Strizzo/LumonTasker/cad/output/v28_integrated_top/README.md

# V28 — integrated printer-bay top

User requested cancellation of V27 to integrate the top now. V27 cancelled on layer1/805; device confirmed idle with heater targets zero. Clear the partial print, tower and purge line before any restart.

Top is now fused into the shell as a single solid. Removed the two top screw holes and matching heat-set bores. Finished outer height remains201mm. No separate top-cover print or twoM3x8 top screws required. Rear cover, retaining bars and rearward printer extraction remain unchanged. Front-down printing makes the top an upright wall, not a spanning roof; the earlier claim that a separate top was necessary was incorrect.

Retains V27 bottom support rise8.1mm and0.6mm total guide-gap reduction. Cradle remains a separate internal part. LED remains separate PETG insert. All solids/meshes valid and watertight; pairwise interference, rear extraction and switch swept clearance audits pass for the estimated body. These do not replace physical hardware validation.

Shell/logotype registered print coordinates updated together for the increased front-down footprint:175x192x161mm. Prepared shell,cradle+bars,rear cover,and optional bars-only projects. Slicer review and user/clear-bed confirmation required before replacement dispatch. No replacement sent yet.

## GUI slicing review

Integrated shell slices without a visible warning:10h20m,400.45g,805 layers,six filament changes. Supports15.88g (essentially unchanged from separate-top shell); added time/material is the top itself. Not dispatched. Await clear bed and user restart confirmation.

## Replacement started

User confirmed bed cleared. V28 integrated-top shell dispatched21 September17:04 local; device confirms active preparation and estimated finish22 September03:24. A2 light-grey body/A1 navy logo,bed leveling off,timelapse off.

## Print complete — 22 September

User confirms completion and provides a photo. Light grey ran out and was replaced by yellow; this shell is a fit-test prototype. User has only the earlier v26 trial cradle, not the refined cradle. Next prepared kit is `../v31_cradle_retention/02_cradle_and_bars.3mf`, with the approved taller/narrower cradle and a lower bar that captures its rear edge. No next print is authorized or dispatched. Final appearance should be redesigned/reviewed before spending the incoming white/navy filament on another shell.
