Strizzo/LumonTasker/cad/output/v36_outlet_alignment/README.md

# V36 physical outlet alignment correction

User reports V31 cradle fits well. With the printer seated in the printed prototype, move the enclosure paper aperture upward 3 mm; LED alignment is acceptable.

Applied to V35 desktop-terminal assembly: paper opening remains 90 x 14 mm, centre Z moves from 130.1 to 133.1 mm (edges 126.1–140.1 mm). Cradle, printer pose and LED stay unchanged. This is the latest physical correction, superseding earlier outlet-position estimates.

Shell is one valid watertight solid; unchanged volume and new opening clearance verified. All other components are copied unchanged from V35. STEP is ready for Fusion review; not yet imported/saved in Fusion. STL is in assembly coordinates, not a sliced print release. No print dispatched.

Current prototype remains useful for retention, feed/cut, cable and rear-service tests. Secured retention and those functional checks remain pending. Final shell waits for final filaments and remaining fit checks.
