Strizzo/LumonTasker/cad/output/v37_logo_spacing/README.md

# V37 logo spacing

Physical prototype feedback: N too close to O. Moved N 0.3 mm right; O–N bounding gap increases from 0.294 to 0.594 mm, comparable to neighbouring gaps. Updated shell recess together with coloured logo. All other geometry inherited unchanged from V36, including paper opening raised 3 mm and unchanged LED.

Shell valid single solid, logo components valid and mutually non-overlapping; shell and logo STL watertight. STEP ready for Fusion synchronization, not yet imported. Assembly STLs are not oriented/sliced print releases. No print dispatched.

User reports final filaments arrived. Exact brands/materials/colours and current slot loading asked, awaiting reply. Secured retention and feed/cut/service checks still pending.
