Strizzo/LumonTasker/cad/output/v43_integral_display_mounts/README.md

# V43 — four integral display mounts

The user proposes merging the four mount arms into the case because the display and attached Pi enter from the front. The revised CAD does this: four rear M3×6 screws into the display's original metal lugs, with no separate brackets, four case-side screws or four case-side heat-set inserts. The original 3.9 mm pad thickness and nominal2.1 mm thread engagement remain; actual screw length and manufacturer2.5 mm thread-depth limit must be respected.

The white recessed seat, accepted193.4×111.4 mm opening withR8.2 corners,1 mm glass recess and visible black glass border stay unchanged. No navy bezel or front lip. Rear screw access is required for assembly and service, then the unplugged display/Pi withdraw through the front.

CAD results: revised body is a single valid watertight solid. All four screw bores, head recesses and bearing lands pass. Exact front insertion/extraction sweeps of nominal glass, chassis and attached Pi are clear with the INTEGRAL MOUNTS LEFT IN PLACE. Component intersections and nominal Pi margin are clear. A simplified Pi block in the image is not a detailed connector model.

Separate flat brackets were useful for the inexpensive V40 mount test and print without supports. Integrated overhanging arms can require local supports in the full-body print; orientation/support removal still needs slicer review. No support-free claim is made for V43. The full body is not released for printing yet.

The already printed frame and four brackets are still useful to verify the unchanged metal lug pattern, bearing planes and screw engagement before fixing those details in a large case. Only the glass contour is physically confirmed so far. The precise mounting stack and actual tool/cable clearances remain unconfirmed.

The unresolved internal-power choice and provisional cable-volume/divider clash237.48 mm³ remain recorded. No assumption about purchased internal power hardware has been made. The navy printer-base job is unaffected; no new print sent and Fusion stays closed/latest savedV39.

Files: whole_enclosure_review.step; whole_enclosure_with_hardware.step; tub_left.step; audit.json; integral_mounts_rear.png (cropped CAD view of the panel from inside).
