Strizzo/LumonTasker/cad/output/v50_full_display_preflight/README.md

# V50 full-display preparation

V49 corner samples are physically accepted. Selected support gap:0.12mm.

## Ready sliced plate

`02_V50_display_roof_and_hatch.3mf` and matching `.gcode.3mf` contain the exact
existing aligned display roof and rear hatch. Bambu native slice/preview passes:
3h53m40s,118.64g,whiteA2 only. See `roof_hatch_slice_review.json`.
User confirmed plate clear; job sent and accepted by P1S, startup0/114, ETA22:47 local. Bed levelling/timelapseOFF. Bambu showed Finished 114/114 and user confirms both parts intact and plate clear on 25 September; see roof_hatch_print_dispatch.json.

## Full enclosure audit

`audit.json` records full-body front-down bounds and compact screwdriver access.
The body STL is for review only: legacy internal PSU mounts/divider remain.
Power architecture must be confirmed before changing them or releasing the
body. The entire full enclosure is NOT yet released. New display mount geometry
has not been synchronized into Fusion; roof/hatch match its savedV39 geometry.

Remaining parts:full display body,navy left base; separate PETG
LED diffuser if still needed. Accepted printer shell/cradle/base stay in use.
