Strizzo/LumonTasker/cad/output/v51_dc_inlet_panel/README.md

# V51 DC inlet glue panel

Current part: `dc_inlet_glue_panel.step`; current print project:
`02_DC_inlet_glue_panel.3mf`; native sliced file:
`02_DC_inlet_glue_panel.gcode.3mf`.

Nominal 10 mm socket neck, 10.2 mm bore, 5 mm inward sleeve, 2 mm radial wall.
20m27s estimate, 5.62 g cotton white PLA, no supports. Dispatched 26 September after user confirmed the
plate clear; cotton white A2, auto bed levelling and timelapse off. Completion
and physical fit are pending. Dry fit the socket and case recess before applying glue.

Files named `draft` or `DRAFT_NOT_RELEASED` are earlier superseded geometry,
without the user's final glue sleeve, and should not be printed.
