Strizzo/LumonTasker/cad/output/v51_petg_led_insert/README.md

# Translucent PETG LED insert — 26 September 2026

Final separate LED insert, using the geometry of the accepted earlier PLA fit trial.
No enclosure/Fusion geometry revision: the current saved full assembly contains this insert already.

- Physical material: translucent PETG, AMS A3 (user confirmed).
- Device A3 registration verified: PETG, K0.040.
- Project has one filament, extruder 1. Map it to **A3** when sending.
- Native slice: 11m30s total, 0.61 g, 17 layers at 0.2 mm.
- Generic PETG preset: 255 C nozzle / 70 C textured PEI bed.
- Flange down; no support or prime tower; 0.8 mm front face.
- Native preview: continuous first-layer flange, short bridge at layer 14, complete face.
- **Dispatched** after user confirms whole plate clear; Device shows matching job accepted and bed heating. Completion and optical fit pending.
- At launch: bed levelling and timelapse OFF, as requested.

Insert from the inside/rear into the printer bay's light opening. The wider flange
stays inside. Dry-fit and check the blue light before placing small adhesive points
on the flange; keep glue away from the light cavity and native buttons.
