Strizzo/LumonTasker/cad/output/v18_colored.png

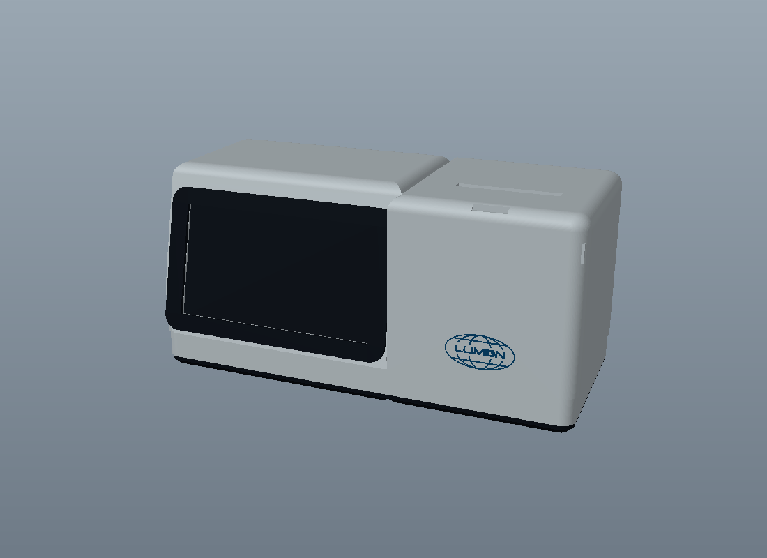
cad/output/v18_colored.png
