Strizzo/LumonTasker/cad/output/v18_screen_corner.png

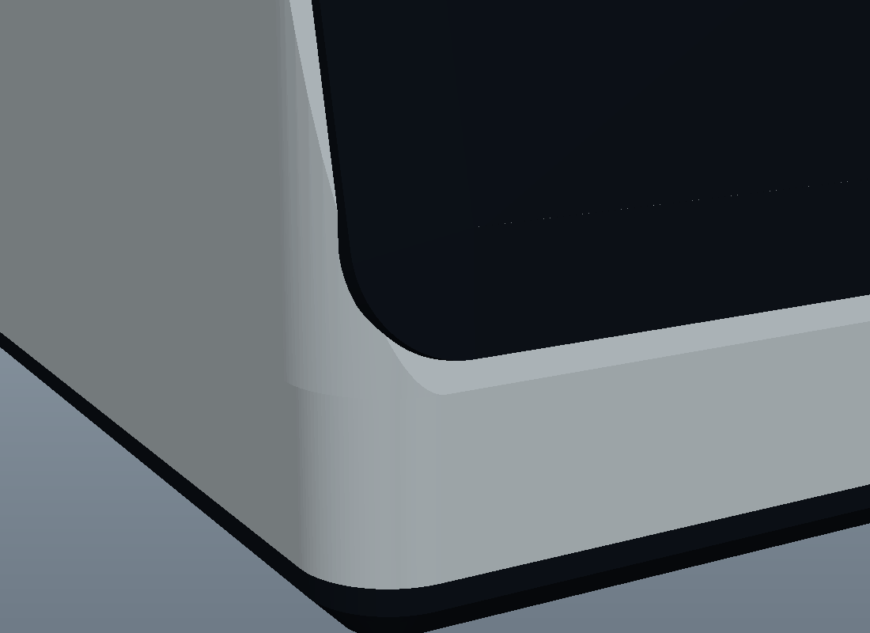
cad/output/v18_screen_corner.png
