Strizzo/LumonTasker/cad/output/v19/exploded.png

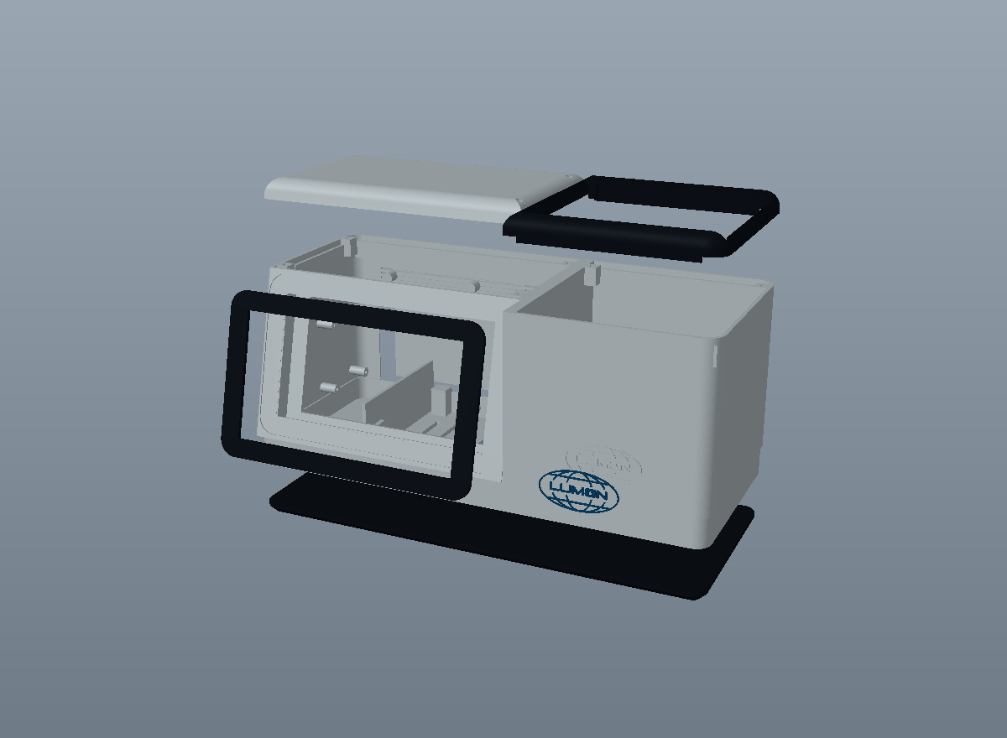
cad/output/v19/exploded.png
