Strizzo/LumonTasker/cad/output/v20_front/exploded.png

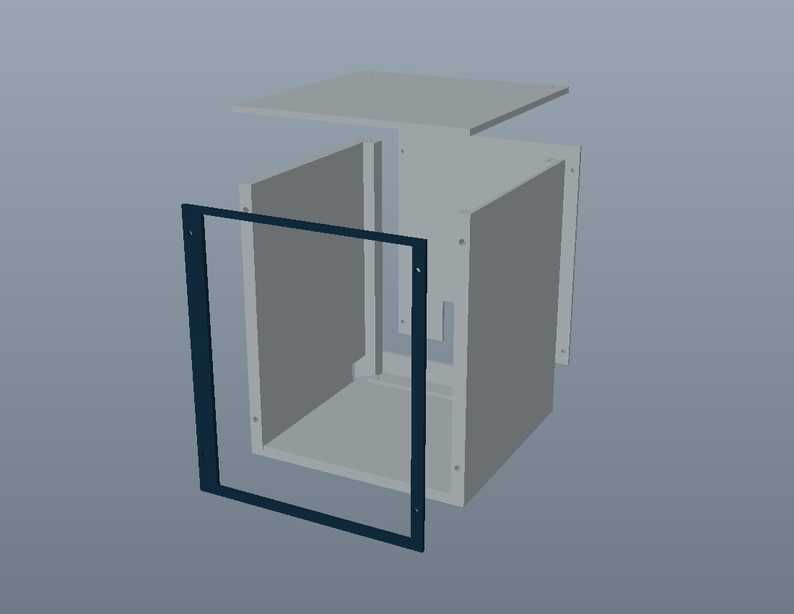
cad/output/v20_front/exploded.png
