Strizzo/LumonTasker/cad/output/v20_integral_front/exploded.png

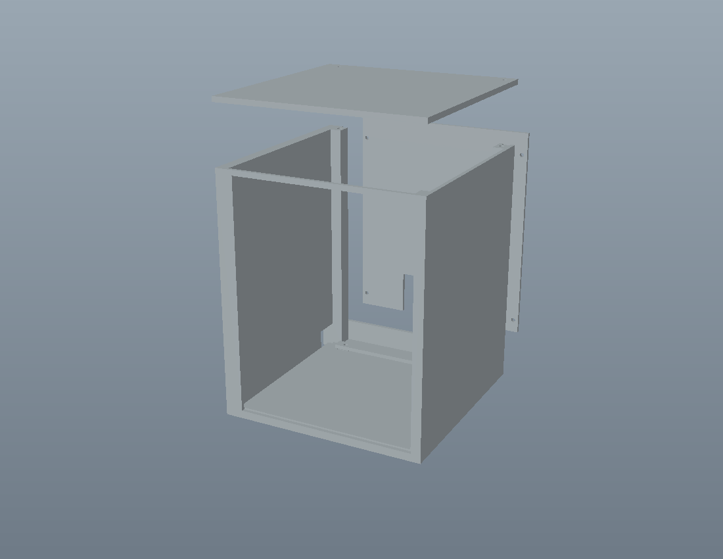
cad/output/v20_integral_front/exploded.png
