Strizzo/LumonTasker/cad/output/v21_rear_loading/rear_retention.png

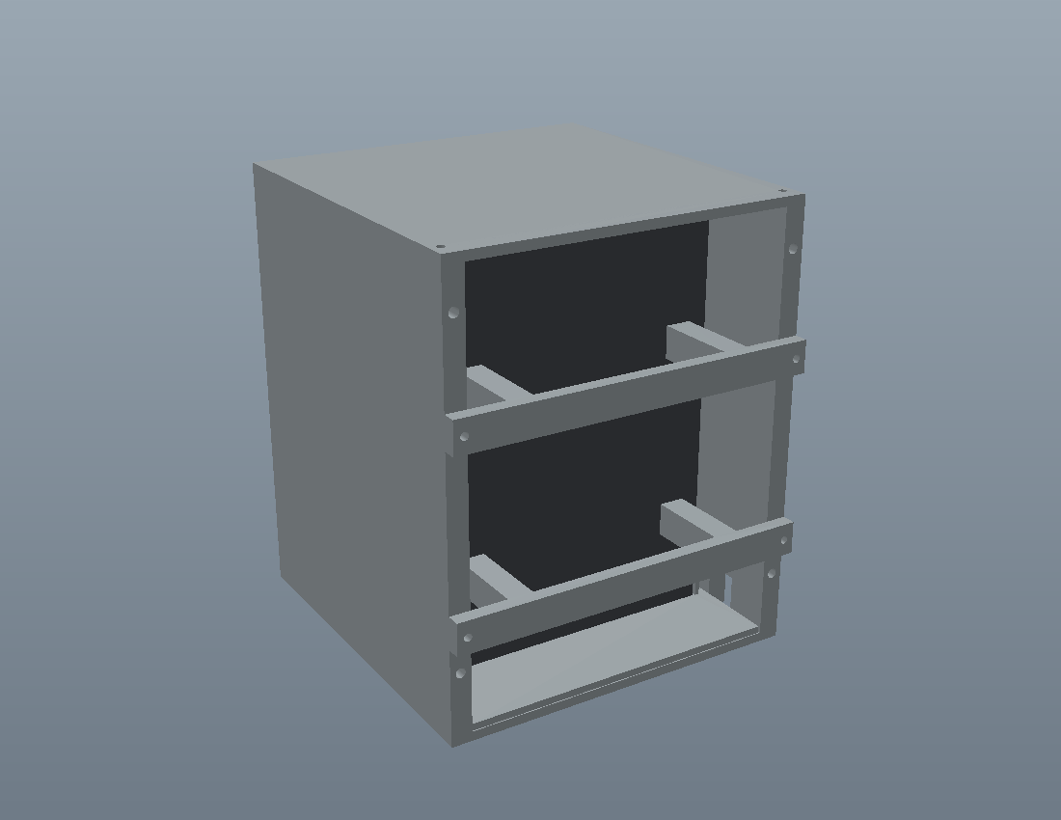
cad/output/v21_rear_loading/rear_retention.png
