Strizzo/LumonTasker/cad/output/v22_printer_bay/finished_appearance_concept.png

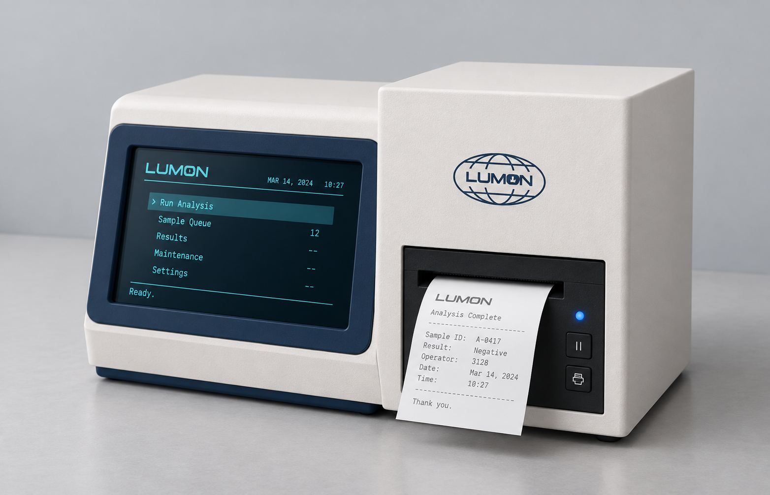
cad/output/v22_printer_bay/finished_appearance_concept.png
