Strizzo/LumonTasker/cad/output/v23_upper_output/exploded.png

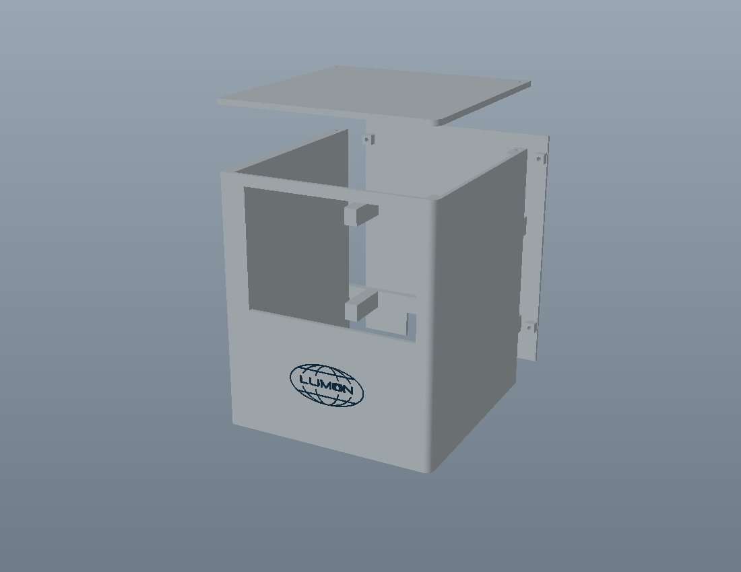
cad/output/v23_upper_output/exploded.png
