Strizzo/LumonTasker/cad/output/v23_upper_output/finished_appearance_concept.png

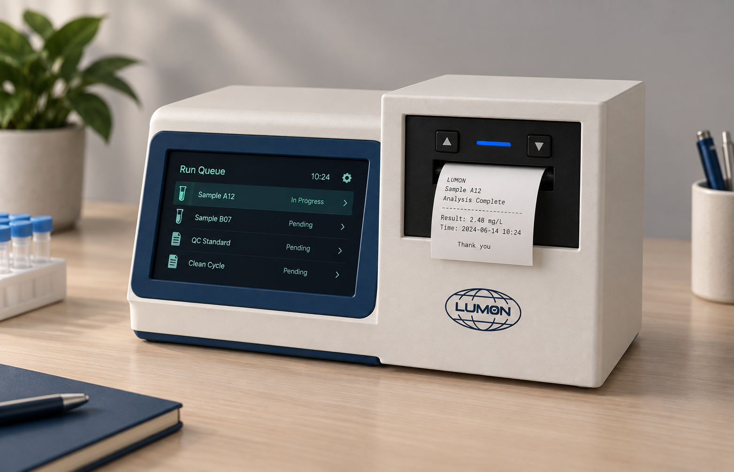
cad/output/v23_upper_output/finished_appearance_concept.png
