Strizzo/LumonTasker/cad/output/v23_upper_output/whole_enclosure_study.png

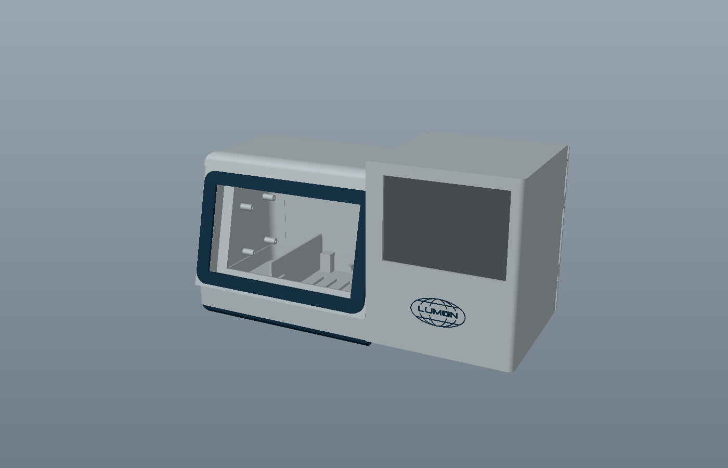
cad/output/v23_upper_output/whole_enclosure_study.png
