Strizzo/LumonTasker/cad/output/v28_integrated_top/exploded.png

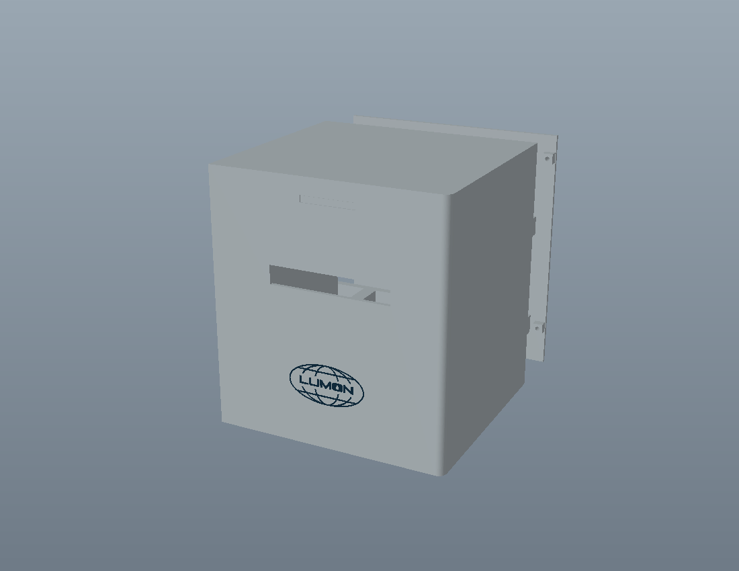
cad/output/v28_integrated_top/exploded.png
