Strizzo/LumonTasker/cad/output/v28_integrated_top/whole_enclosure_review.png

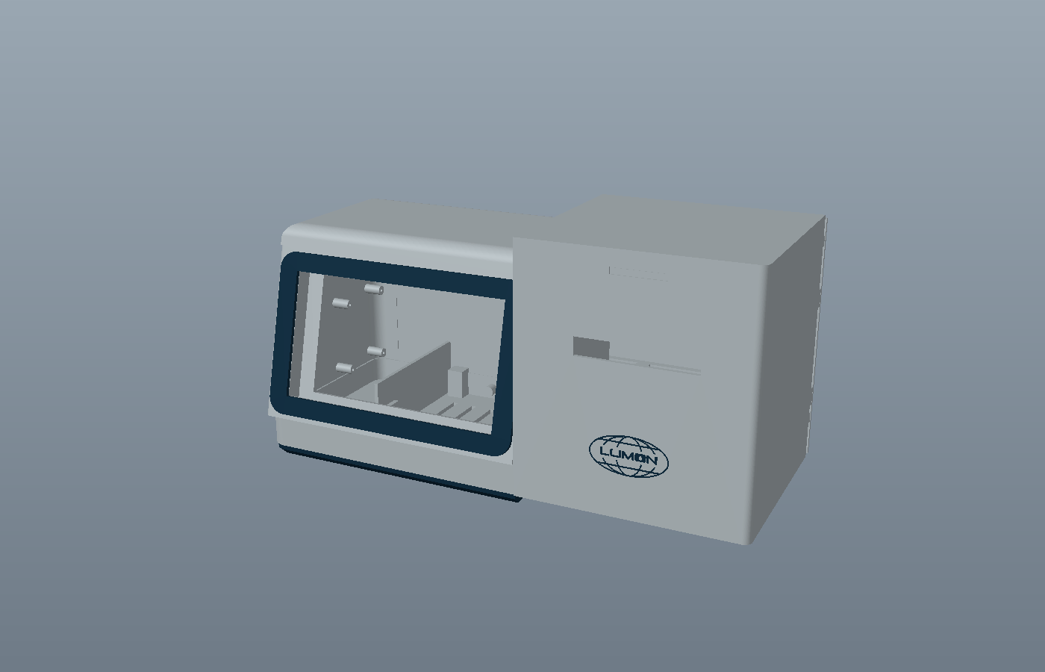
cad/output/v28_integrated_top/whole_enclosure_review.png
