Strizzo/LumonTasker/cad/output/v31_cradle_retention/cradle_retention_detail.png

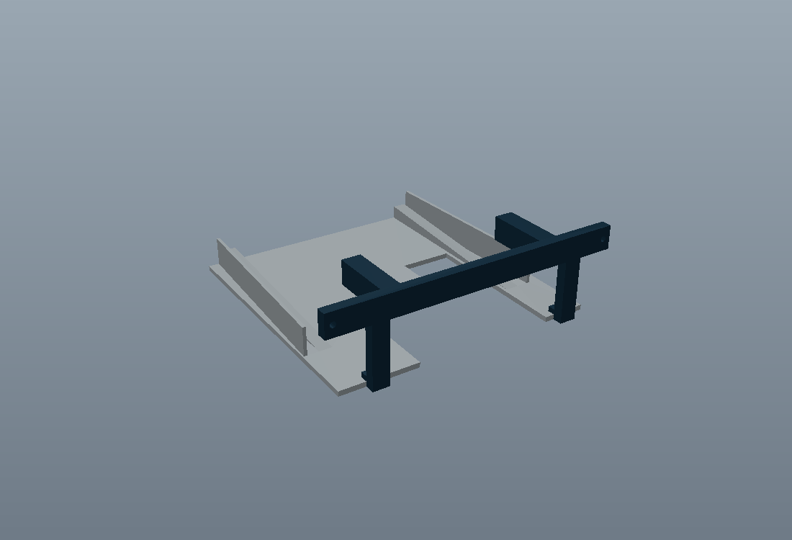
cad/output/v31_cradle_retention/cradle_retention_detail.png
