Strizzo/LumonTasker/cad/output/v32_equal_height/before_front.png

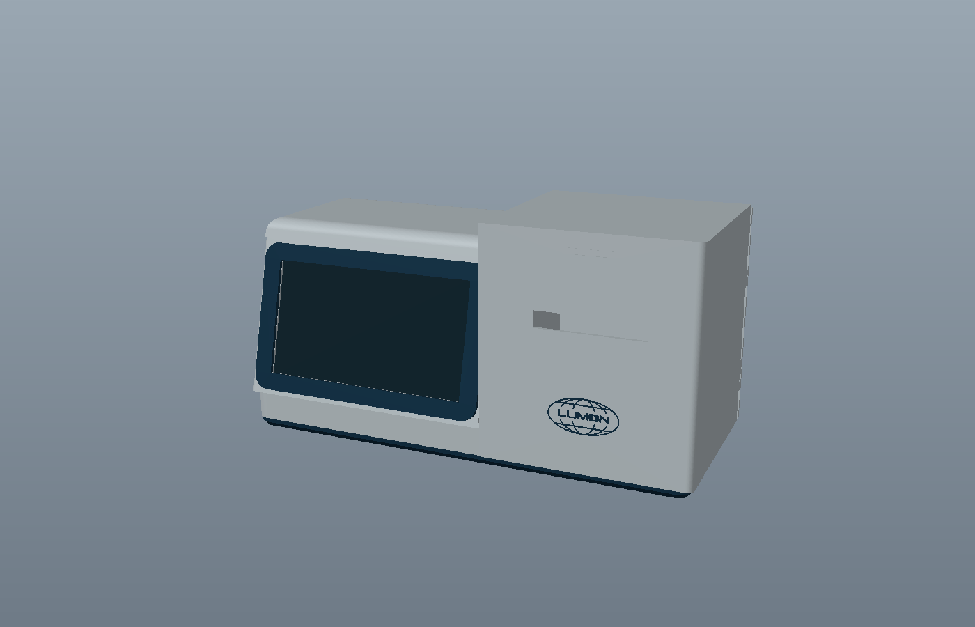
cad/output/v32_equal_height/before_front.png
