Strizzo/LumonTasker/cad/output/v32_equal_height/equal_height_rear.png

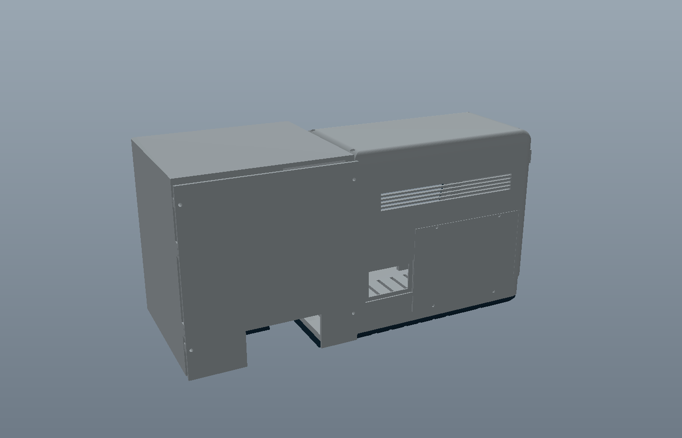
cad/output/v32_equal_height/equal_height_rear.png
