Strizzo/LumonTasker/cad/output/v33_unified_body/before_front.png

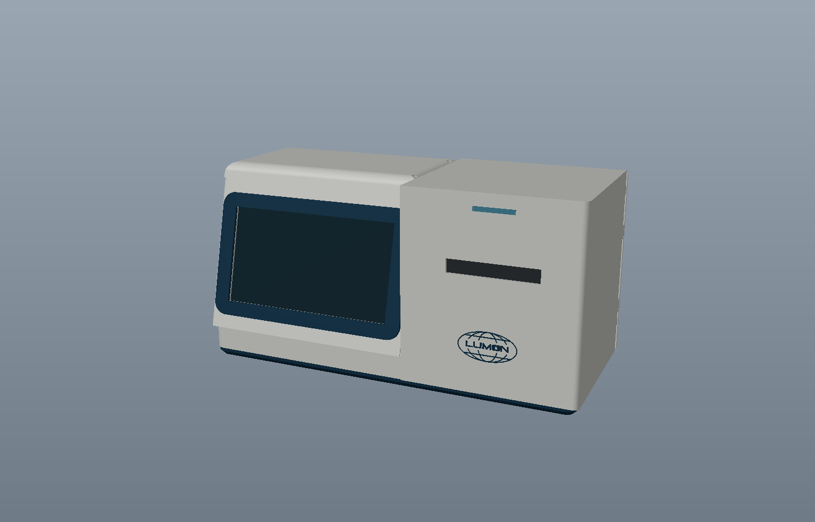
cad/output/v33_unified_body/before_front.png
