Strizzo/LumonTasker/cad/output/v33_unified_body/unified_front.png

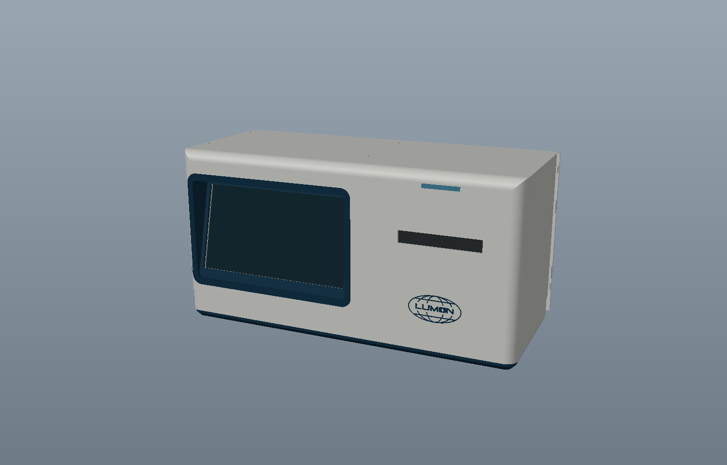
cad/output/v33_unified_body/unified_front.png
