Strizzo/LumonTasker/cad/output/v33_unified_body/unified_rear.png

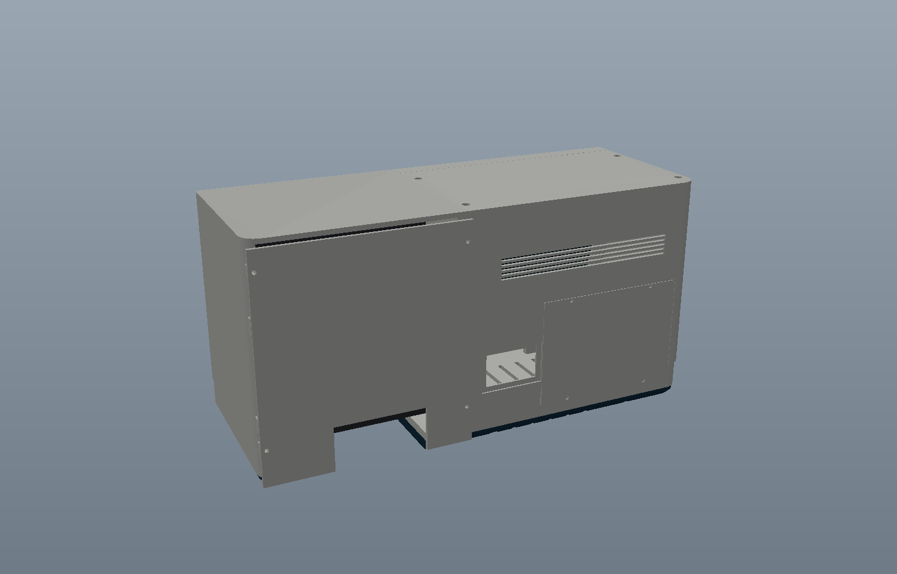
cad/output/v33_unified_body/unified_rear.png
