Strizzo/LumonTasker/cad/output/v33_unified_body/unified_straight_front.png

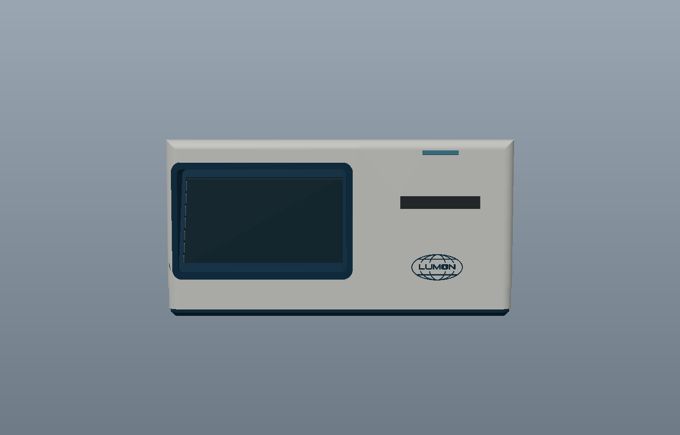
cad/output/v33_unified_body/unified_straight_front.png
