Strizzo/LumonTasker/cad/output/v34_sloped_connected_roof/sloped_roof.png

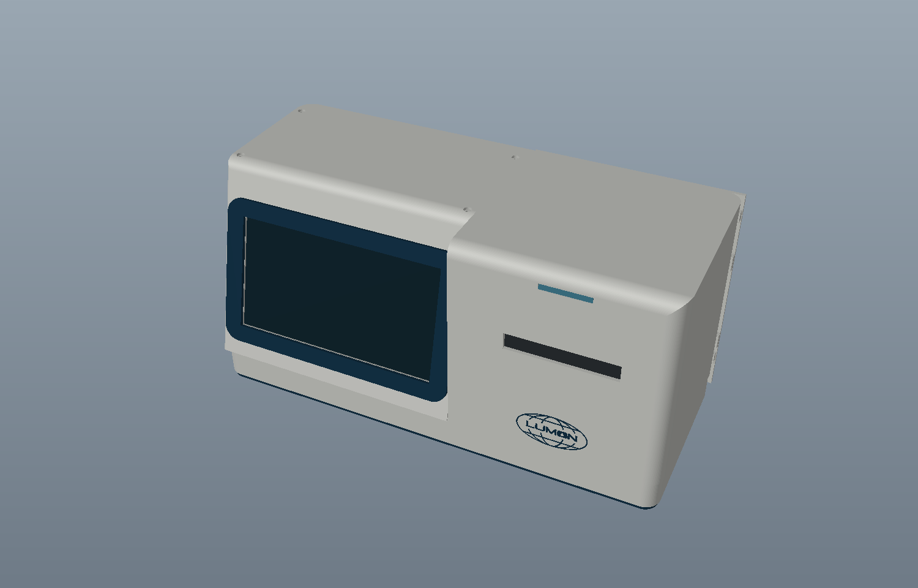
cad/output/v34_sloped_connected_roof/sloped_roof.png
