Strizzo/LumonTasker/cad/output/v35_desktop_terminal/sloped_rear.png

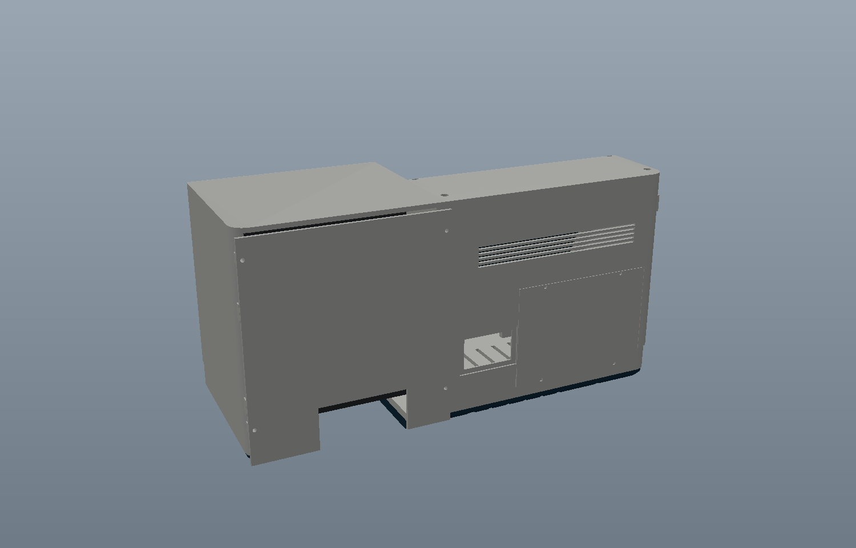
cad/output/v35_desktop_terminal/sloped_rear.png
