Strizzo/LumonTasker/cad/output/v38_integrated_rear/cover_inside.png

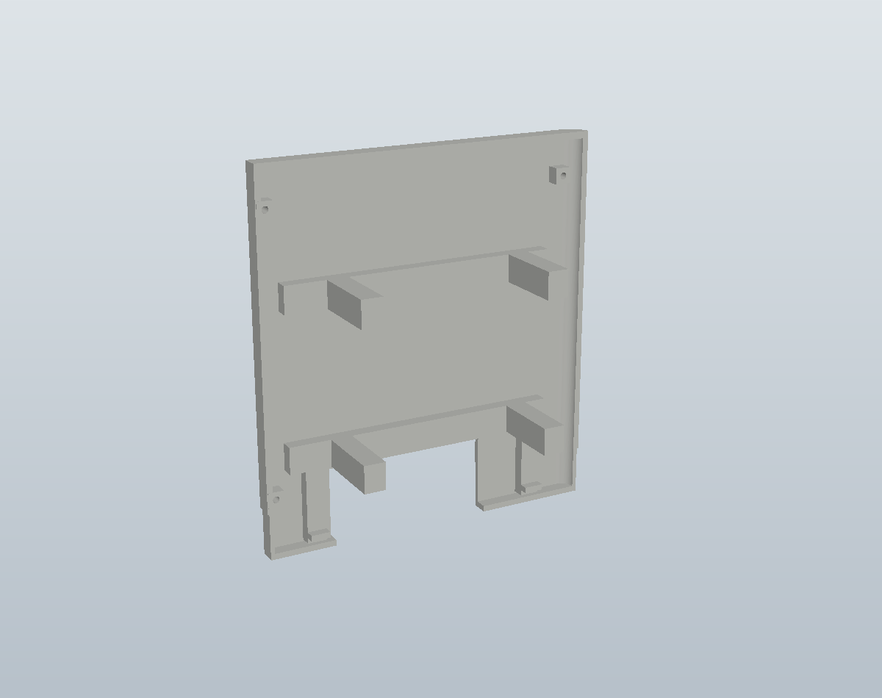
cad/output/v38_integrated_rear/cover_inside.png
