Strizzo/LumonTasker/cad/output/v38_integrated_rear/rear_exploded.png

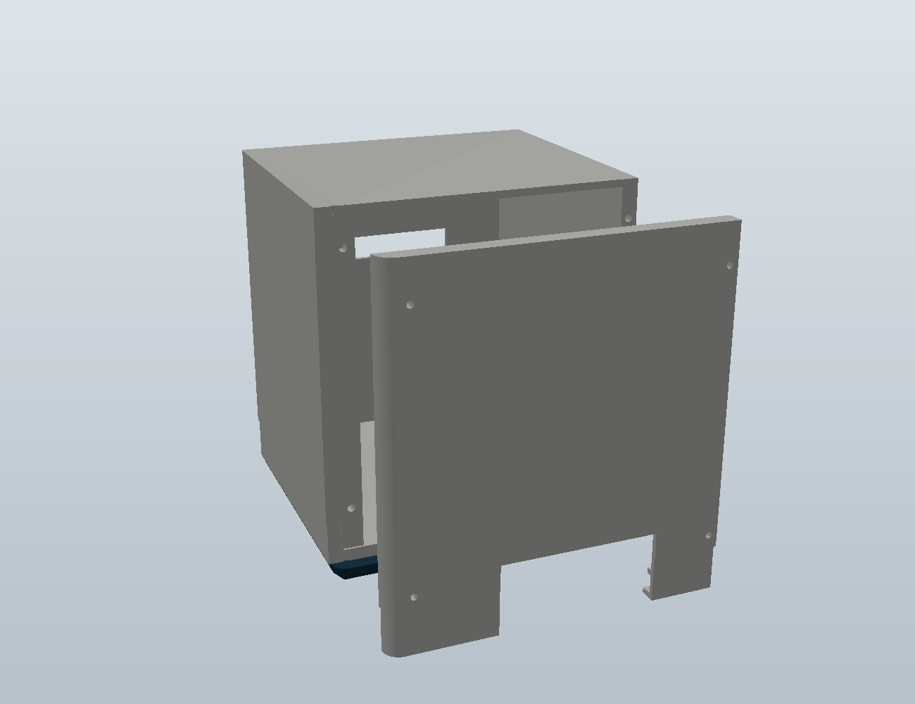
cad/output/v38_integrated_rear/rear_exploded.png
