Strizzo/LumonTasker/cad/output/v39_aligned_rear/aligned_rear.png

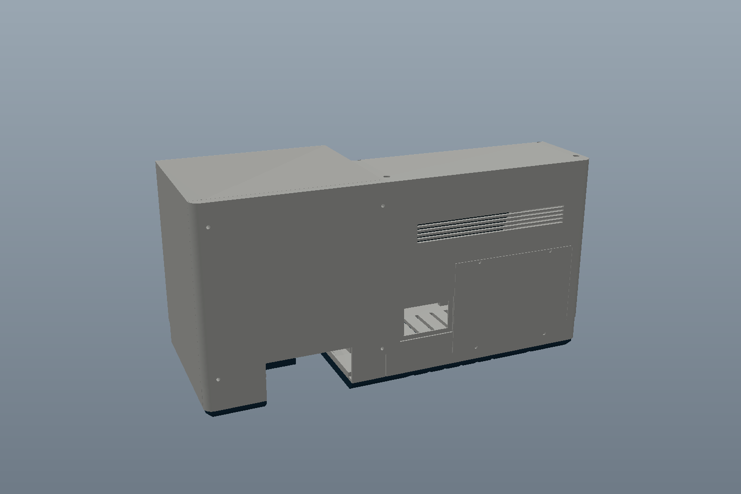
cad/output/v39_aligned_rear/aligned_rear.png
