Strizzo/LumonTasker/cad/output/v39_aligned_rear/aligned_roof.png

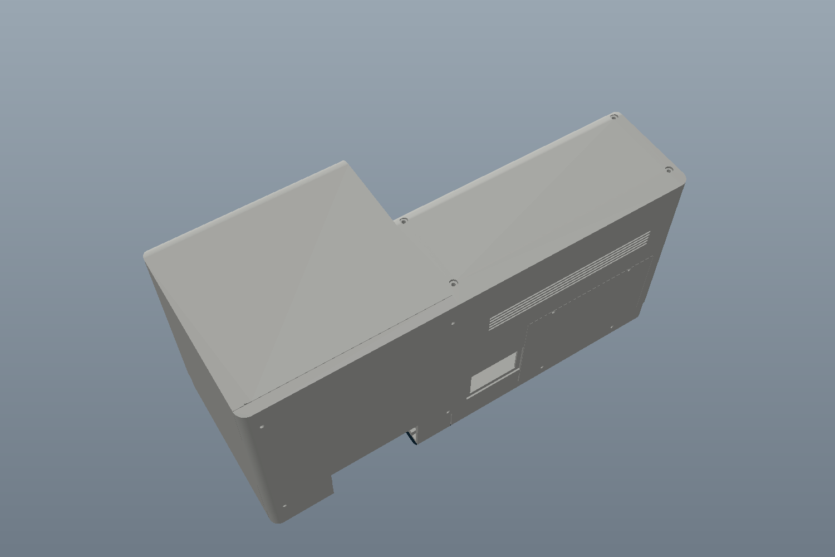
cad/output/v39_aligned_rear/aligned_roof.png
