Strizzo/LumonTasker/cad/output/v40_display_mount/fit_kit_rear.png

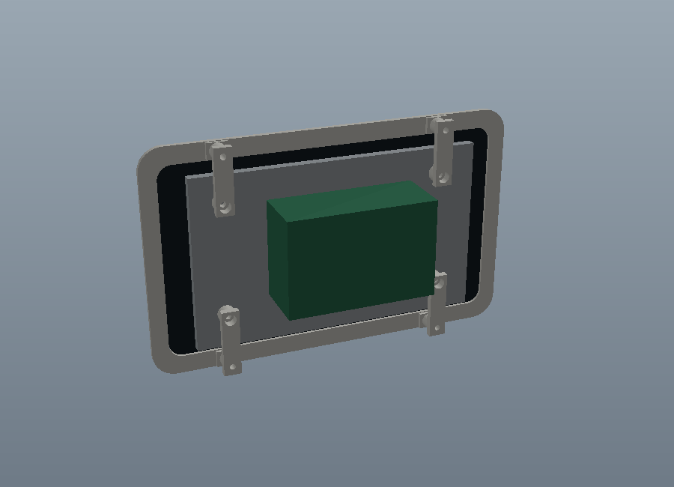
cad/output/v40_display_mount/fit_kit_rear.png
