Strizzo/LumonTasker/cad/output/v41_recessed_glass/recessed_glass_front.png

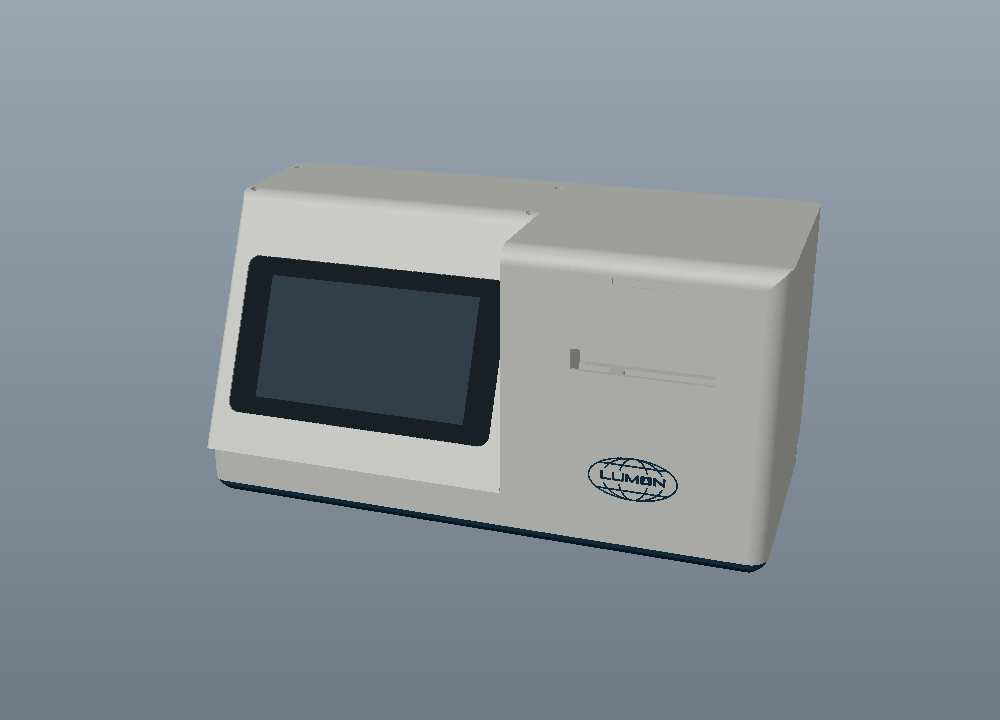
cad/output/v41_recessed_glass/recessed_glass_front.png
