Strizzo/LumonTasker/cad/output/v46_display_seat_fit/integral_fit_frame.png

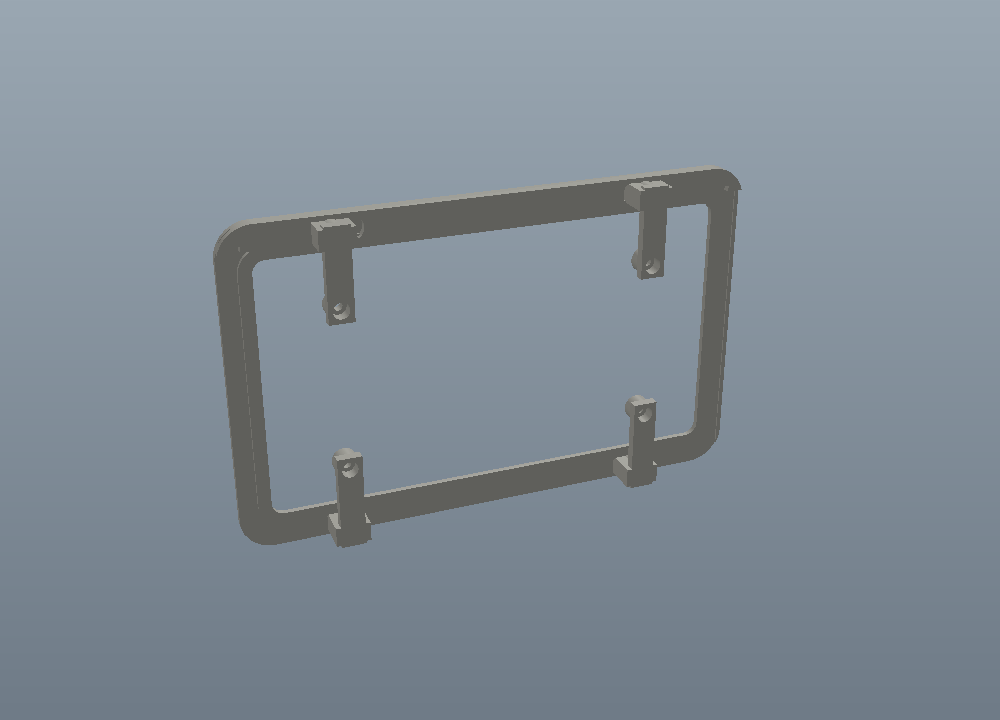
cad/output/v46_display_seat_fit/integral_fit_frame.png
