Strizzo/LumonTasker/cad/output/v50_full_display_preflight/body_front_down_audit.png

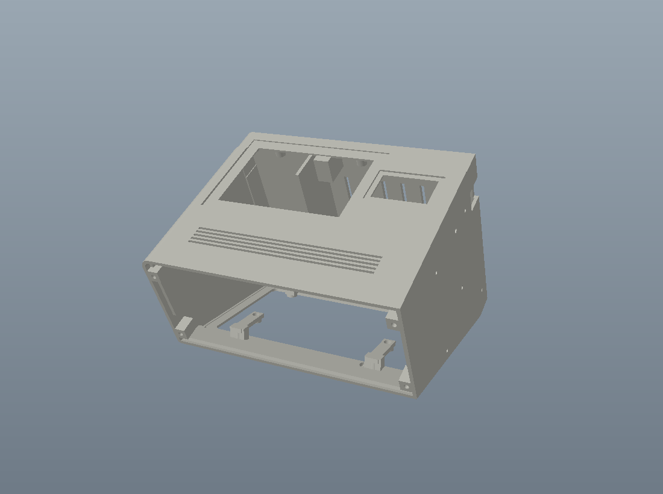
cad/output/v50_full_display_preflight/body_front_down_audit.png
