Strizzo/LumonTasker/cad/output/v50_full_display_preflight/body_rear_audit.png

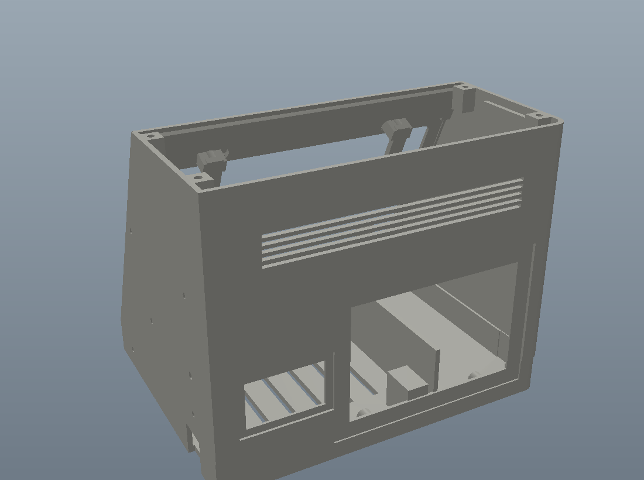
cad/output/v50_full_display_preflight/body_rear_audit.png
