Strizzo/LumonTasker/cad/output/v51_dc_inlet_panel/dc_inlet_glue_panel_front.png

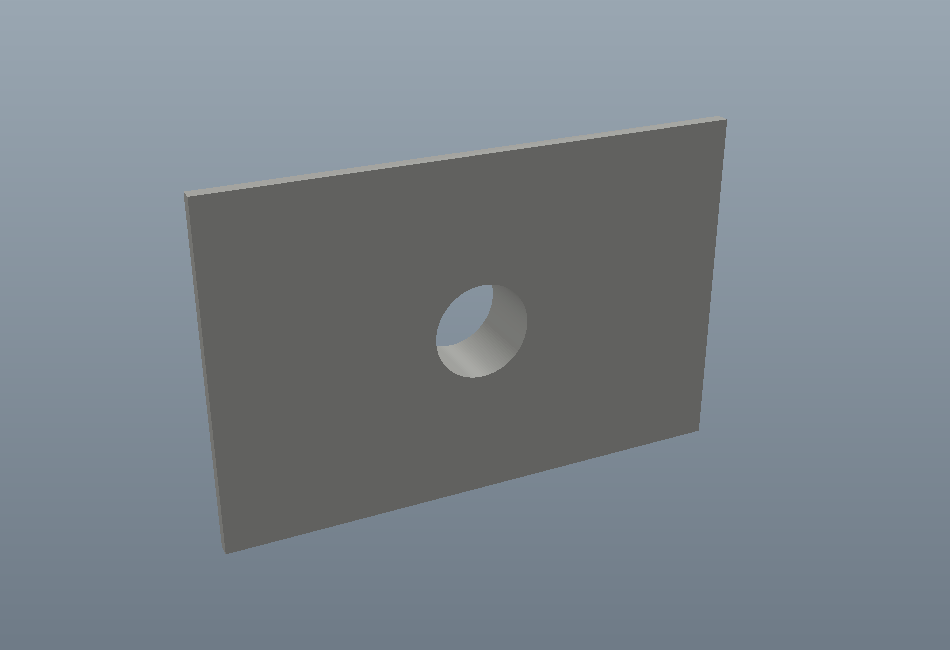
cad/output/v51_dc_inlet_panel/dc_inlet_glue_panel_front.png
