Strizzo/LumonTasker/cad/output/v51_dc_inlet_panel/dc_inlet_glue_panel_rear.png

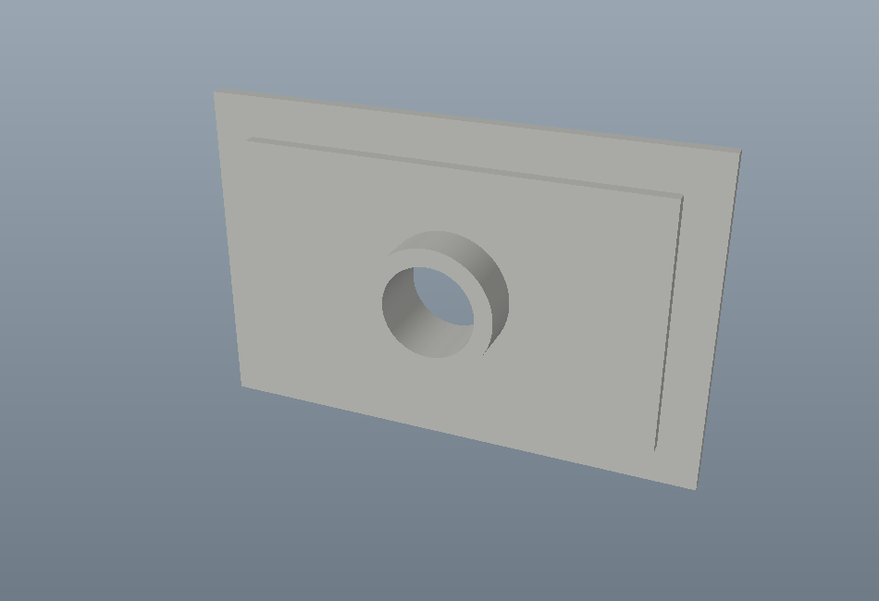
cad/output/v51_dc_inlet_panel/dc_inlet_glue_panel_rear.png
