Strizzo/LumonTasker/files/blockout_views.png

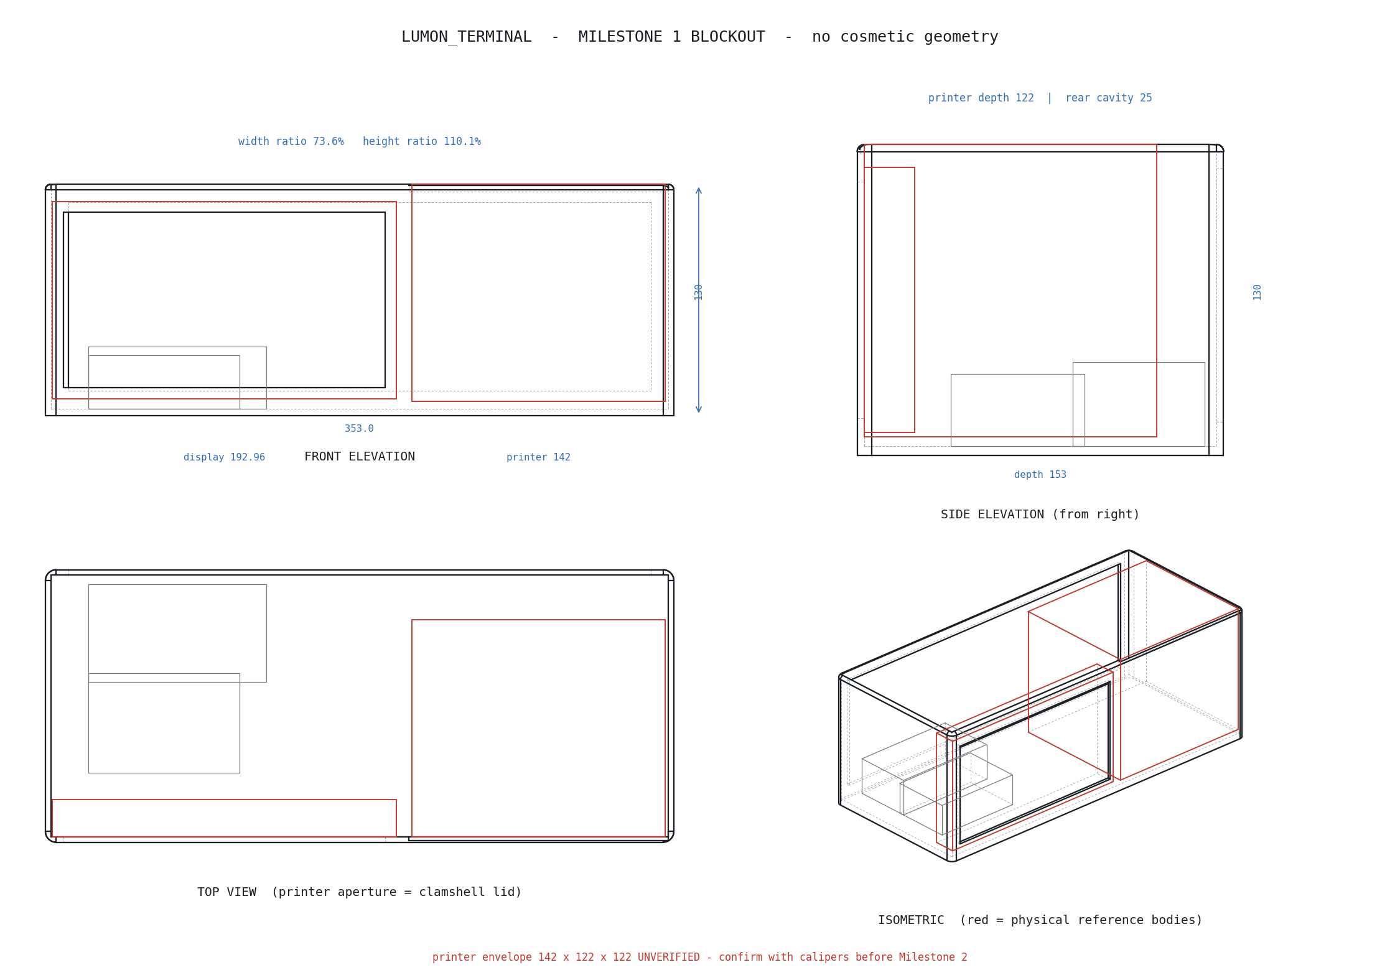
files/blockout_views.png
