Strizzo/LumonTasker/files/corner_zoom.png

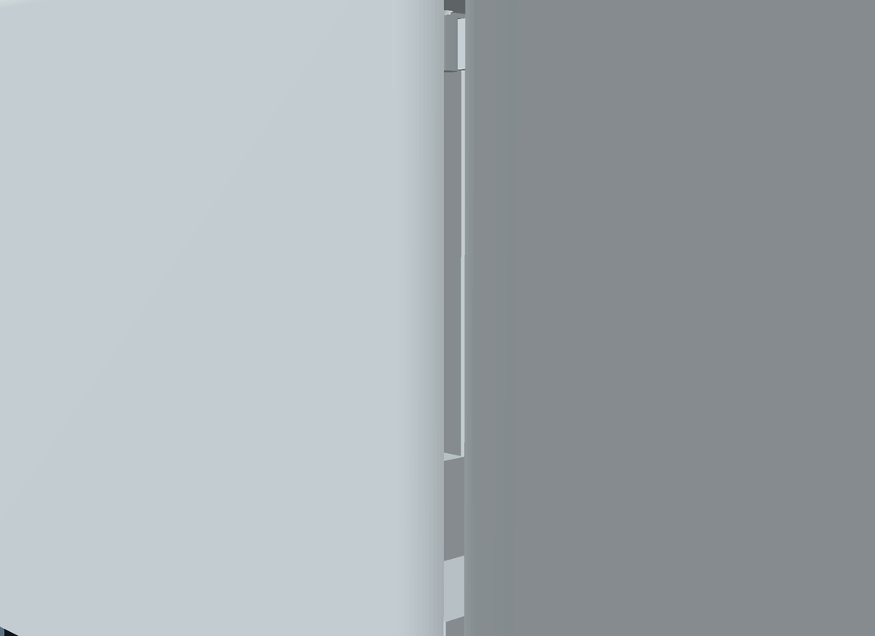
files/corner_zoom.png
