Strizzo/LumonTasker/files/lockup_90mm.png

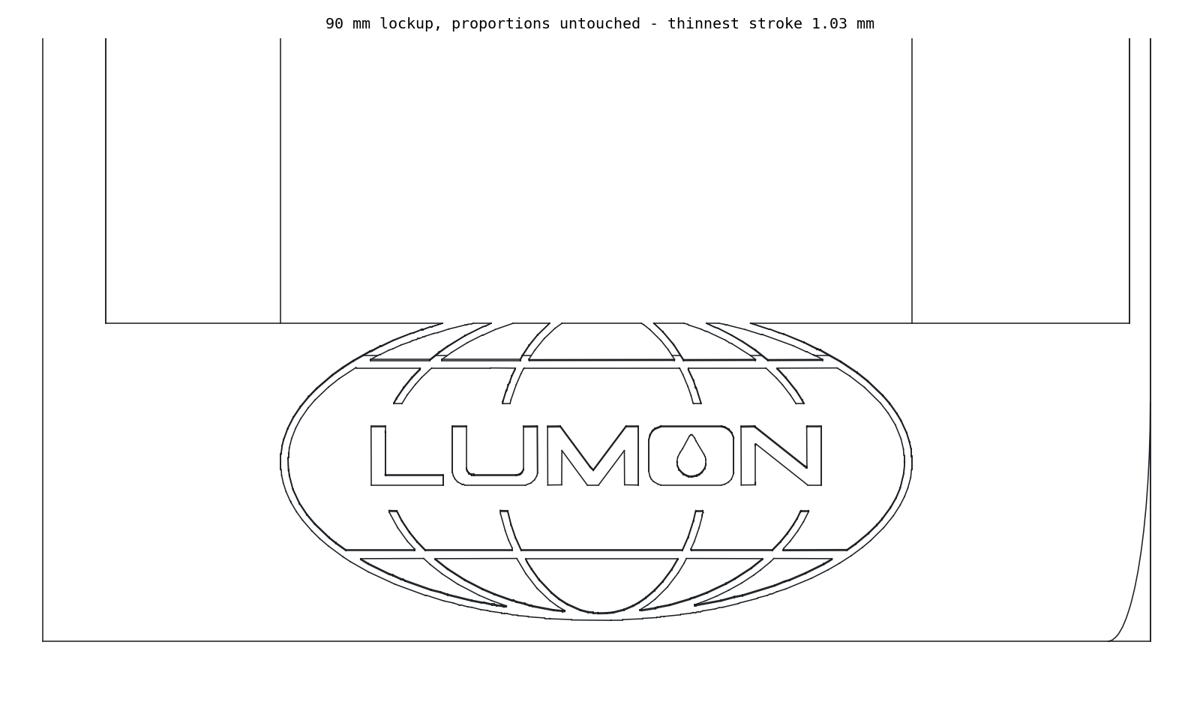
files/lockup_90mm.png
