Strizzo/LumonTasker/files/mark_in_wall.png

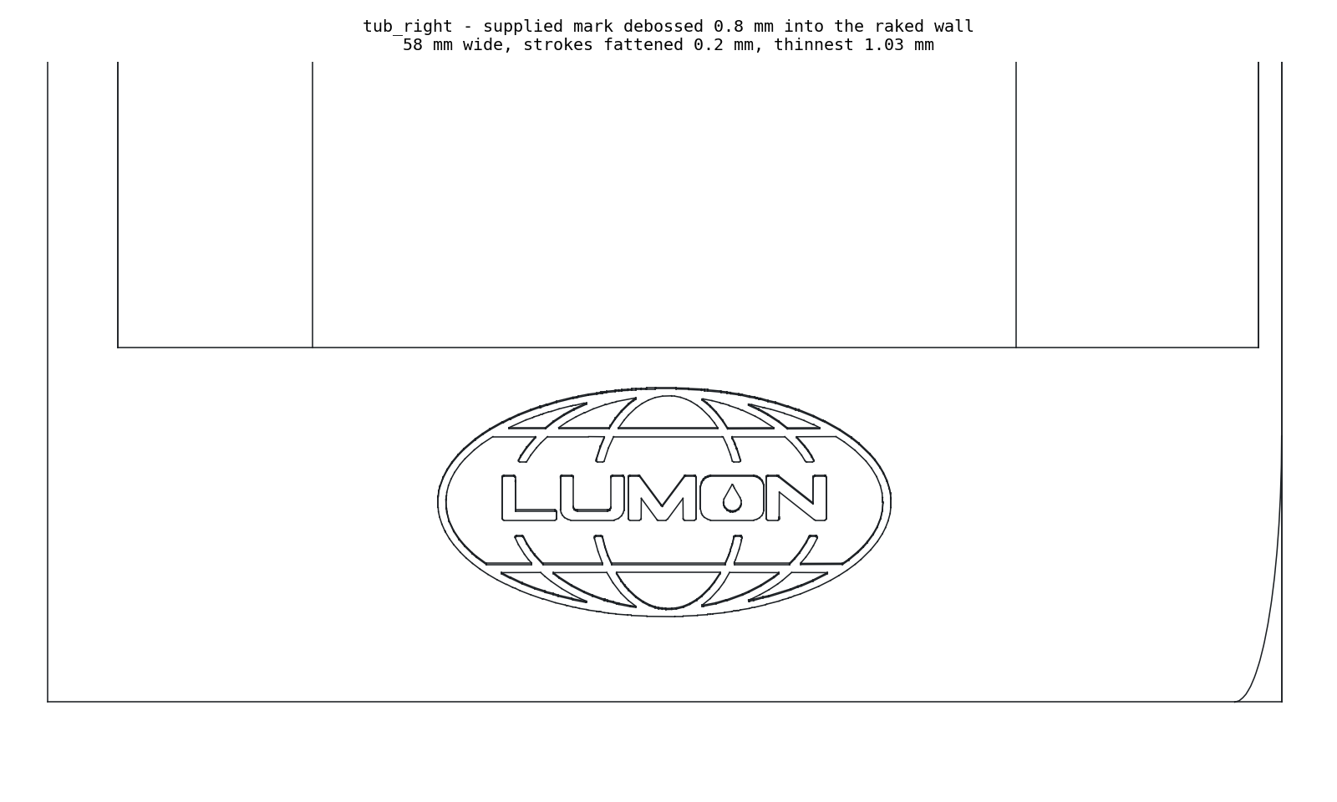
files/mark_in_wall.png
