Strizzo/LumonTasker/files/mark_options.png

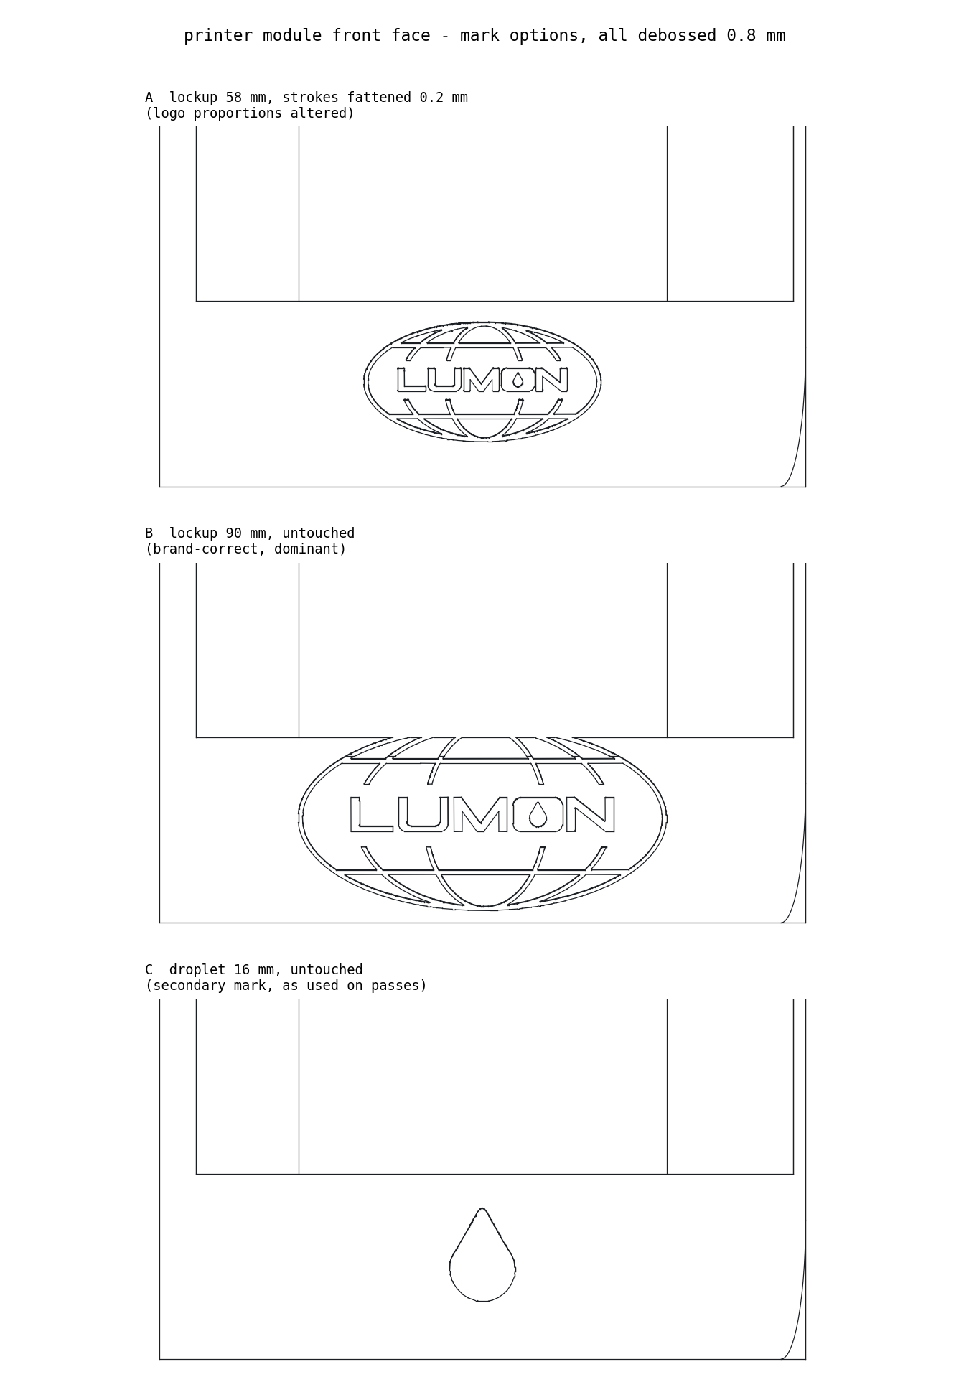
files/mark_options.png
