Strizzo/LumonTasker/files/render_hero.png

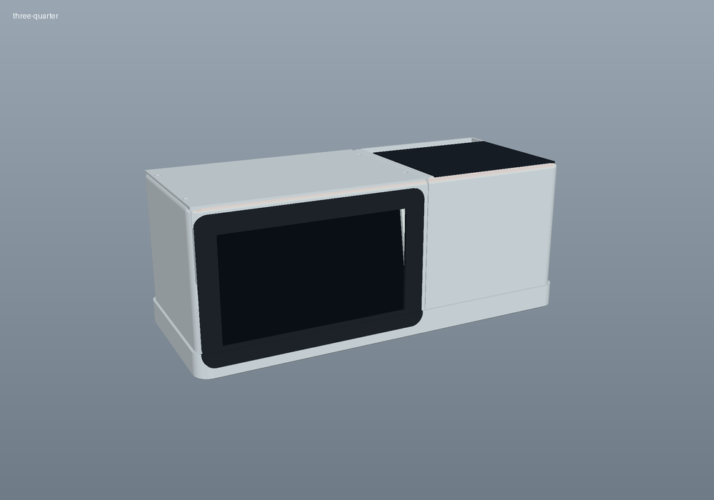
files/render_hero.png
