Strizzo/LumonTasker/files/render_sheet.png

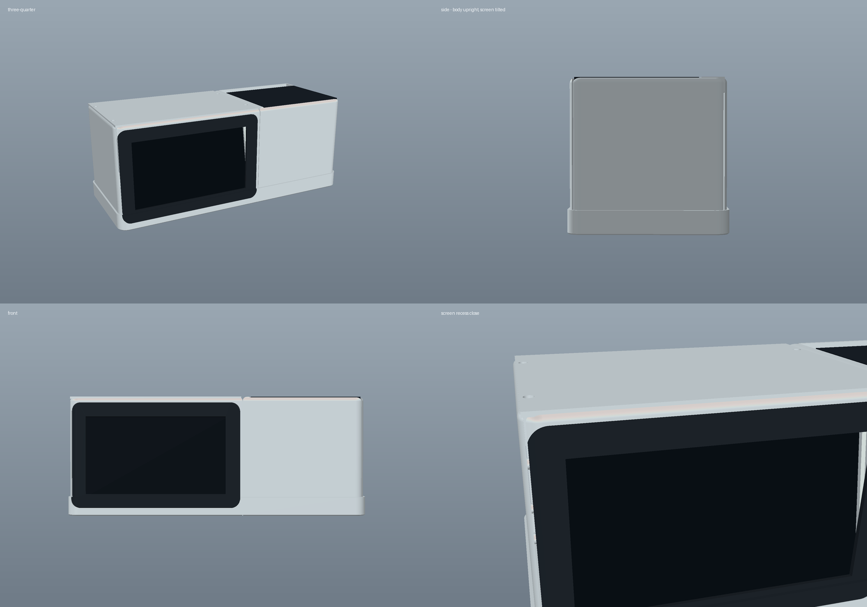
files/render_sheet.png
