Strizzo/LumonTasker/files/traced_mark_proof.png

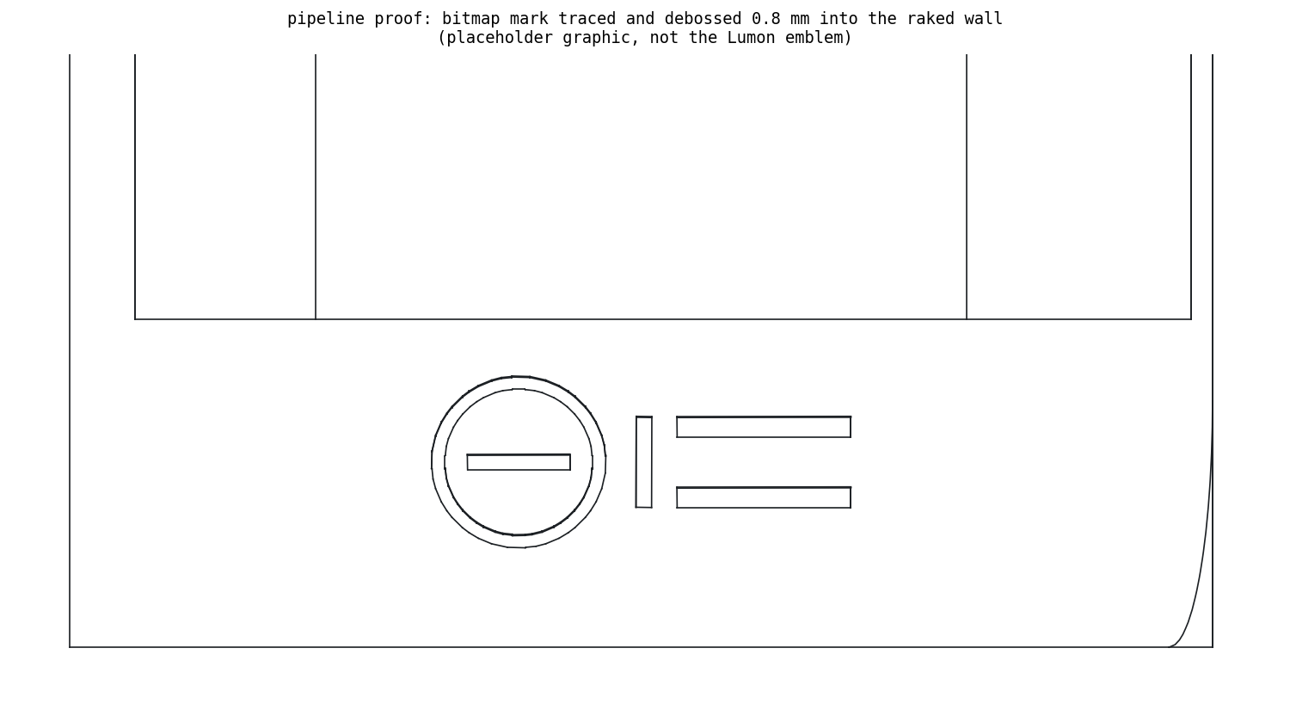
files/traced_mark_proof.png
