Strizzo/LumonTasker/files/v4_views.png

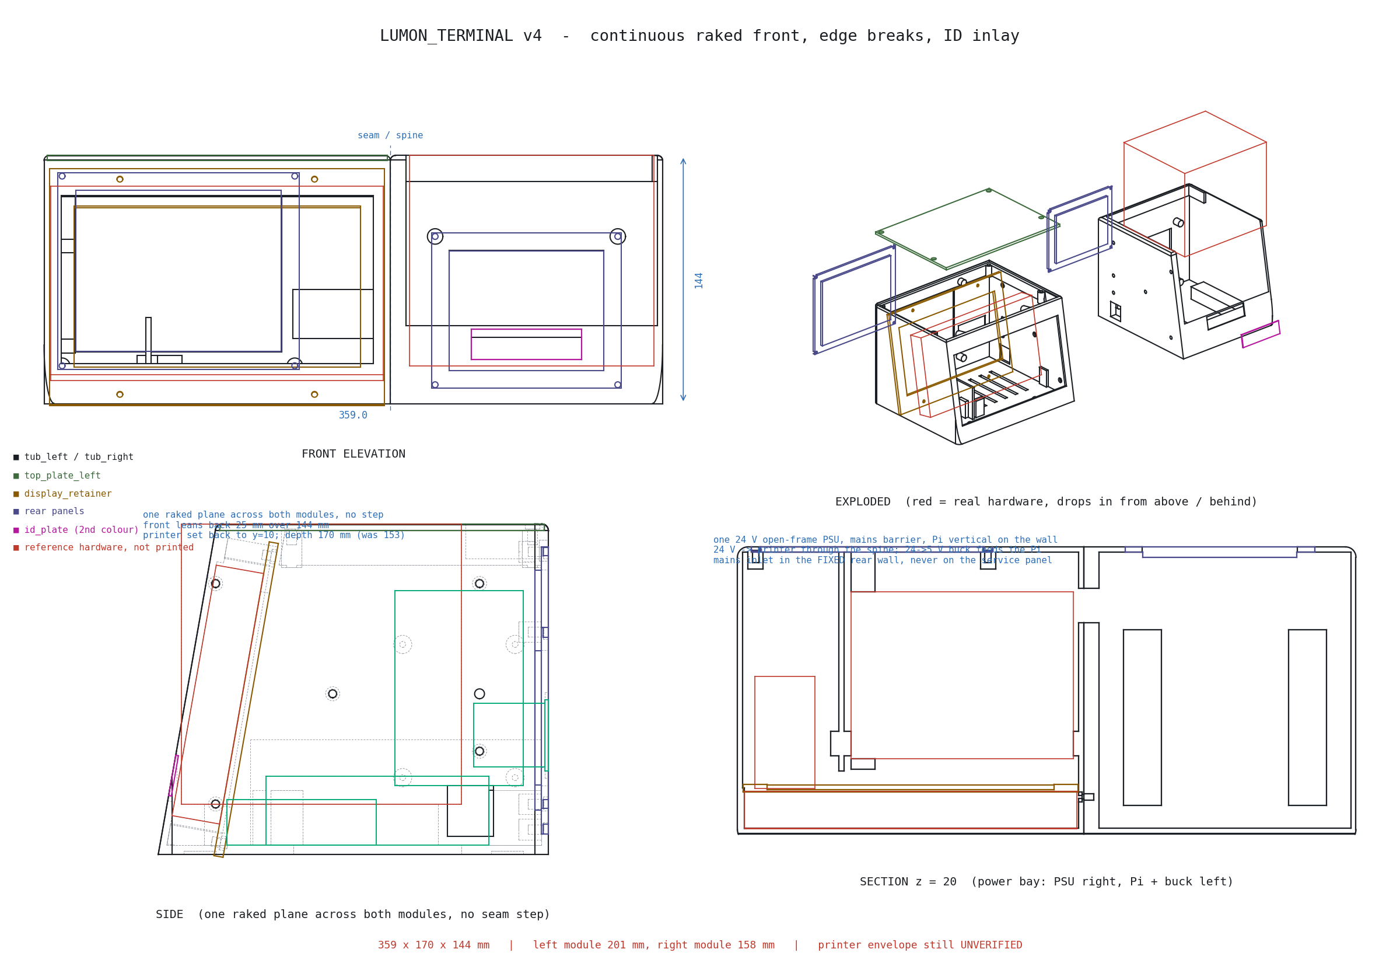
files/v4_views.png
