Strizzo/LumonTasker/files/v5_mark_detail.png

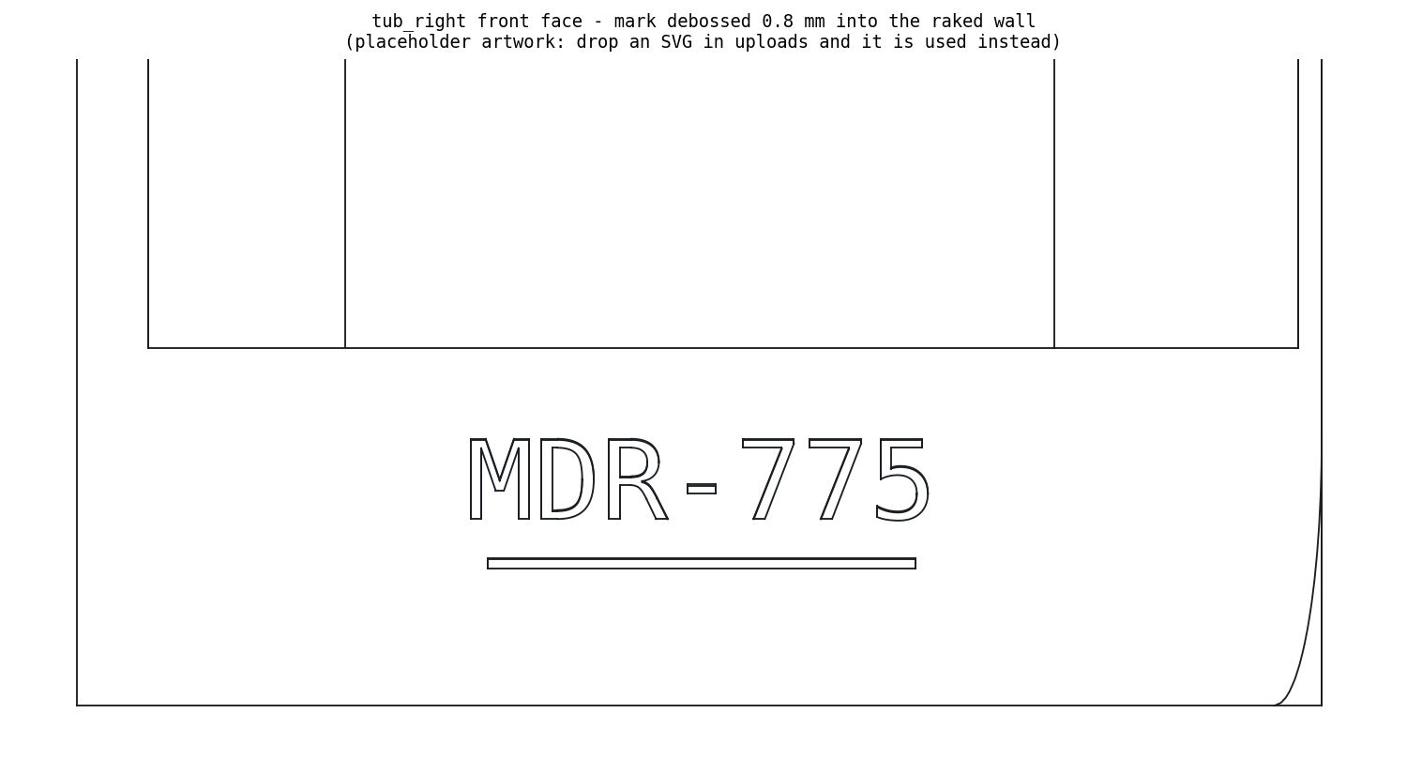
files/v5_mark_detail.png
