Strizzo/LumonTasker/files/v35_views.png

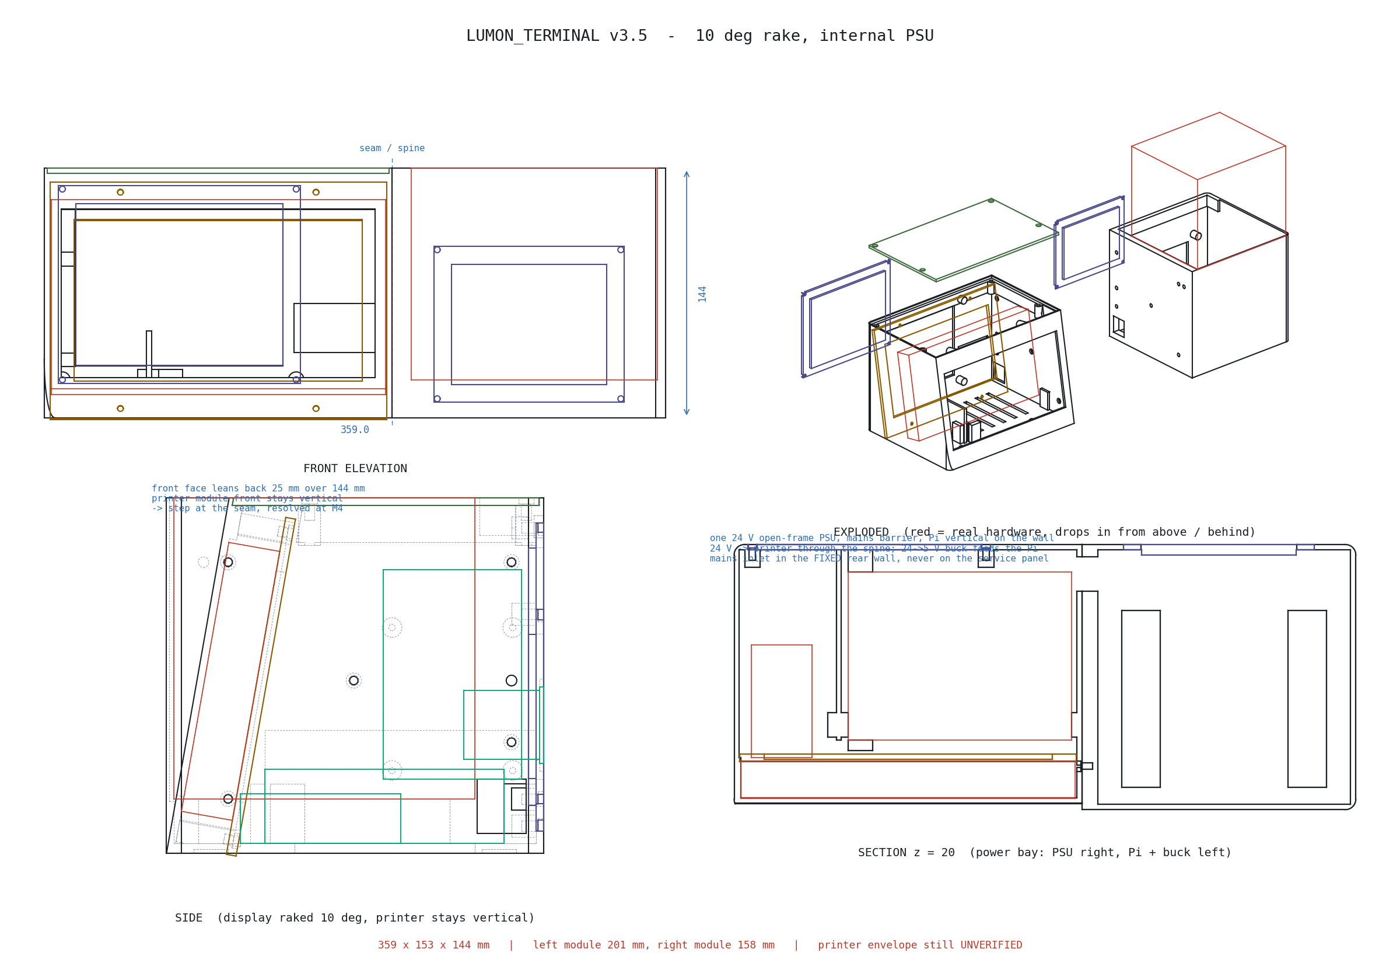
files/v35_views.png
