Strizzo/LumonTasker/files/v52_views.png

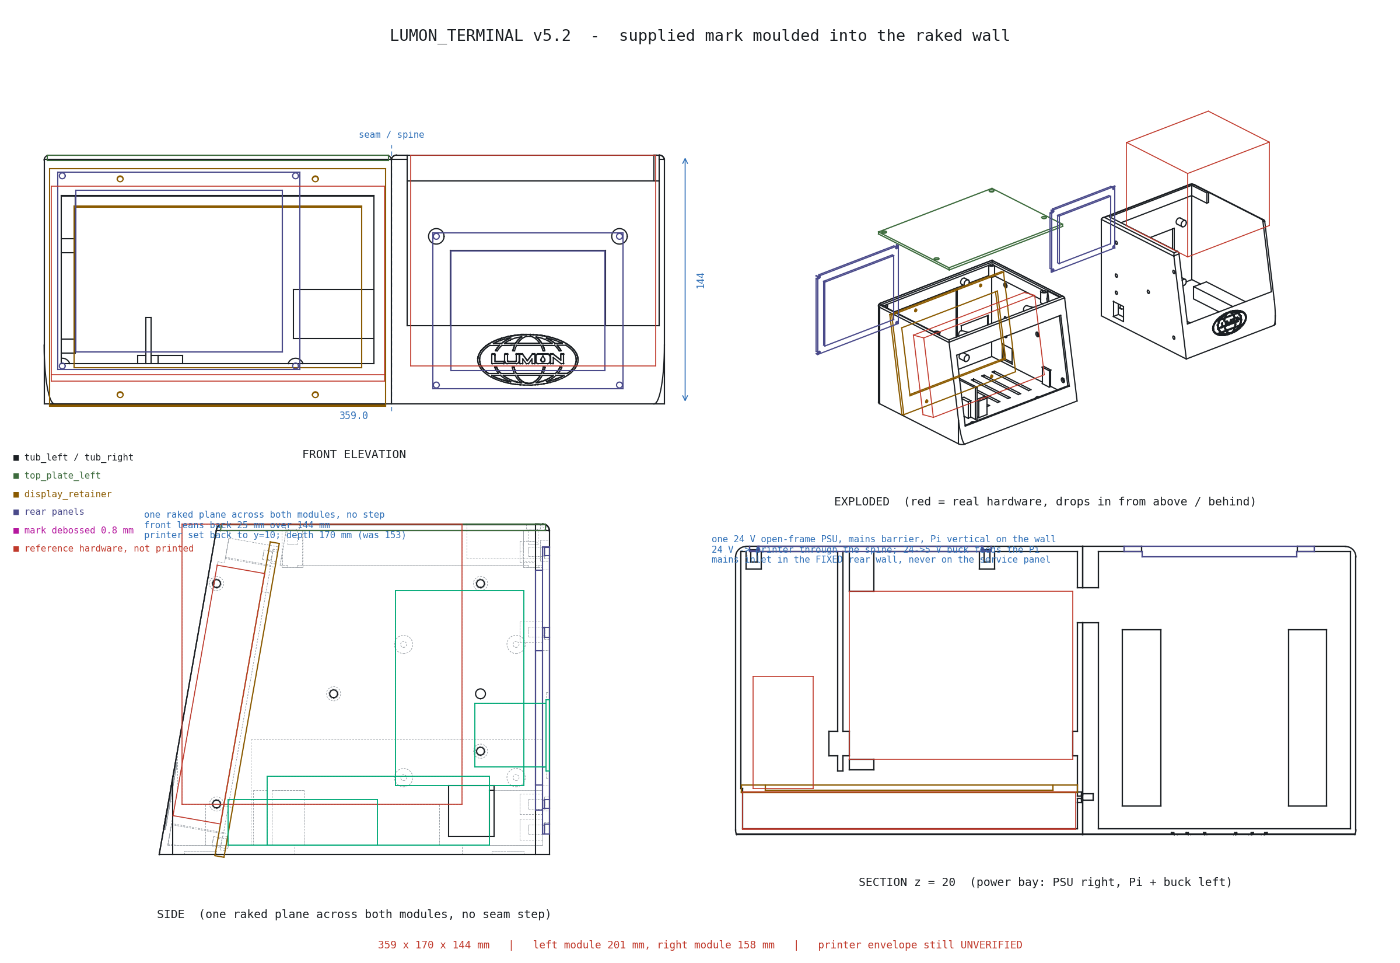
files/v52_views.png
