Strizzo/LumonTasker/software/preview/assignment.png

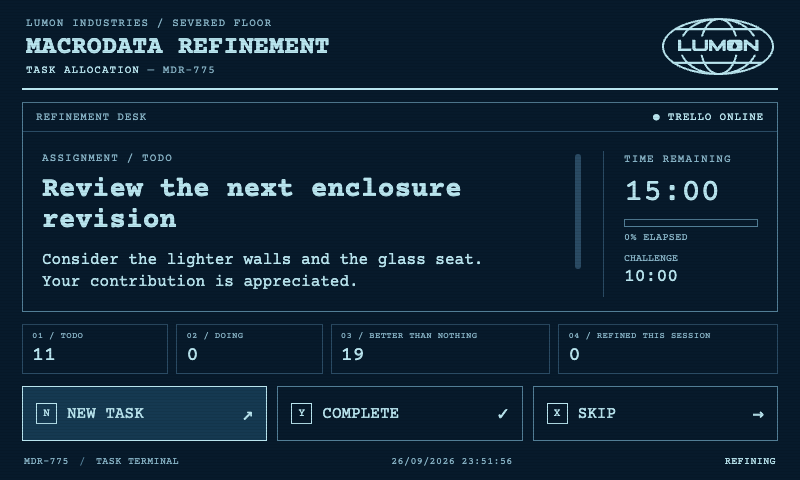
software/preview/assignment.png
