Strizzo/LumonTasker/software/preview/compact-active.png

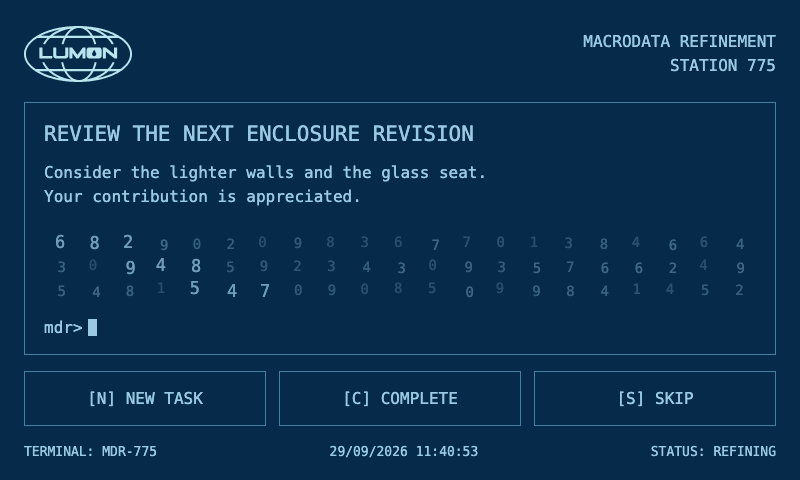
software/preview/compact-active.png
