Strizzo/LumonTasker/software/preview/compact-offline.png

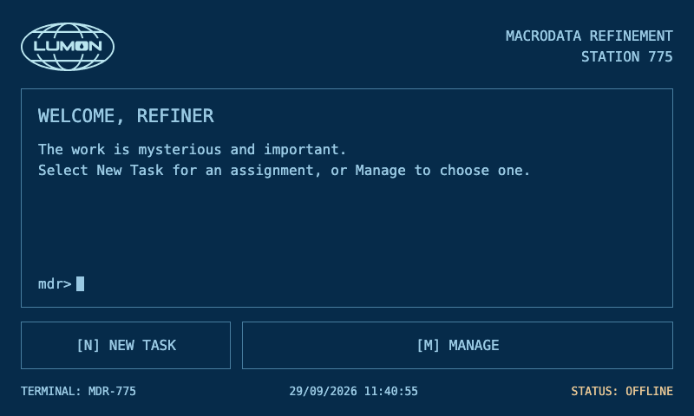
software/preview/compact-offline.png
