Strizzo/LumonTasker/software/preview/compact-optional-assignment.png

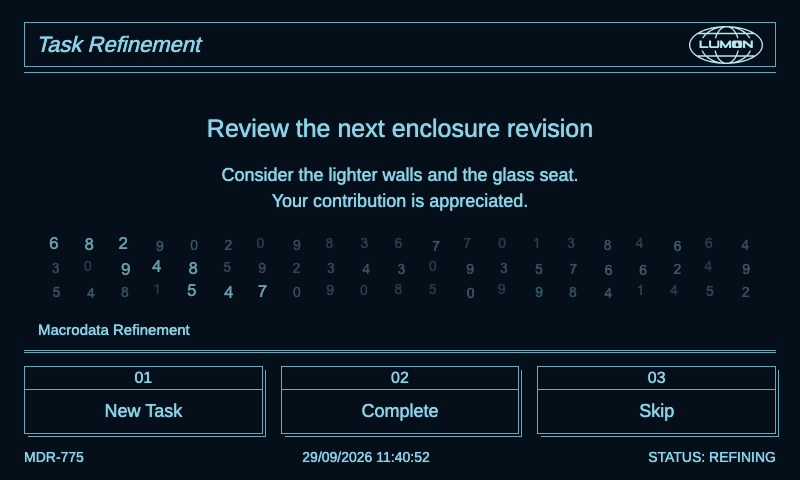
software/preview/compact-optional-assignment.png
