Strizzo/LumonTasker/software/preview/manage-classic-active.png

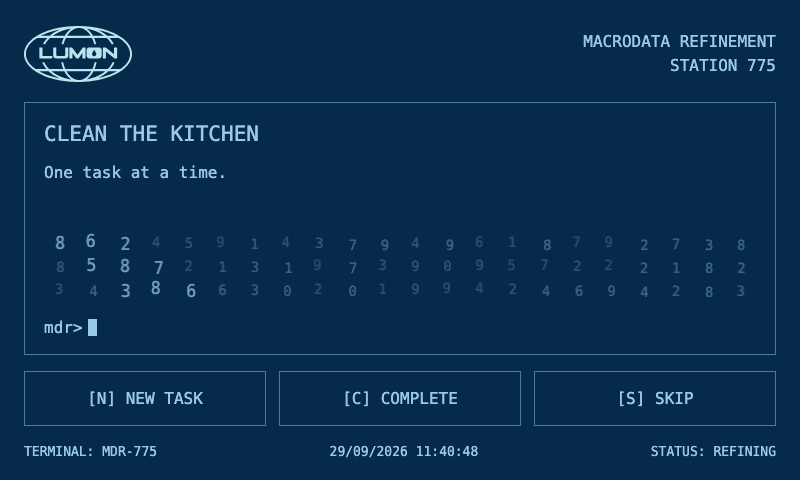
software/preview/manage-classic-active.png
