Strizzo/LumonTasker/software/preview/manage-classic-btn-grid.png

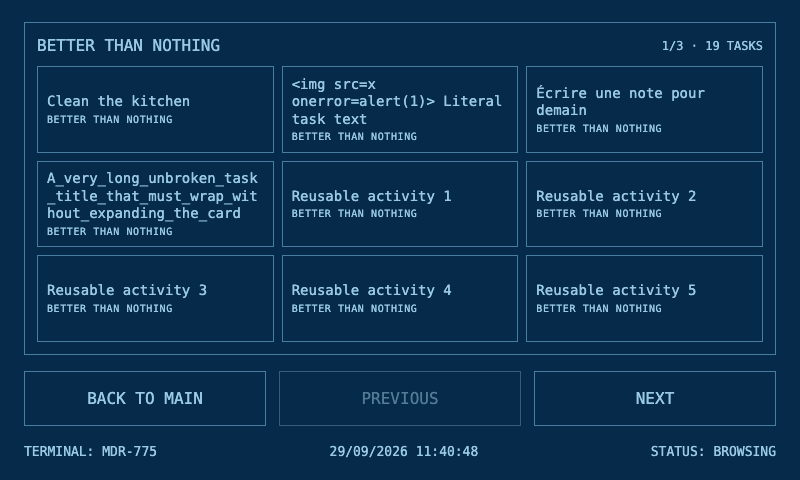
software/preview/manage-classic-btn-grid.png
