Strizzo/LumonTasker/software/preview/manage-classic-grid.png

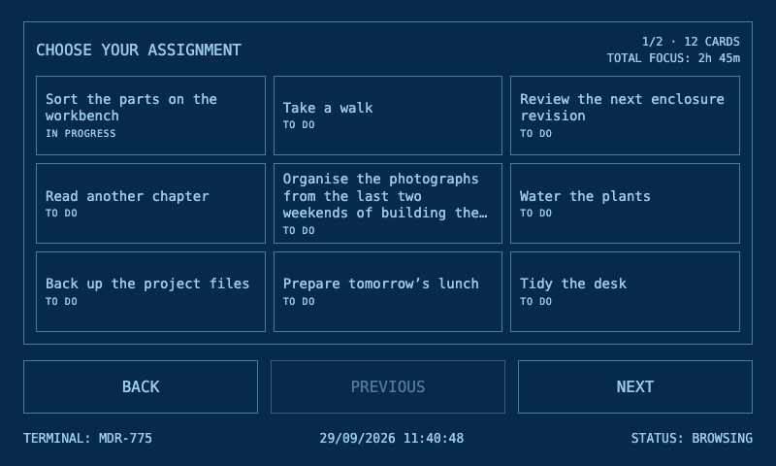
software/preview/manage-classic-grid.png
