Strizzo/LumonTasker/software/preview/manage-classic-grouped-main.png

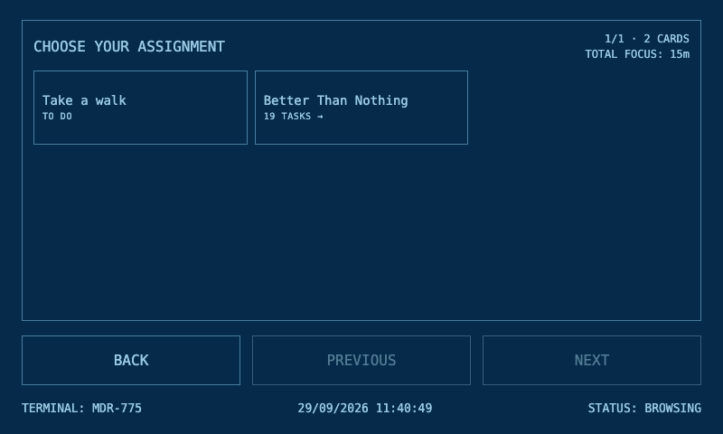
software/preview/manage-classic-grouped-main.png
