Strizzo/LumonTasker/software/preview/manage-classic-offline.png

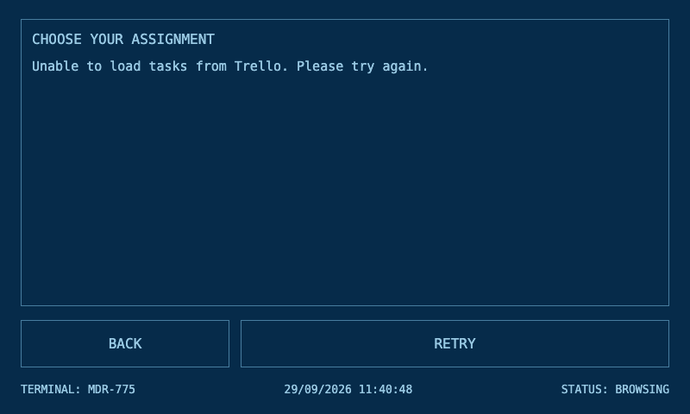
software/preview/manage-classic-offline.png
