Strizzo/LumonTasker/software/preview/manage-mdr-active.png

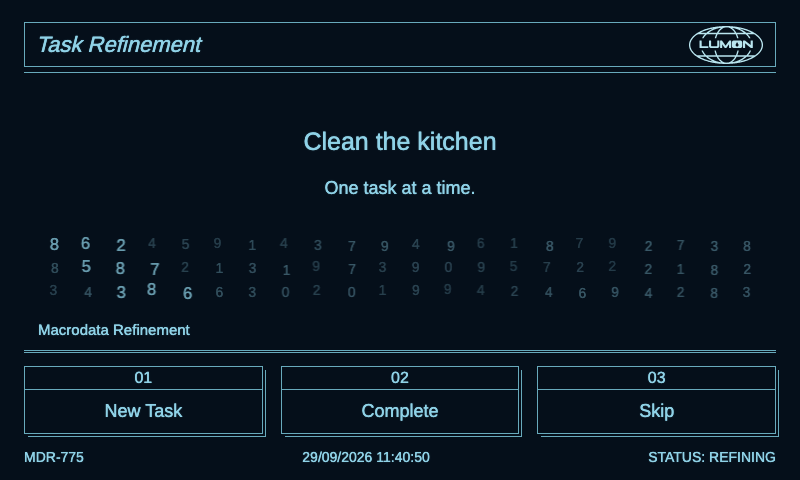
software/preview/manage-mdr-active.png
