Strizzo/LumonTasker/software/preview/manage-mdr-btn-grid.png

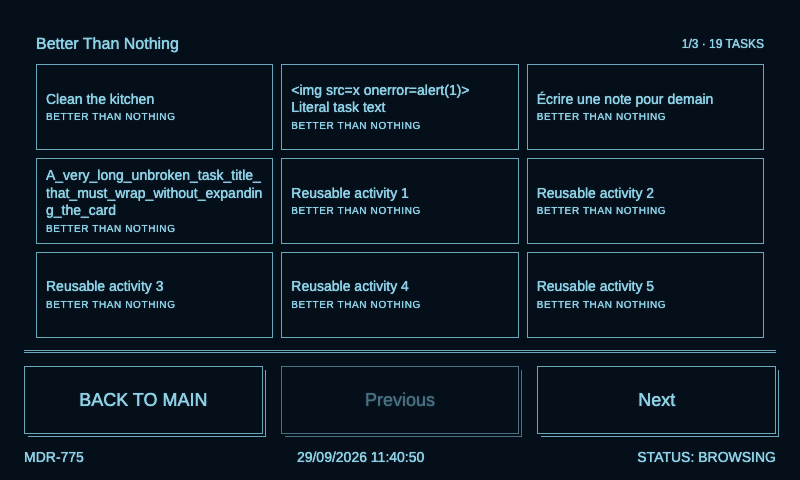
software/preview/manage-mdr-btn-grid.png
