Strizzo/LumonTasker/software/preview/manage-mdr-detail.png

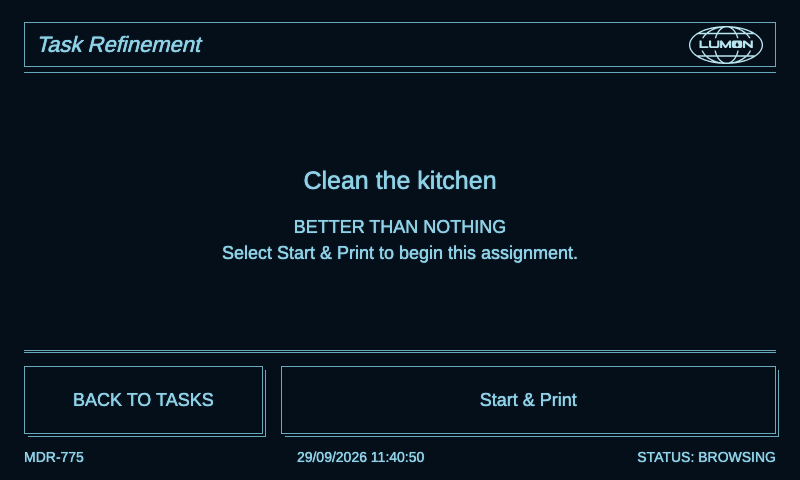
software/preview/manage-mdr-detail.png
