Strizzo/LumonTasker/software/preview/manage-mdr-grid.png

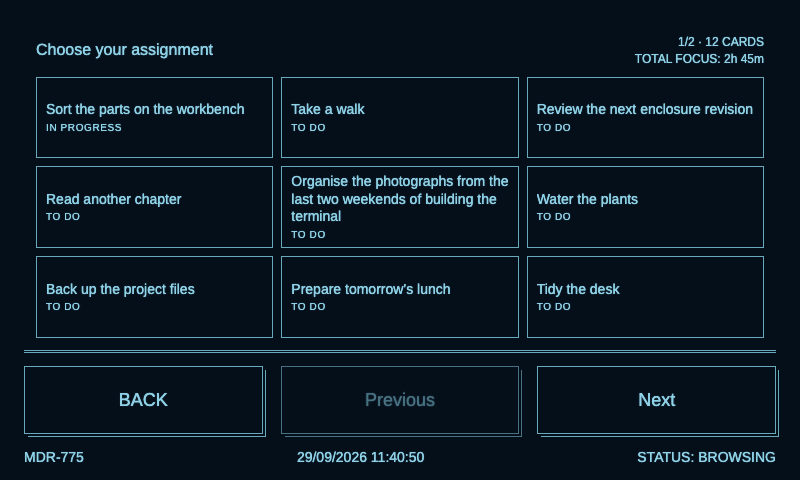
software/preview/manage-mdr-grid.png
