Strizzo/LumonTasker/software/preview/manage-mdr-home.png

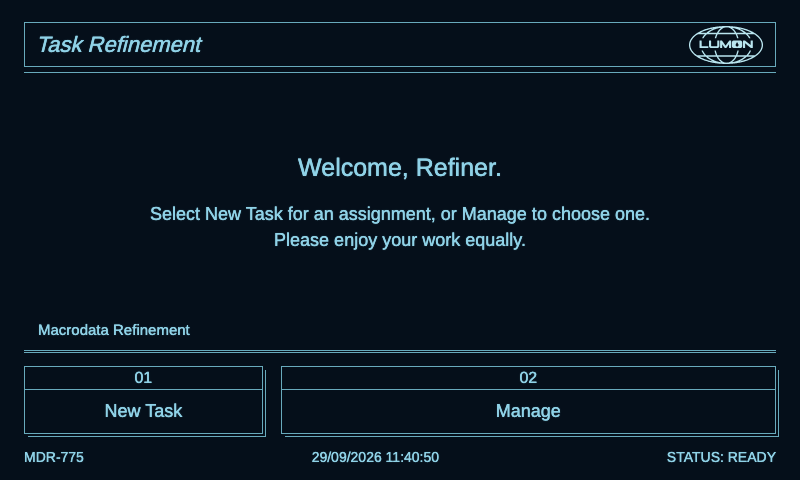
software/preview/manage-mdr-home.png
