Strizzo/LumonTasker/software/preview/manage-mdr-page2.png

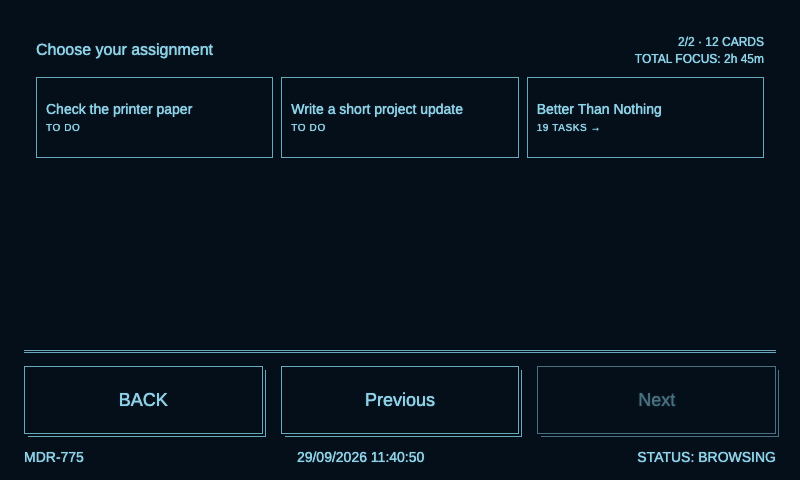
software/preview/manage-mdr-page2.png
