Strizzo/LumonTasker/software/preview/manage-regression-assignment.png

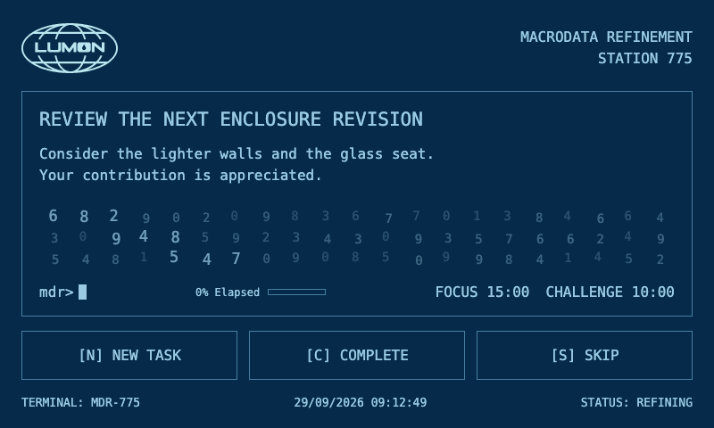
software/preview/manage-regression-assignment.png
