Strizzo/LumonTasker/software/preview/manage-regression-optional-assignment.png

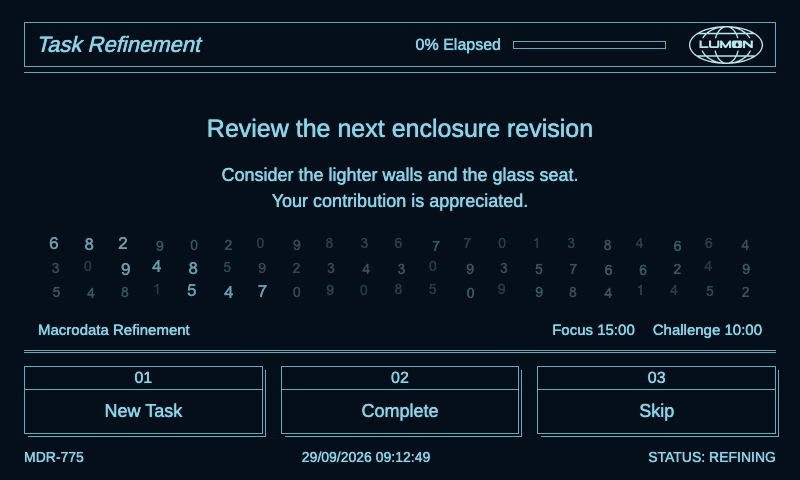
software/preview/manage-regression-optional-assignment.png
