Strizzo/LumonTasker/software/preview/mdr-assignment.png

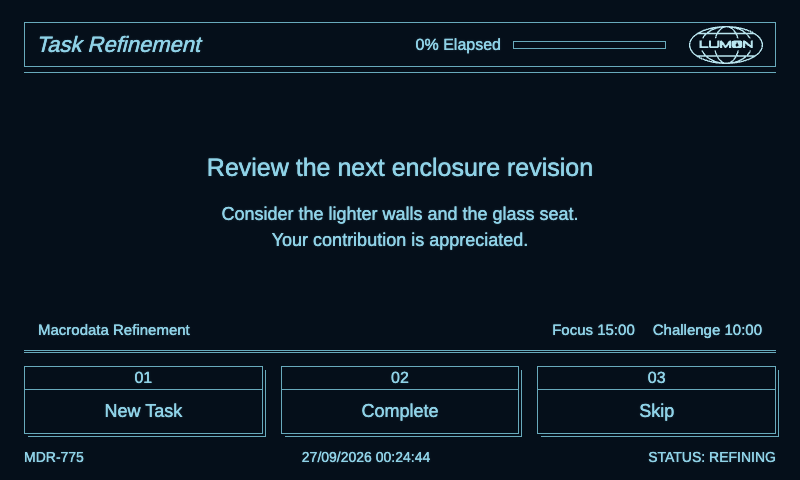
software/preview/mdr-assignment.png
