Strizzo/LumonTasker/software/preview/mdr-offline.png

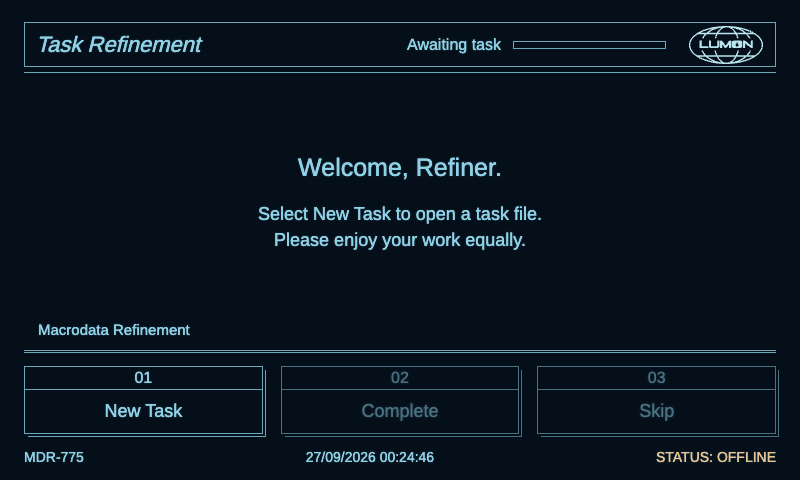
software/preview/mdr-offline.png
