Strizzo/LumonTasker/software/preview/offline.png

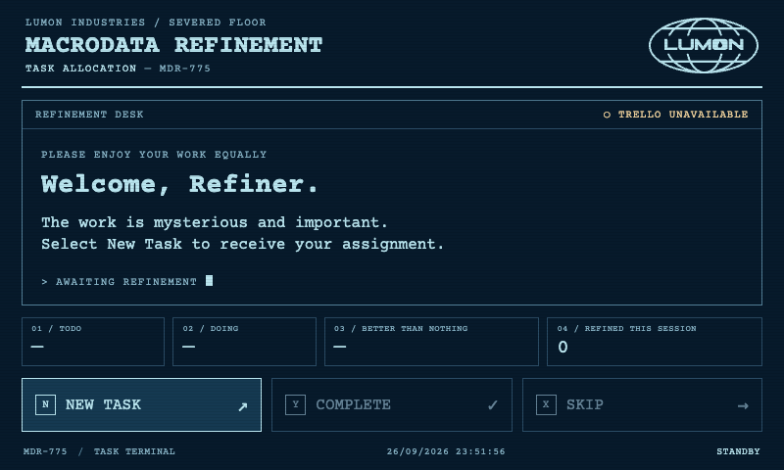
software/preview/offline.png
