Strizzo/LumonTasker/software/preview/pi-before.png

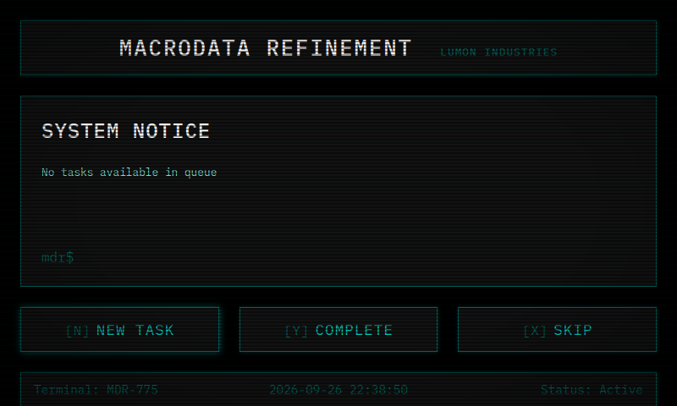
software/preview/pi-before.png
