Strizzo/LumonTasker/software/preview/pi-simple.png

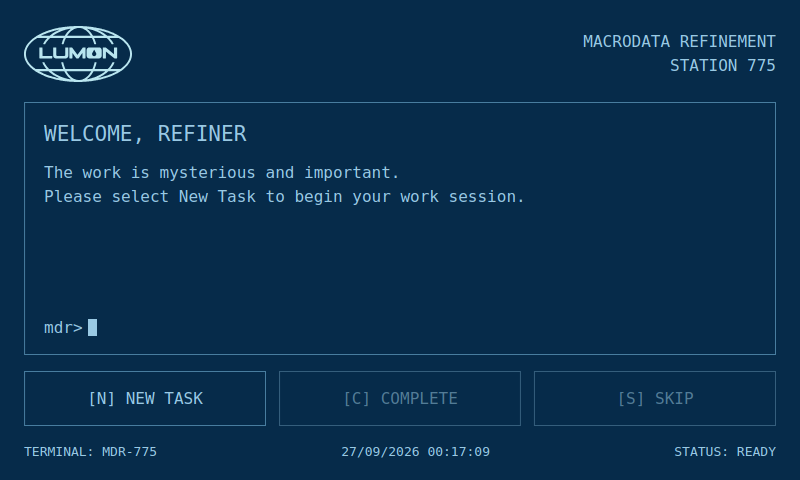
software/preview/pi-simple.png
