Strizzo/LumonTasker/software/preview/simple-assignment.png

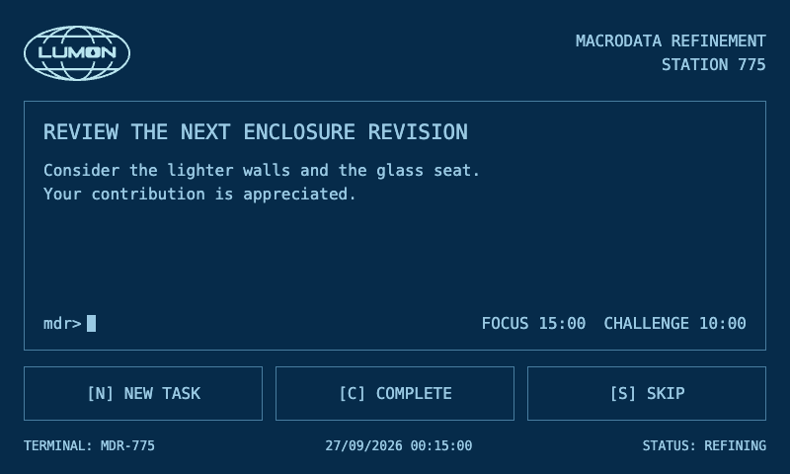
software/preview/simple-assignment.png
