Strizzo/LumonTasker/software/preview/tickets/accented-title.png

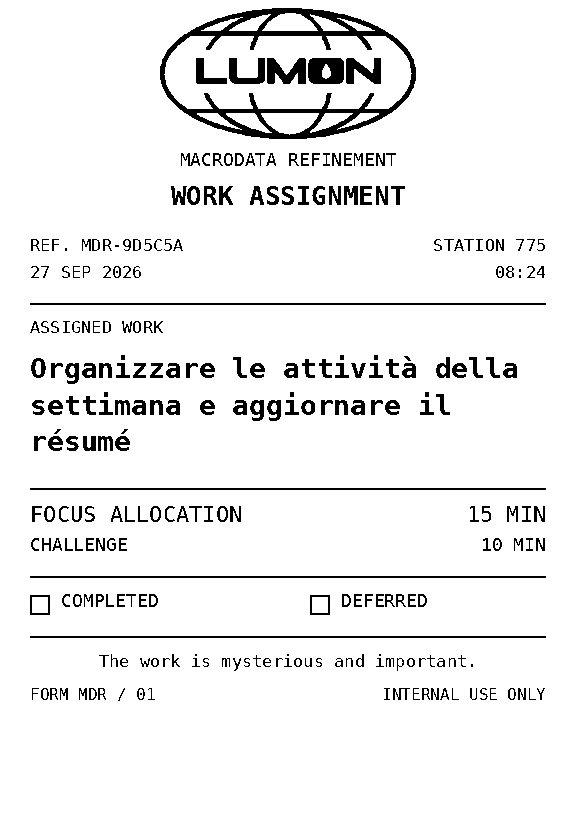
software/preview/tickets/accented-title.png
