Strizzo/LumonTasker/software/preview/tickets/long-title.png

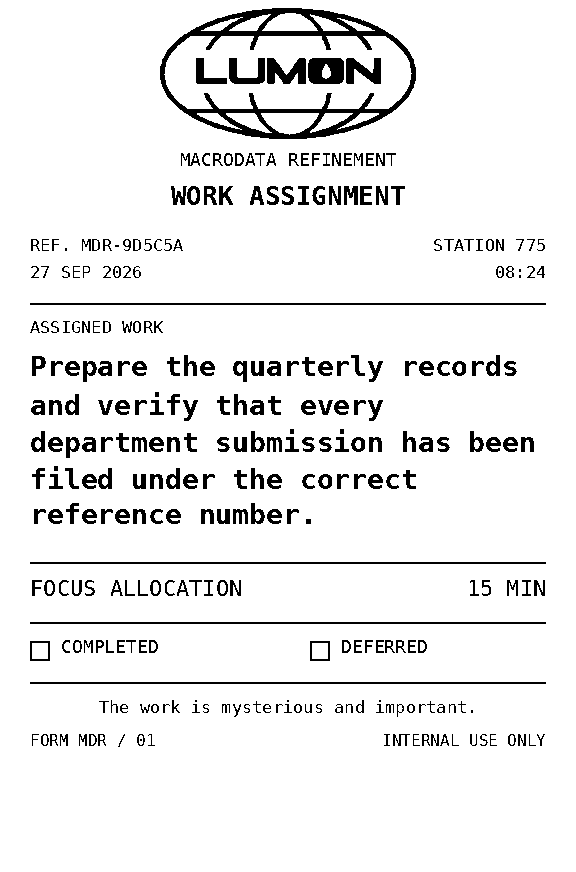
software/preview/tickets/long-title.png
