Strizzo/LumonTasker/software/preview/tickets/physical-proof.png

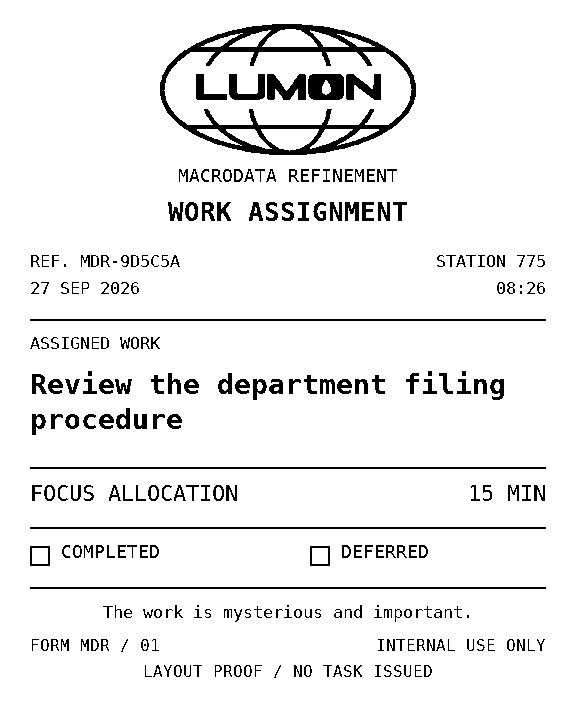
software/preview/tickets/physical-proof.png
