Strizzo/LumonTasker/cad/output/v43_integral_display_mounts/tub_left_assembly.stl

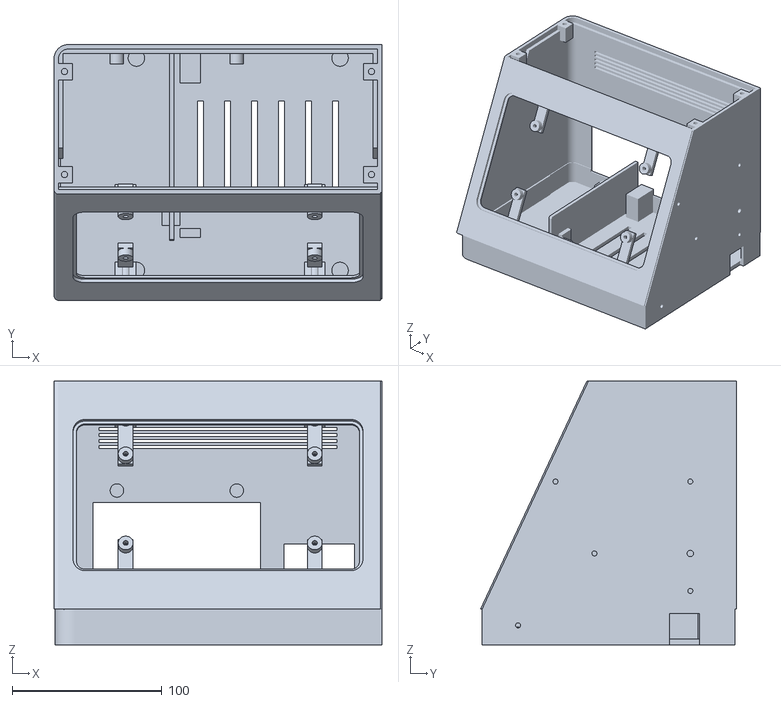
[picture p92: CAD file, 2026-09-26]
cad/output/v43_integral_display_mounts/tub_left_assembly.stl
219.0 x 170.8 x 176.0
