Strizzo/LumonTasker/cad/output/v25_tapered_printer/whole_enclosure_study.step

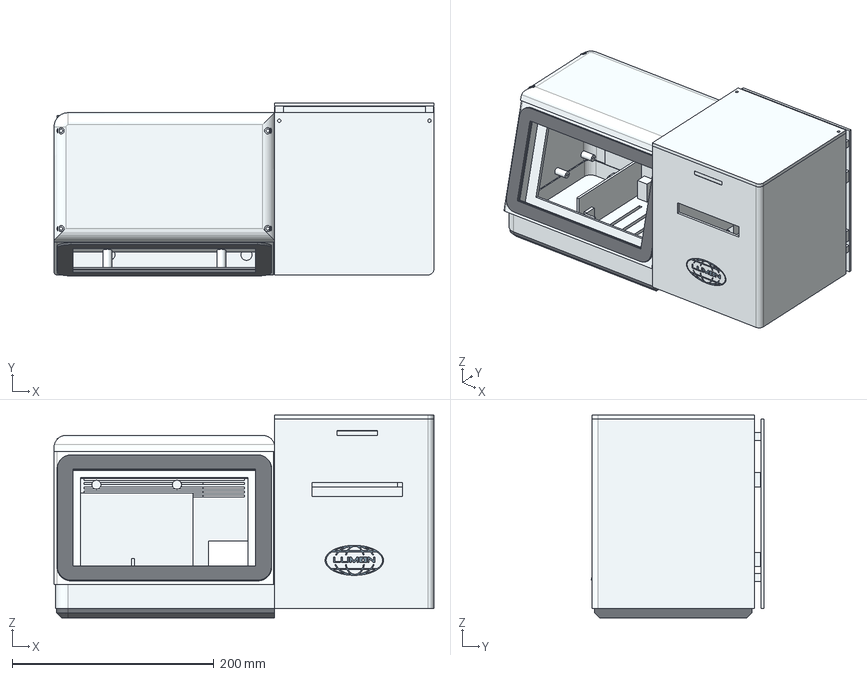
[picture p93: CAD file, 2026-09-26]
cad/output/v25_tapered_printer/whole_enclosure_study.step
377.0 x 171.5 x 201.0 mm
tub_left
top_plate_left
display_retainer
rear_panel_left
foot_left
display_bezel
cradle_tray
retaining_bar_58
retaining_bar_137
top_cover
rear_cover
logo
led_diffuser
