Strizzo/LumonTasker/cad/output/v32_equal_height/top_plate_left_assembly.stl

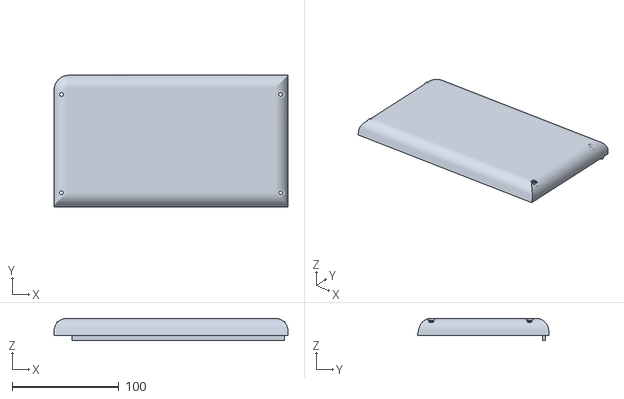
[picture p94: CAD file, 2026-09-26]
cad/output/v32_equal_height/top_plate_left_assembly.stl
219.0 x 123.1 x 21.0
