Strizzo/LumonTasker/cad/output/v33_unified_body/display_bezel_assembly.stl

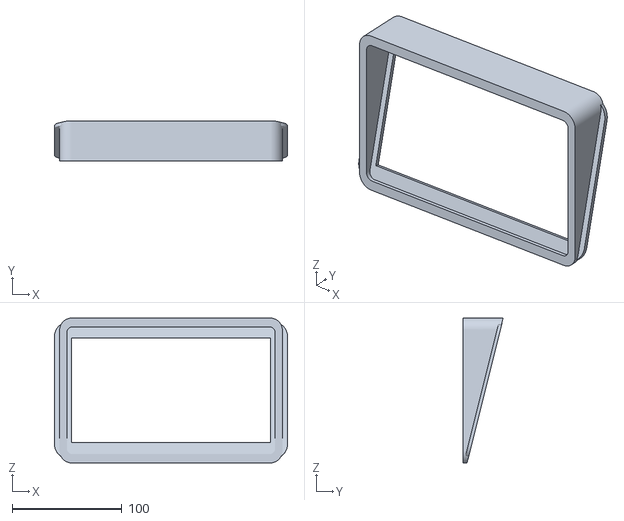
[picture p95: CAD file, 2026-09-26]
cad/output/v33_unified_body/display_bezel_assembly.stl
212.4 x 36.6 x 132.0
