Strizzo/LumonTasker/cad/output/v35_desktop_terminal/top_plate_left_assembly.stl

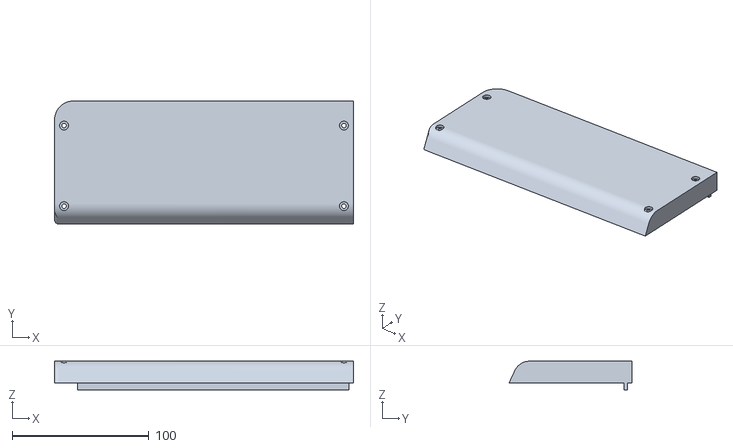
[picture p96: CAD file, 2026-09-26]
cad/output/v35_desktop_terminal/top_plate_left_assembly.stl
219.0 x 90.1 x 21.0
