Strizzo/LumonTasker/cad/output/v41_recessed_glass/display_mount_right_upper_assembly.stl

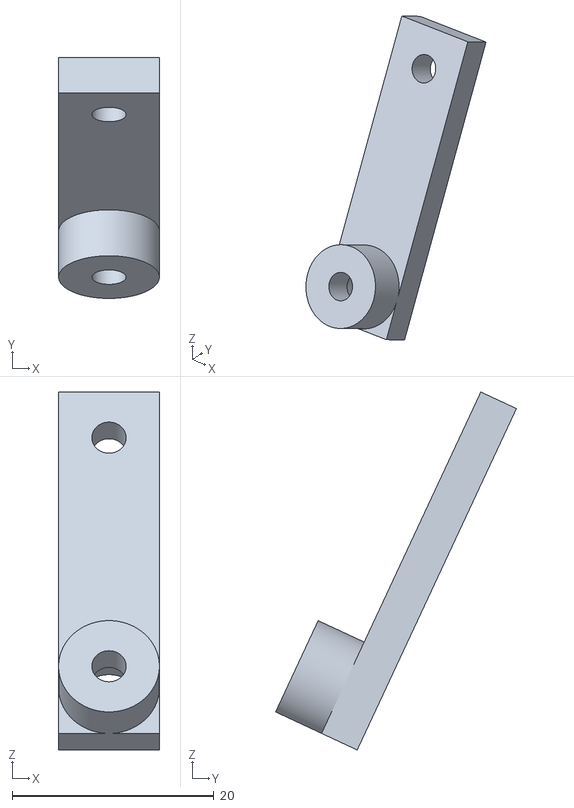
[picture p97: CAD file, 2026-09-26]
cad/output/v41_recessed_glass/display_mount_right_upper_assembly.stl
10.0 x 23.9 x 35.5
