Strizzo/LumonTasker/cad/output/v42_light_printer_base/printer_base_assembly.step

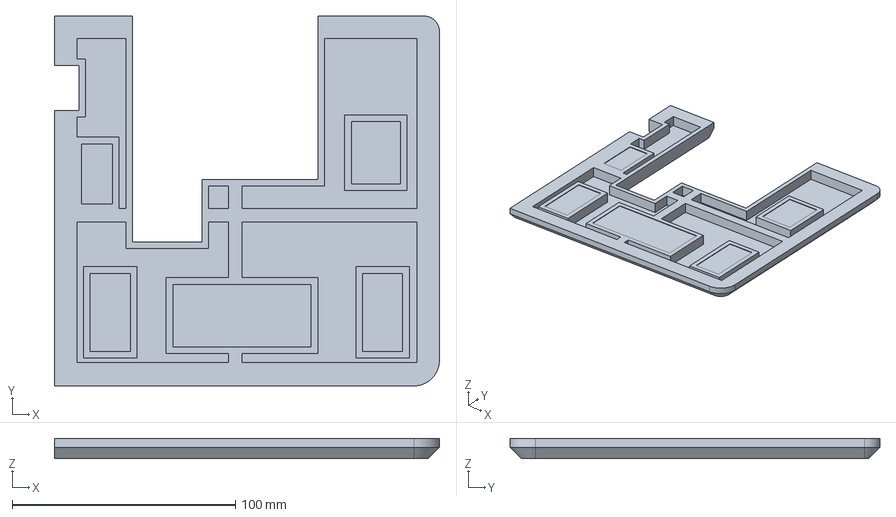
[picture p98: CAD file, 2026-09-26]
cad/output/v42_light_printer_base/printer_base_assembly.step
172.5 x 165.8 x 9.00 mm
