Strizzo/LumonTasker/cad/output/v51_external_power_body/LUMON_v51_EXTERNAL_POWER_ASSEMBLY.step

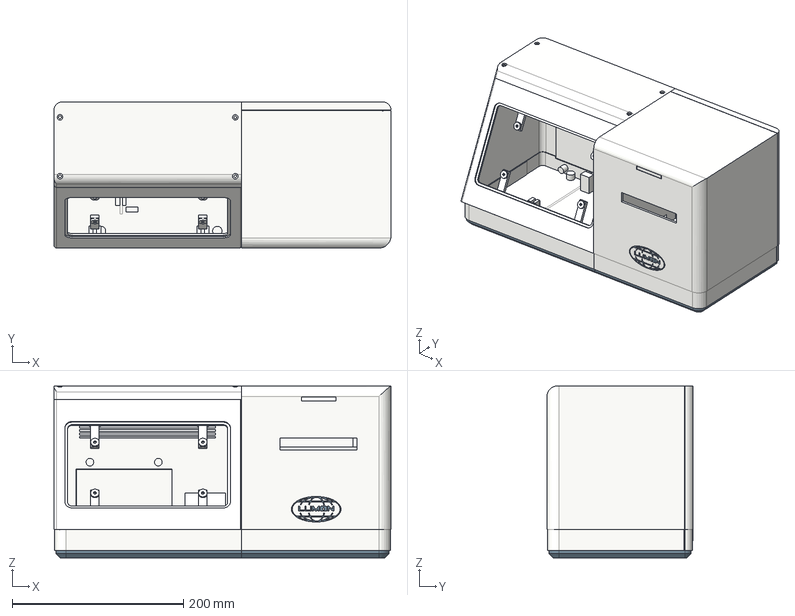
[picture p99: CAD file, 2026-09-26]
cad/output/v51_external_power_body/LUMON_v51_EXTERNAL_POWER_ASSEMBLY.step
394.0 x 170.8 x 201.0 mm
tub_left
top_plate_left
rear_panel_left
foot_left
cradle_tray
led_diffuser
foot_right_bonded
rear_cover_integrated
