Strizzo/LumonTasker/cad/output/v35_desktop_terminal/display_retainer_assembly.stl

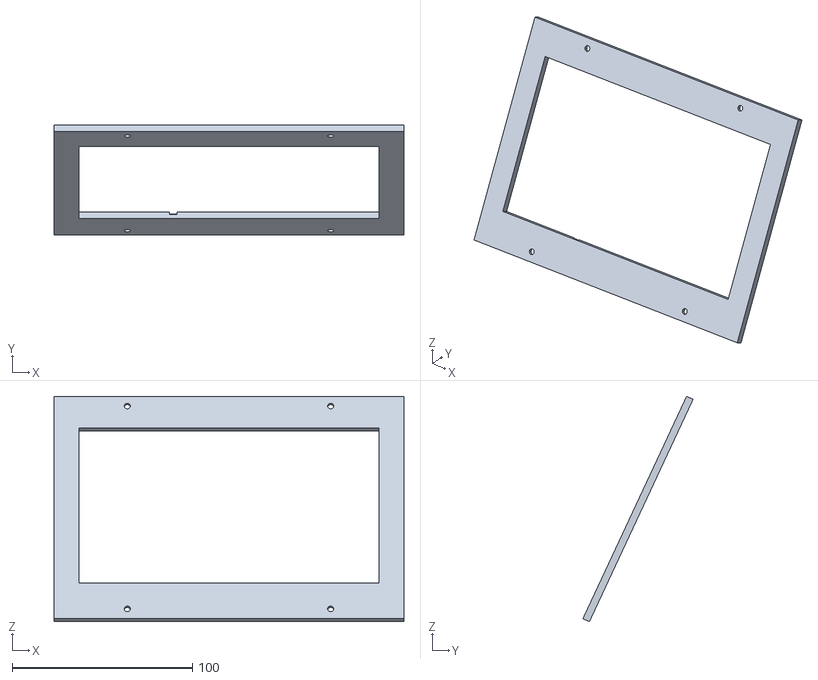
[picture p100: CAD file, 2026-09-26]
cad/output/v35_desktop_terminal/display_retainer_assembly.stl
194.4 x 61.2 x 125.2
