Strizzo/LumonTasker/cad/output/v39_aligned_rear/tub_left_assembly.stl

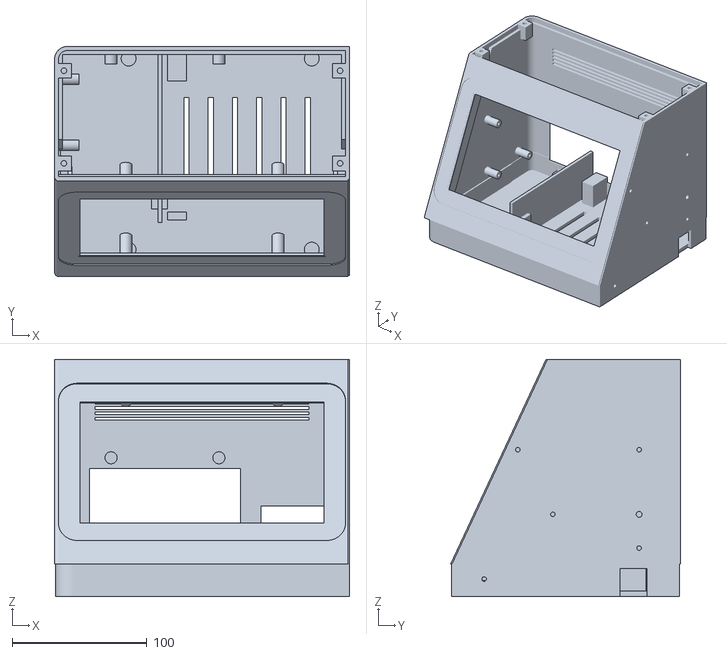
[picture p101: CAD file, 2026-09-26]
cad/output/v39_aligned_rear/tub_left_assembly.stl
219.0 x 170.8 x 176.0
