Strizzo/LumonTasker/cad/output/v41_recessed_glass/display_mount_left_lower_assembly.stl

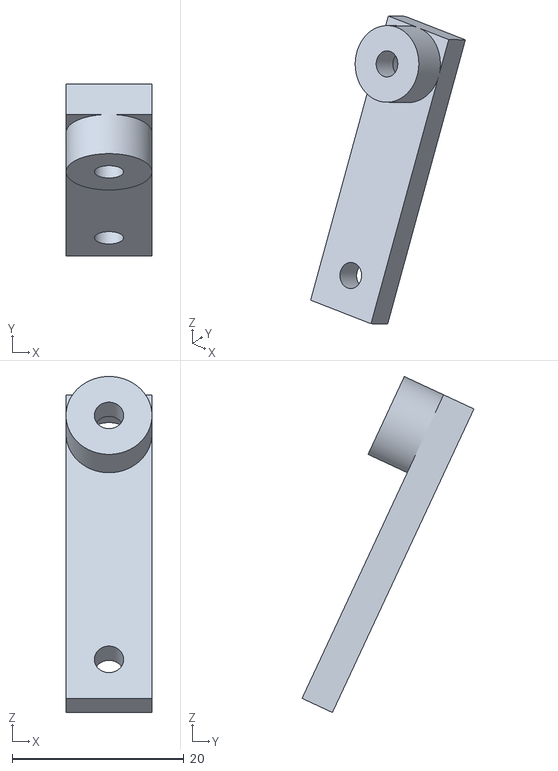
[picture p102: CAD file, 2026-09-26]
cad/output/v41_recessed_glass/display_mount_left_lower_assembly.stl
10.0 x 20.0 x 39.1
