Strizzo/LumonTasker/cad/output/v42_light_printer_base/whole_enclosure_pocketed_candidate.step

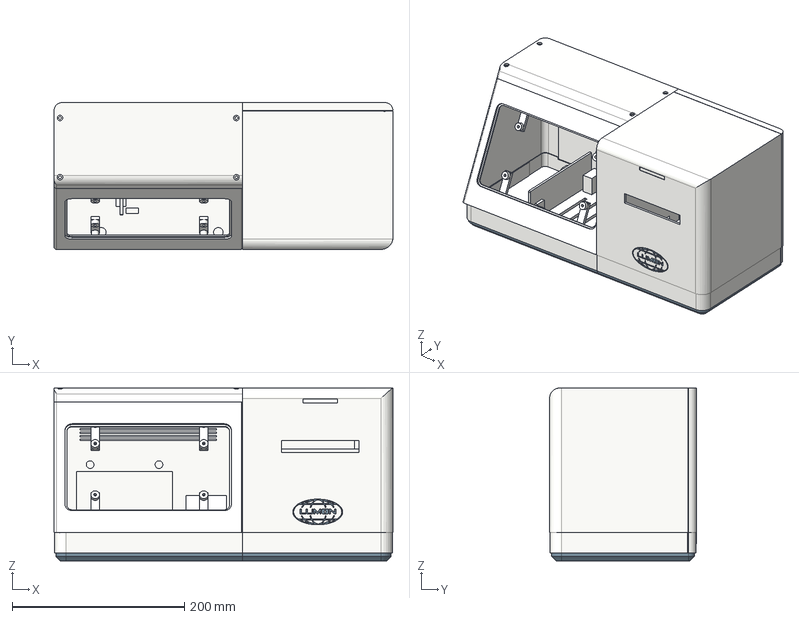
[picture p103: CAD file, 2026-09-26]
cad/output/v42_light_printer_base/whole_enclosure_pocketed_candidate.step
394.0 x 170.8 x 201.0 mm
tub_left
top_plate_left
rear_panel_left
foot_left
cradle_tray
led_diffuser
foot_right_bonded
rear_cover_integrated
display_mount_left_lower
display_mount_left_upper
display_mount_right_lower
display_mount_right_upper
