Strizzo/LumonTasker/cad/output/v33_unified_body/whole_enclosure_review.step

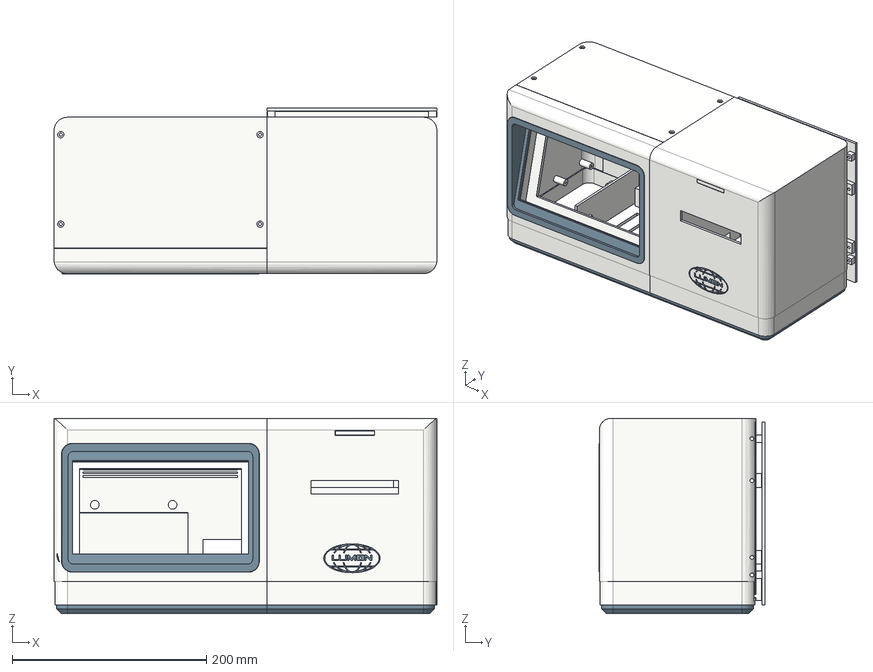
[picture p104: CAD file, 2026-09-26]
cad/output/v33_unified_body/whole_enclosure_review.step
394.0 x 170.9 x 201.0 mm
tub_left
top_plate_left
display_retainer
rear_panel_left
foot_left
display_bezel
cradle_tray
retaining_bar_58
retaining_bar_137
rear_cover
logo
led_diffuser
foot_right_bonded
