Strizzo/LumonTasker/cad/output/v40_display_mount/display_bezel_assembly.stl

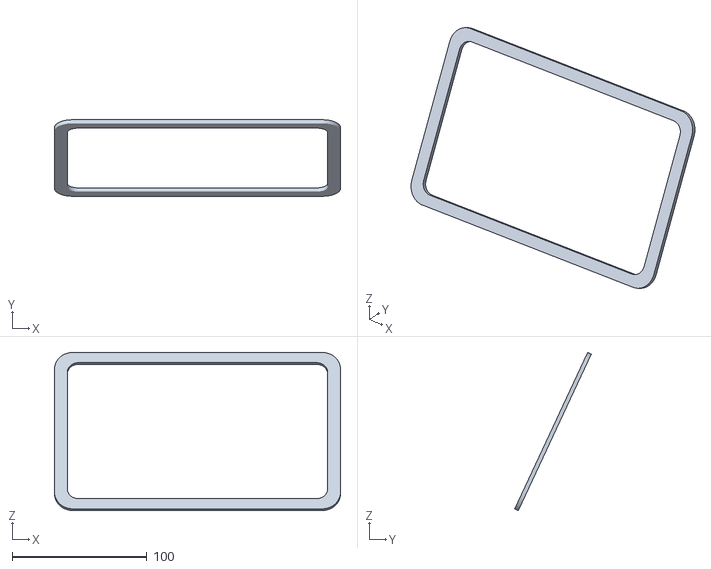
[picture p105: CAD file, 2026-09-26]
cad/output/v40_display_mount/display_bezel_assembly.stl
212.4 x 56.9 x 117.4
