Strizzo/LumonTasker/cad/output/v32_equal_height/display_bezel_assembly.stl

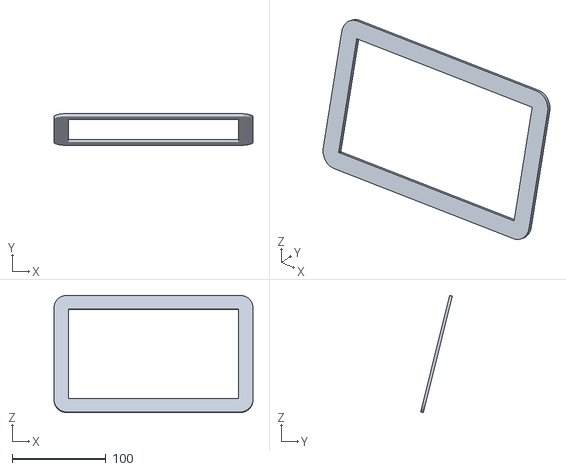
[picture p106: CAD file, 2026-09-26]
cad/output/v32_equal_height/display_bezel_assembly.stl
212.4 x 33.9 x 125.1
