Strizzo/LumonTasker/cad/output/v51_dc_inlet_panel/LUMON_v51_GLUE_DC_INLET_ASSEMBLY.step

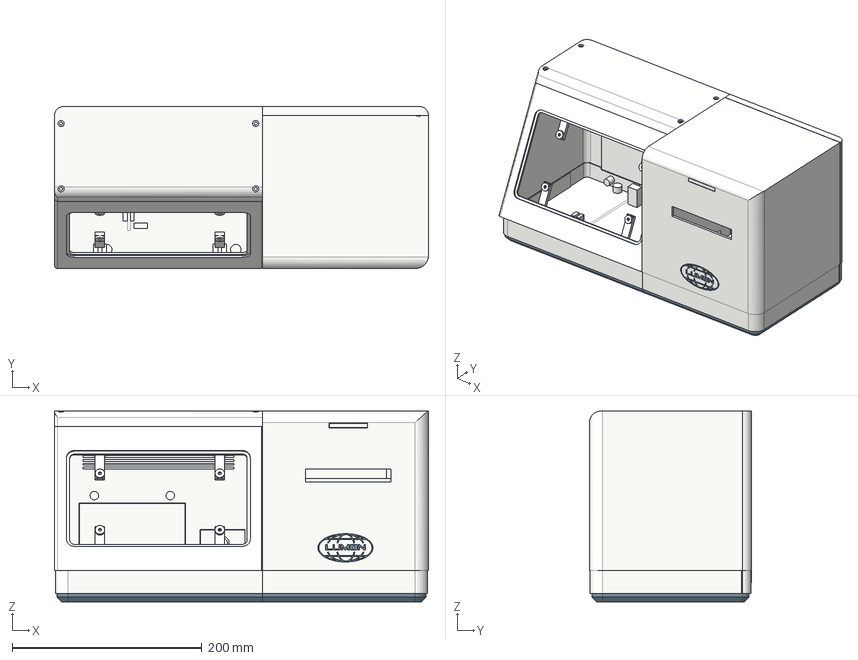
[picture p108: CAD file, 2026-09-26]
cad/output/v51_dc_inlet_panel/LUMON_v51_GLUE_DC_INLET_ASSEMBLY.step
394.0 x 170.8 x 201.0 mm
tub_left
top_plate_left
rear_panel_left
foot_left
cradle_tray
led_diffuser
foot_right_bonded
rear_cover_integrated
DC_INLET_GLUE_PANEL_10mm_SOCKET_5mm_INWARD_SLEEVE
