Strizzo/LumonTasker/cad/output/v38_integrated_rear/foot_right_bonded_assembly.stl

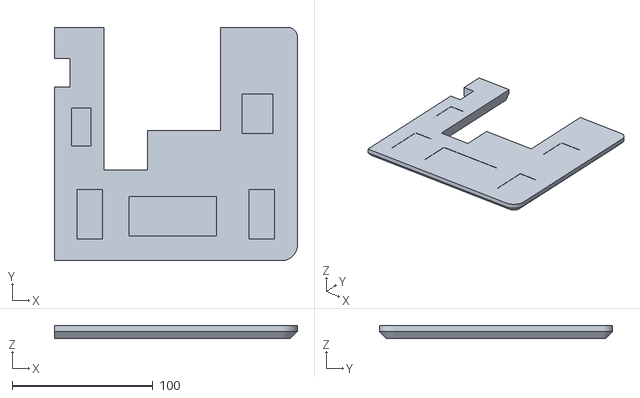
[picture p110: CAD file, 2026-09-26]
cad/output/v38_integrated_rear/foot_right_bonded_assembly.stl
172.5 x 165.8 x 9.00
