Strizzo/LumonTasker/cad/output/v40_display_mount/display_fit_frame_assembly.stl

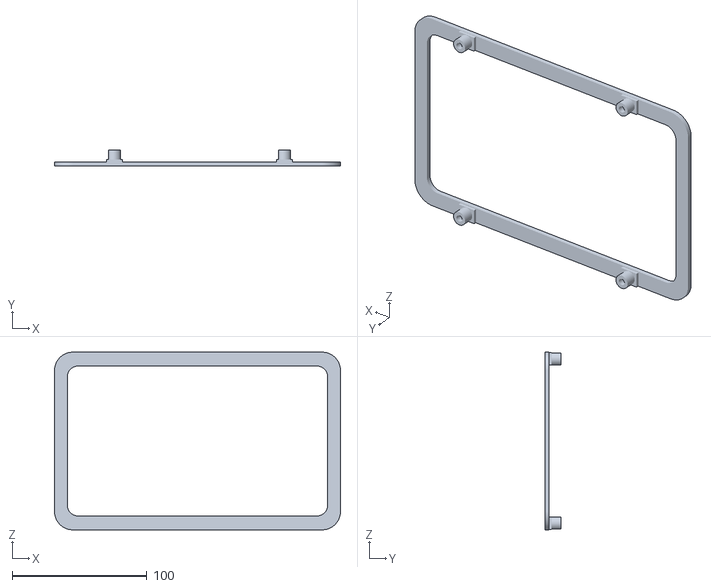
[picture p112: CAD file, 2026-09-26]
cad/output/v40_display_mount/display_fit_frame_assembly.stl
212.4 x 12.0 x 132.0
