Strizzo/LumonTasker/cad/output/v38_integrated_rear/shell_assembly.stl

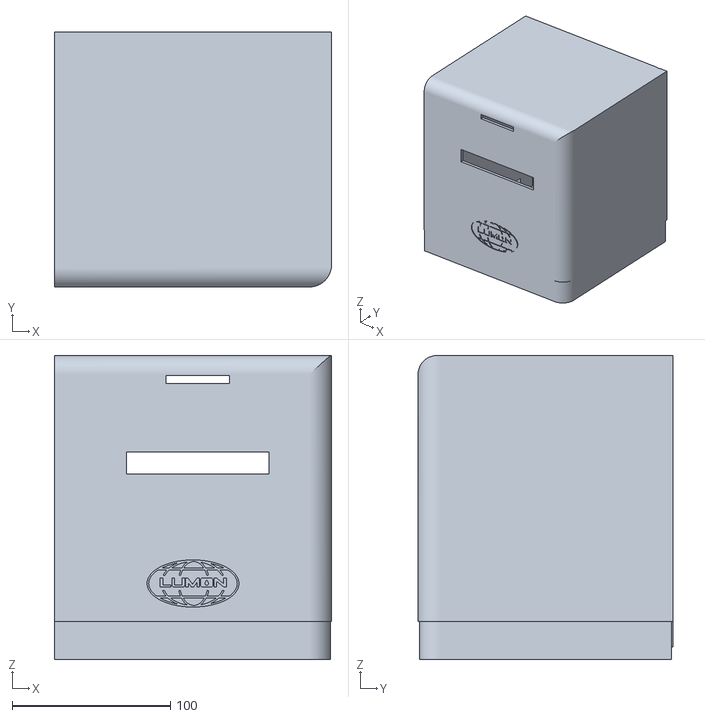
[picture p113: CAD file, 2026-09-26]
cad/output/v38_integrated_rear/shell_assembly.stl
175.0 x 161.0 x 192.0
