Strizzo/LumonTasker/cad/output/v39_aligned_rear/foot_left_assembly.stl

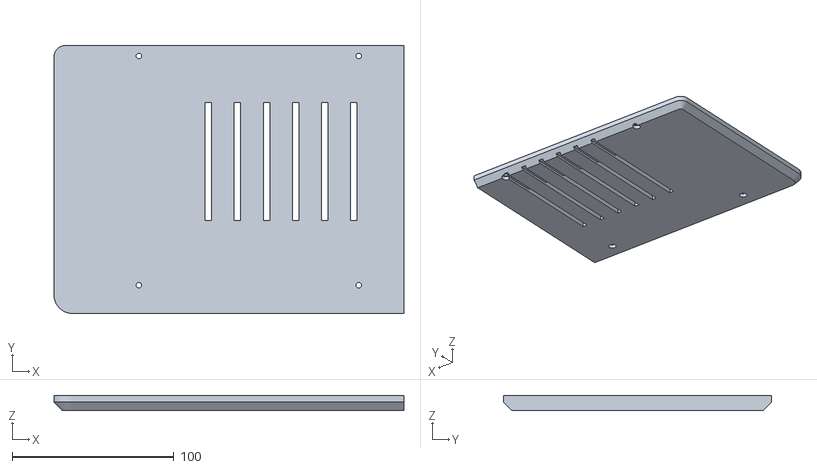
[picture p114: CAD file, 2026-09-26]
cad/output/v39_aligned_rear/foot_left_assembly.stl
216.5 x 165.8 x 9.00
