Strizzo/LumonTasker/cad/output/v39_aligned_rear/top_plate_left_assembly.stl

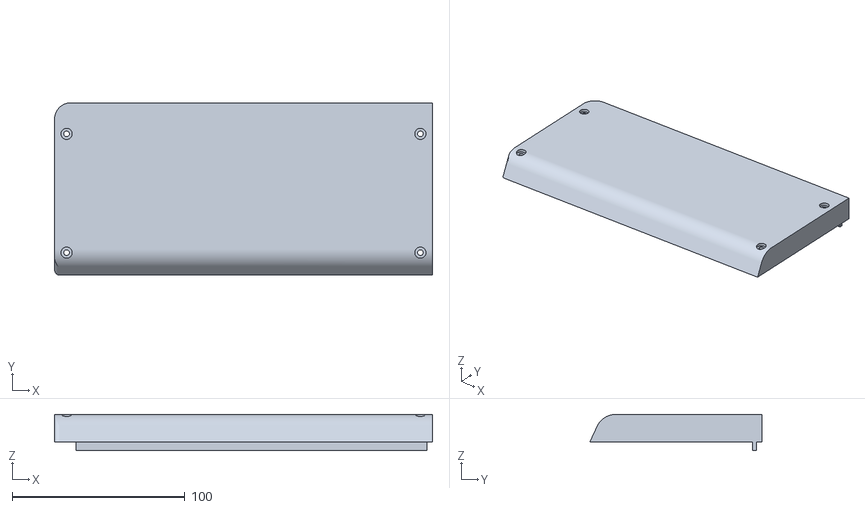
[picture p116: CAD file, 2026-09-26]
cad/output/v39_aligned_rear/top_plate_left_assembly.stl
219.0 x 99.9 x 21.0
