Strizzo/LumonTasker/cad/output/v40_display_mount/display_mount_left_lower_local_assembly.stl

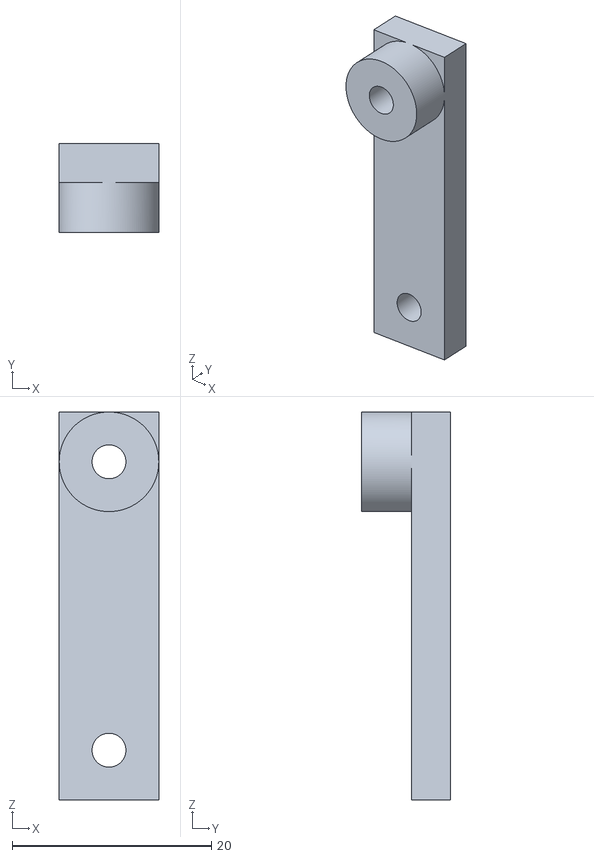
[picture p117: CAD file, 2026-09-26]
cad/output/v40_display_mount/display_mount_left_lower_local_assembly.stl
10.0 x 8.94 x 39.0
