Strizzo/LumonTasker/cad/output/v38_integrated_rear/whole_enclosure_review.step

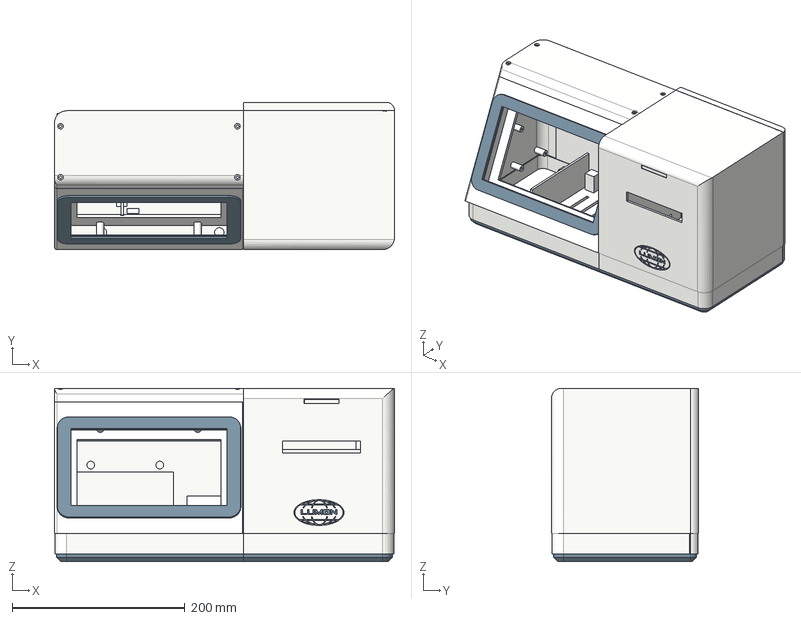
[picture p118: CAD file, 2026-09-26]
cad/output/v38_integrated_rear/whole_enclosure_review.step
394.0 x 170.8 x 201.0 mm
tub_left
top_plate_left
display_retainer
rear_panel_left
foot_left
display_bezel
cradle_tray
led_diffuser
foot_right_bonded
rear_cover_integrated
