Strizzo/LumonTasker/cad/output/v38_integrated_rear/rear_cover_integrated_assembly.stl

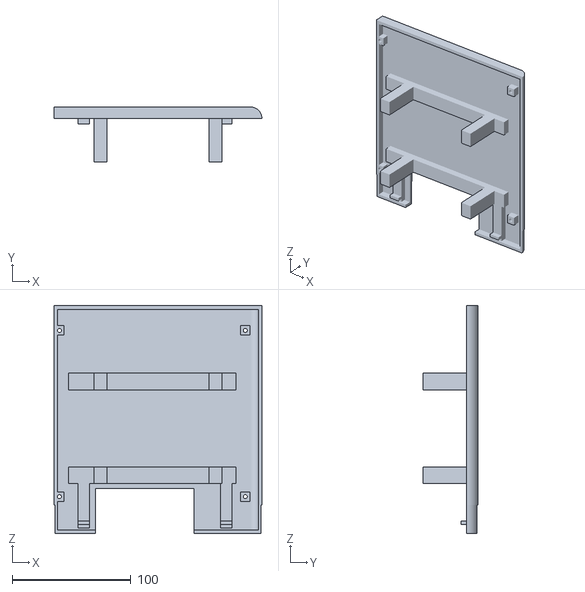
[picture p119: CAD file, 2026-09-26]
cad/output/v38_integrated_rear/rear_cover_integrated_assembly.stl
175.0 x 46.2 x 192.0
