Strizzo/LumonTasker/cad/output/v40_display_mount/display_fit_kit_assembled.step

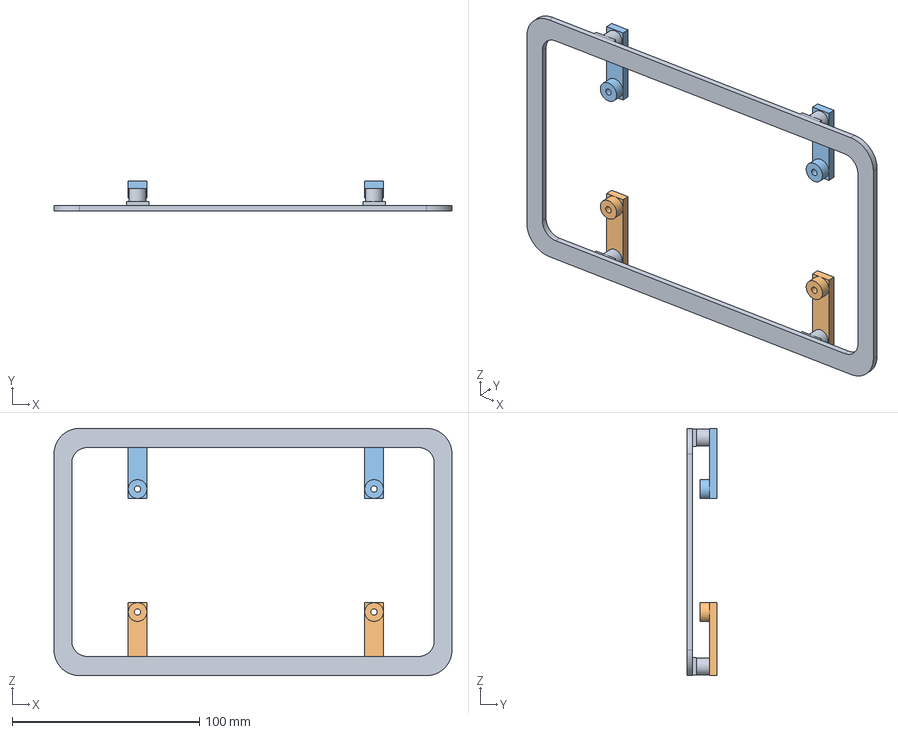
[picture p120: CAD file, 2026-09-26]
cad/output/v40_display_mount/display_fit_kit_assembled.step
212.4 x 15.9 x 132.0 mm
display_fit_frame
display_mount_left_lower_local
display_mount_left_upper_local
display_mount_right_lower_local
display_mount_right_upper_local
