Strizzo/LumonTasker/cad/output/v39_aligned_rear/rear_panel_left_assembly.stl

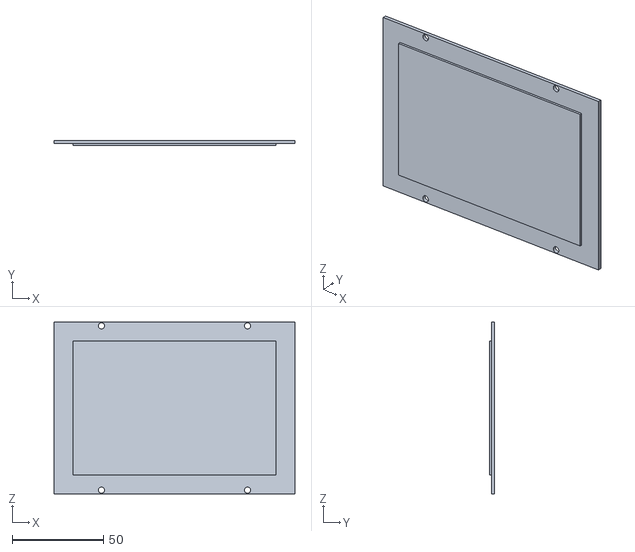
[picture p121: CAD file, 2026-09-26]
cad/output/v39_aligned_rear/rear_panel_left_assembly.stl
132.0 x 3.00 x 94.0
