Strizzo/LumonTasker/cad/output/p1s_fit_plate/LUMON_v19_fit_test_setup.3mf

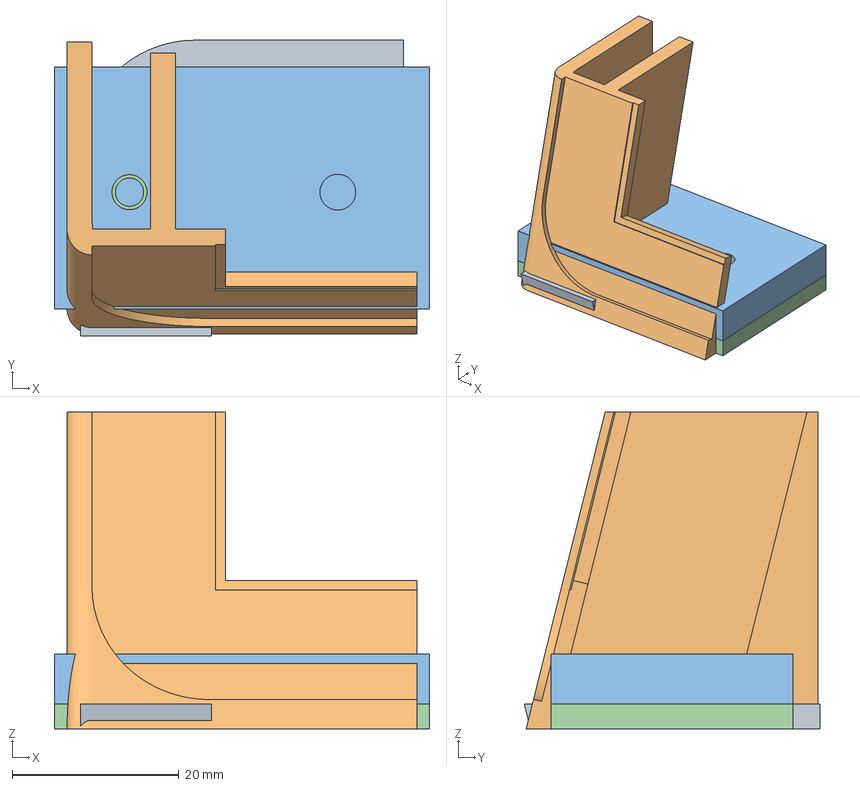
[picture p122: CAD file, 2026-09-26]
cad/output/p1s_fit_plate/LUMON_v19_fit_test_setup.3mf
45.0 x 35.5 x 38.0 mm
dark_bezel_corner.stl
Plate 1 (Plate 1 (Plate 1))
light_seam_right.stl
light_seam_left.stl
