Strizzo/LumonTasker/cad/output/v19/assembly_stl/rear_panel_left.stl

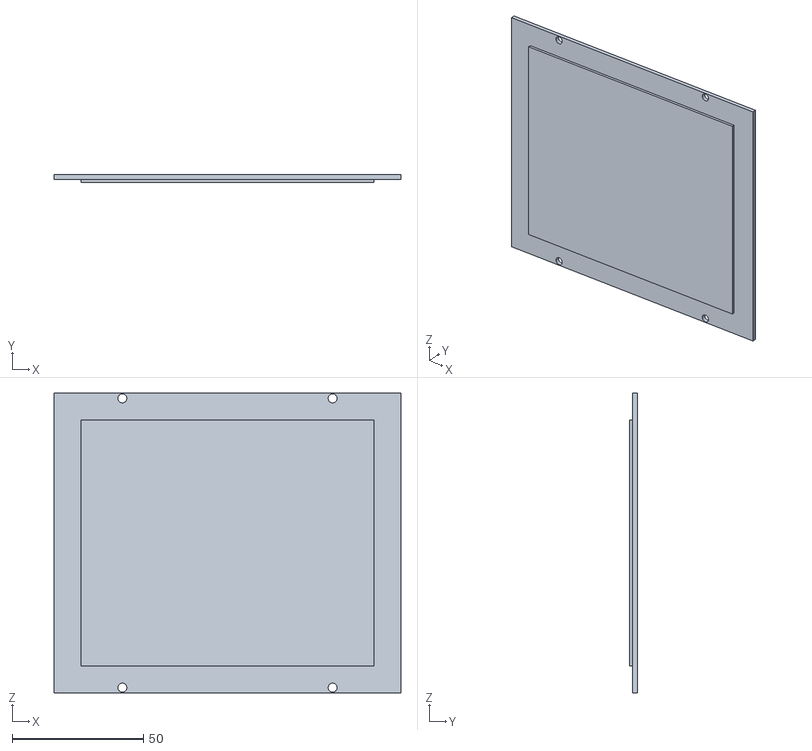
[picture p123: CAD file, 2026-09-26]
cad/output/v19/assembly_stl/rear_panel_left.stl
132.0 x 3.00 x 114.0
