Strizzo/LumonTasker/cad/output/v19/fit_coupons/seam_left.stl

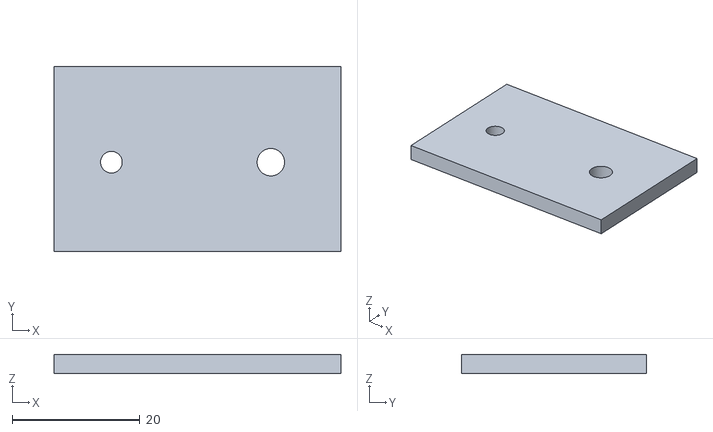
[picture p124: CAD file, 2026-09-26]
cad/output/v19/fit_coupons/seam_left.stl
45.0 x 29.0 x 3.00
