Strizzo/LumonTasker/cad/output/v19/LUMON_v19_colored_review.step

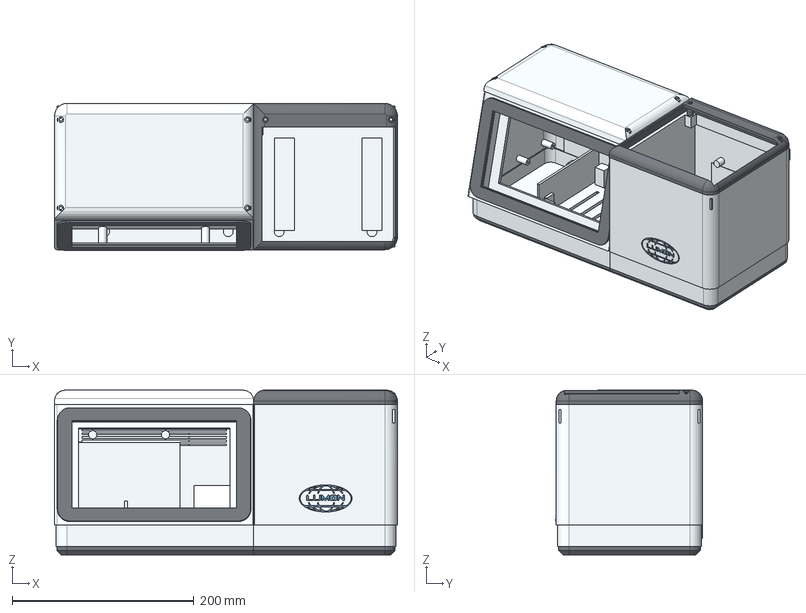
[picture p125: CAD file, 2026-09-26]
cad/output/v19/LUMON_v19_colored_review.step
377.0 x 162.0 x 181.0 mm
tub_left
tub_right
top_plate_left
printer_trim
display_retainer
rear_panel_left
rear_panel_right
foot_left
foot_right
display_bezel
logo_fill
