Strizzo/LumonTasker/cad/output/v19/oriented_stl/top_plate_left.stl

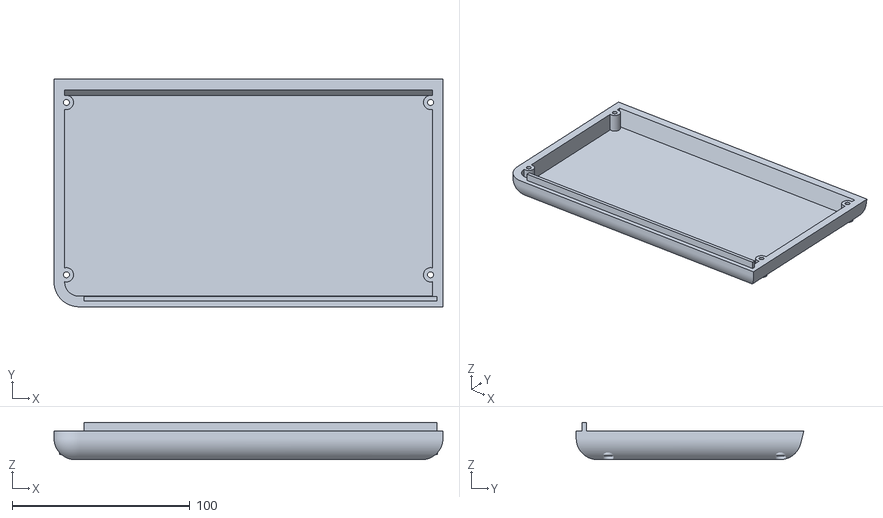
[picture p126: CAD file, 2026-09-26]
cad/output/v19/oriented_stl/top_plate_left.stl
219.0 x 128.1 x 21.0
