Strizzo/LumonTasker/cad/output/v20_front/cradle_tray.stl

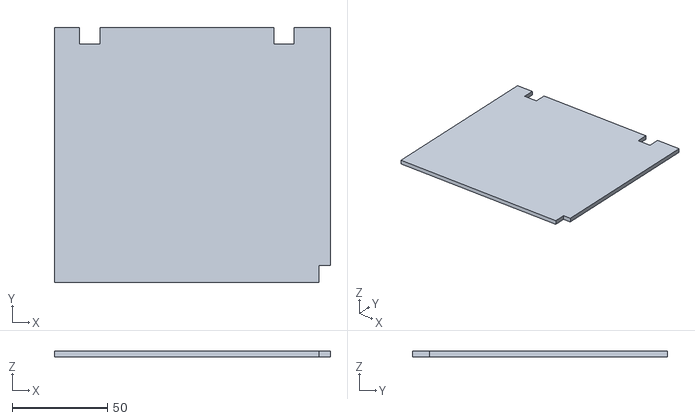
[picture p127: CAD file, 2026-09-26]
cad/output/v20_front/cradle_tray.stl
145.0 x 134.0 x 3.00
