Strizzo/LumonTasker/cad/output/v21_rear_loading/retaining_bar_58.stl

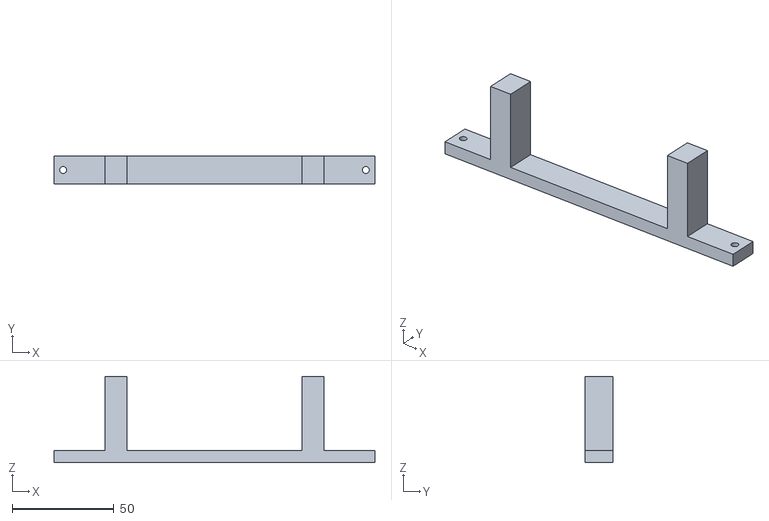
[picture p128: CAD file, 2026-09-26]
cad/output/v21_rear_loading/retaining_bar_58.stl
158.0 x 14.0 x 42.5
