Strizzo/LumonTasker/cad/output/v23_upper_output/printer_reference.step

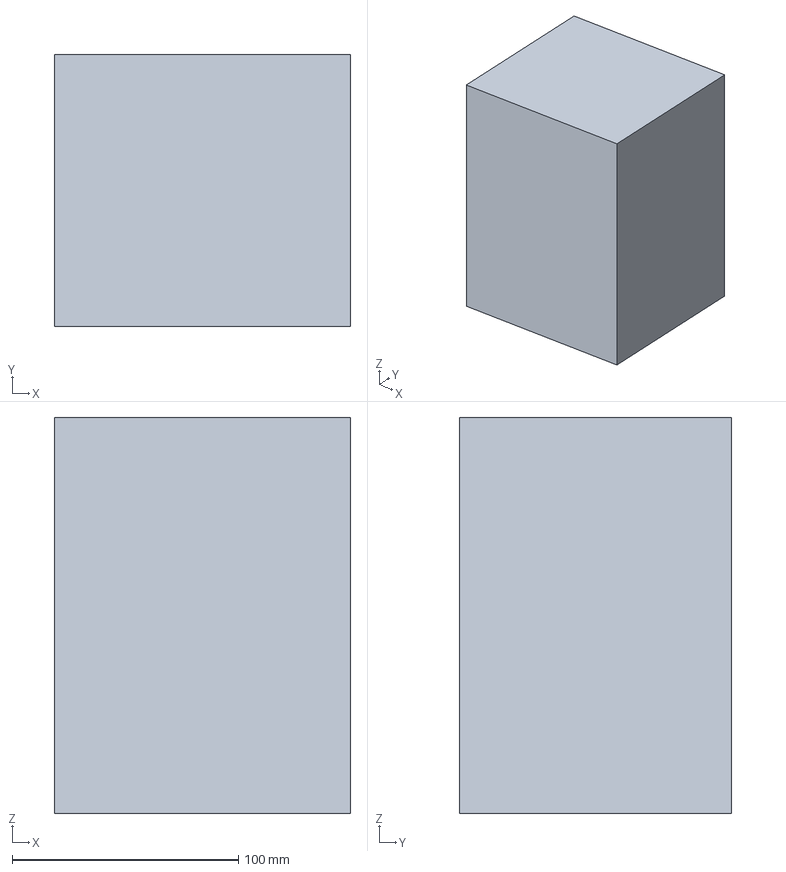
[picture p129: CAD file, 2026-09-26]
cad/output/v23_upper_output/printer_reference.step
131.0 x 120.0 x 175.0 mm
