Strizzo/LumonTasker/cad/output/v24_printer_fit/front_template_centre_56_ALTERNATIVE.step

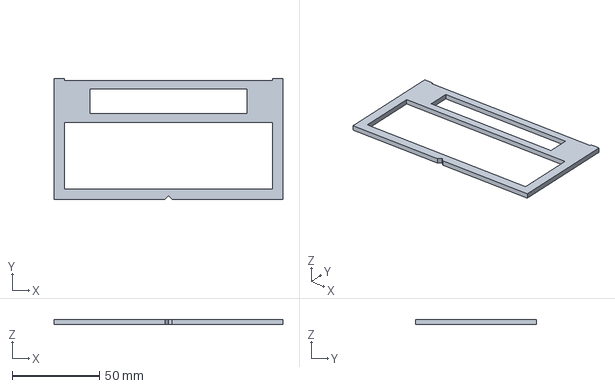
[picture p130: CAD file, 2026-09-26]
cad/output/v24_printer_fit/front_template_centre_56_ALTERNATIVE.step
131.0 x 69.0 x 3.00 mm
