Strizzo/LumonTasker/cad/output/v24_printer_fit_refined/front_template_centre_60.step

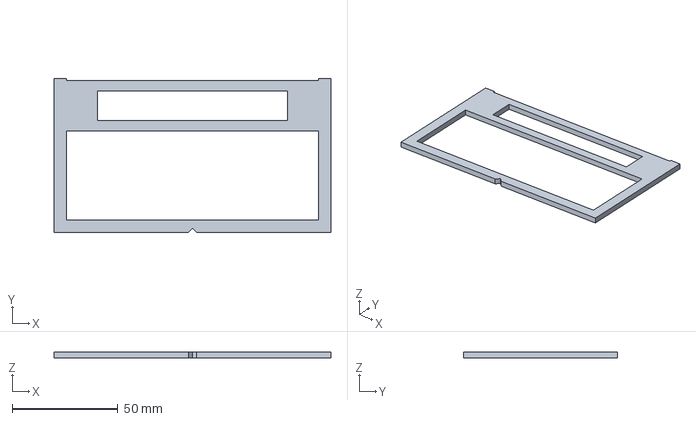
[picture p131: CAD file, 2026-09-26]
cad/output/v24_printer_fit_refined/front_template_centre_60.step
131.0 x 73.0 x 3.00 mm
