Strizzo/LumonTasker/cad/output/v25_tapered_printer/04_rear_cover.3mf

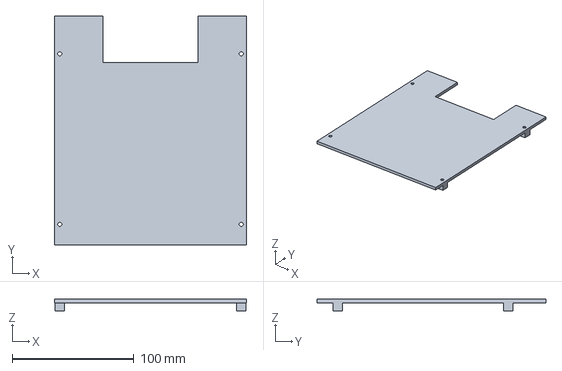
[picture p132: CAD file, 2026-09-26]
cad/output/v25_tapered_printer/04_rear_cover.3mf
158.0 x 188.0 x 9.50 mm
