Strizzo/LumonTasker/cad/output/v27_refined_printer/01_shell_supported.3mf

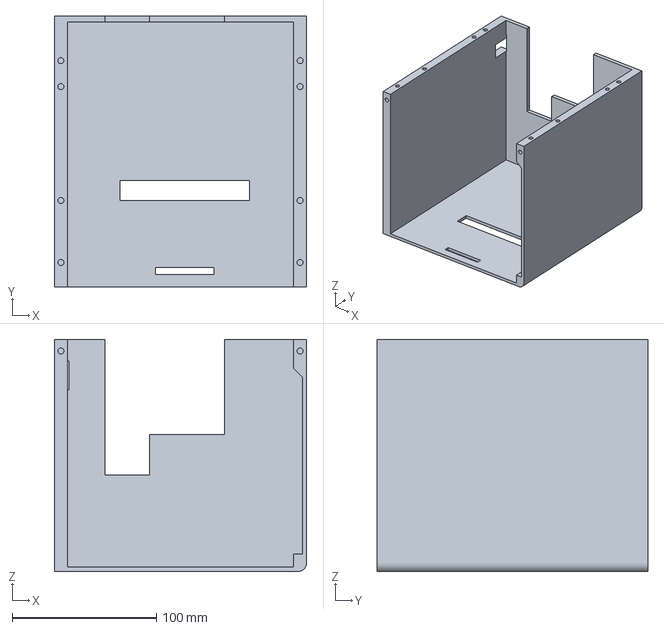
[picture p133: CAD file, 2026-09-26]
cad/output/v27_refined_printer/01_shell_supported.3mf
175.0 x 188.0 x 161.0 mm
