Strizzo/LumonTasker/cad/output/v28_integrated_top/02_cradle_and_bars.3mf

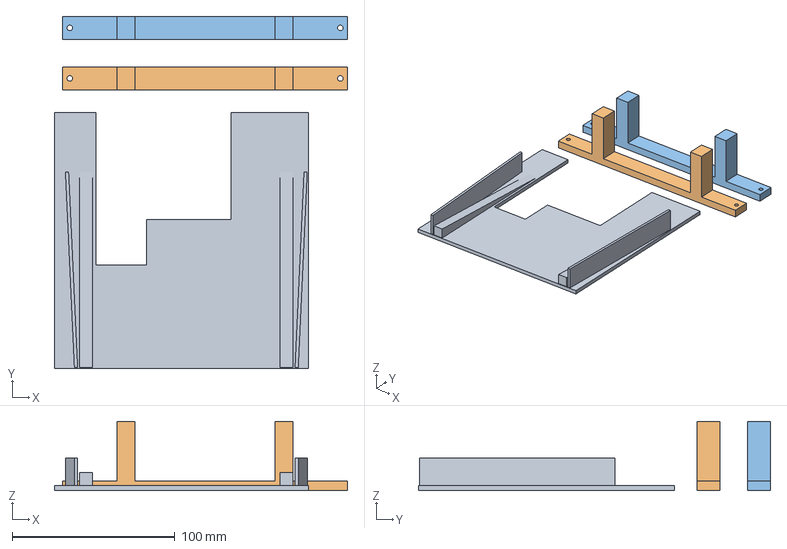
[picture p134: CAD file, 2026-09-26]
cad/output/v28_integrated_top/02_cradle_and_bars.3mf
180.0 x 216.0 x 42.5 mm
cradle_tray
retaining_bar_58
retaining_bar_137
