Strizzo/LumonTasker/cad/output/v31_cradle_retention/02_cradle_and_bars_reviewed.3mf

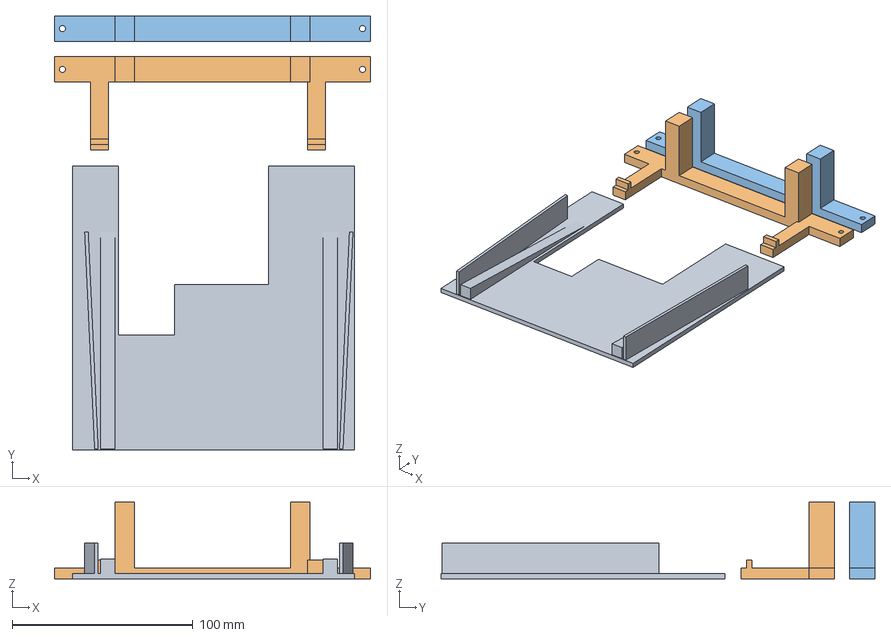
[picture p135: CAD file, 2026-09-26]
cad/output/v31_cradle_retention/02_cradle_and_bars_reviewed.3mf
175.0 x 240.0 x 42.5 mm
cradle_tray
retaining_bar_58
retaining_bar_137
