Strizzo/LumonTasker/cad/output/v32_equal_height/display_reference.step

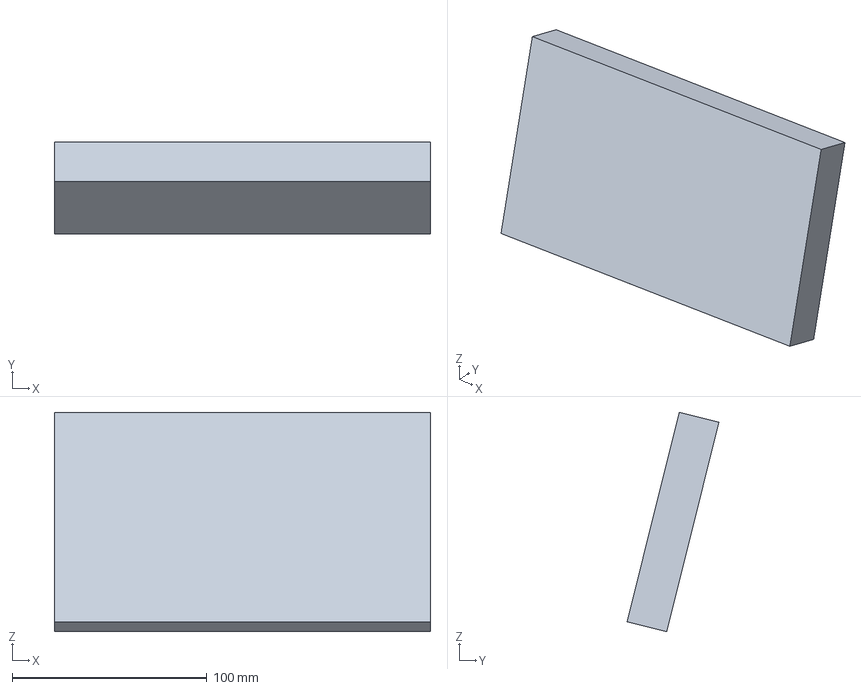
[picture p136: CAD file, 2026-09-26]
cad/output/v32_equal_height/display_reference.step
193.0 x 47.2 x 112.6 mm
