Strizzo/LumonTasker/cad/output/v38_integrated_rear/V38_REAR_INSPECTION.step

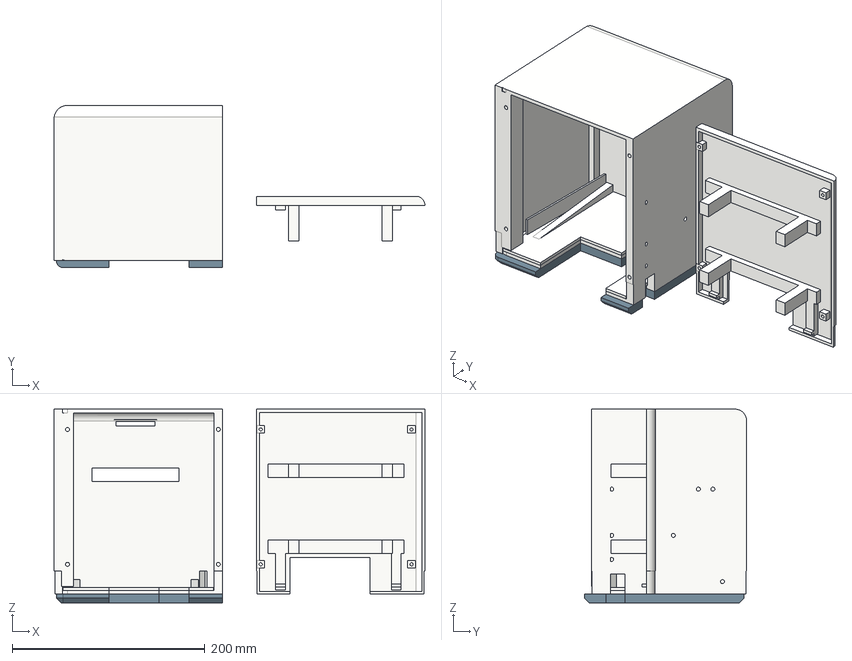
[picture p137: CAD file, 2026-09-26]
cad/output/v38_integrated_rear/V38_REAR_INSPECTION.step
385.0 x 168.3 x 201.0 mm
shell_REAR_VIEW
cradle_tray_REAR_VIEW
foot_right_bonded_REAR_VIEW
COVER_INNER_FACE_WITH_INTEGRATED_RETAINERS
