Strizzo/LumonTasker/cad/output/v46_display_seat_fit/01_V46_display_seat_fit.3mf

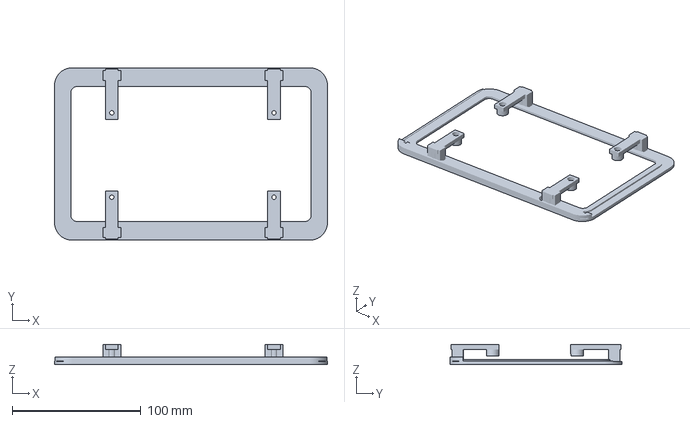
[picture p138: CAD file, 2026-09-26]
cad/output/v46_display_seat_fit/01_V46_display_seat_fit.3mf
212.4 x 134.0 x 15.9 mm
