Strizzo/LumonTasker/cad/output/v50_full_display_preflight/display_body_front_down_review.stl

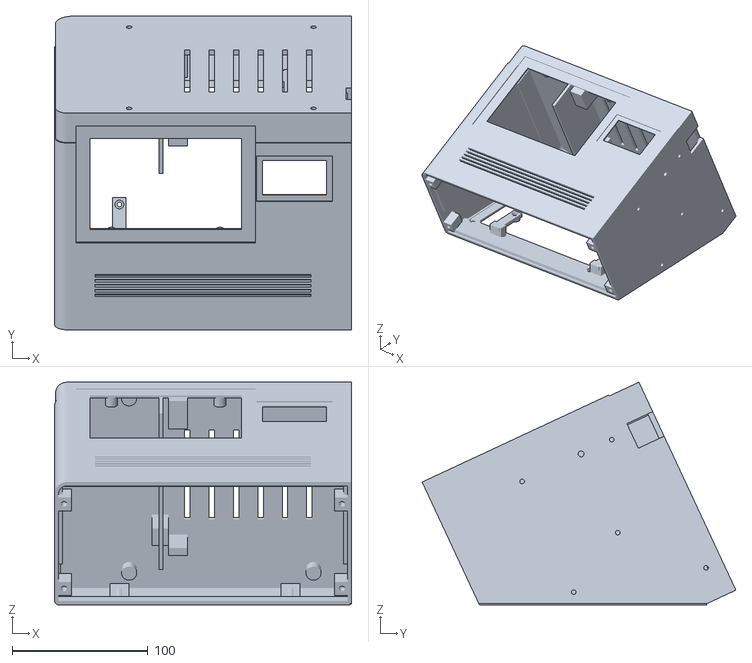
[picture p139: CAD file, 2026-09-26]
cad/output/v50_full_display_preflight/display_body_front_down_review.stl
219.0 x 231.3 x 164.2
