Strizzo/LumonTasker/cad/output/v51_dc_inlet_panel/dc_inlet_panel_draft.step

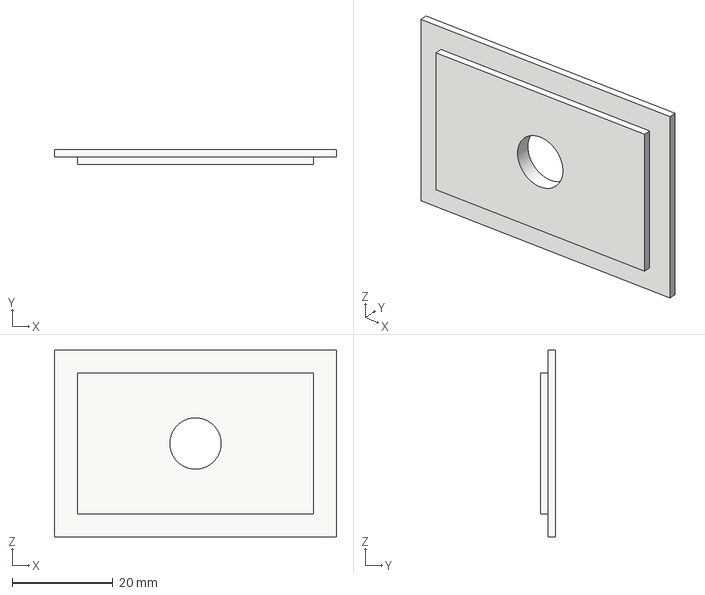
[picture p140: CAD file, 2026-09-26]
cad/output/v51_dc_inlet_panel/dc_inlet_panel_draft.step
56.0 x 2.99 x 37.1 mm
