Strizzo/LumonTasker/cad/output/v51_external_power_body/display_base.step

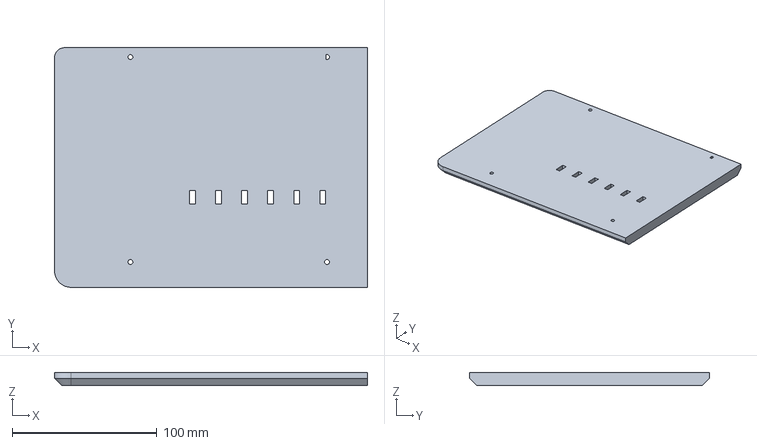
[picture p141: CAD file, 2026-09-26]
cad/output/v51_external_power_body/display_base.step
216.5 x 165.8 x 9.00 mm
