Strizzo/LumonTasker/cad/output/v51_petg_led_insert/led_insert.step

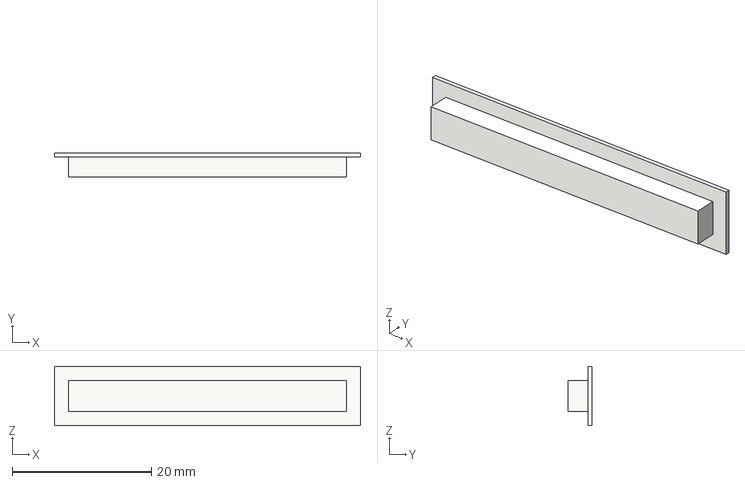
[picture p142: CAD file, 2026-09-26]
cad/output/v51_petg_led_insert/led_insert.step
44.0 x 3.40 x 8.50 mm
