Strizzo/LumonTasker/files/mnt/user-data/outputs/lumon_terminal/ref_pi.stl

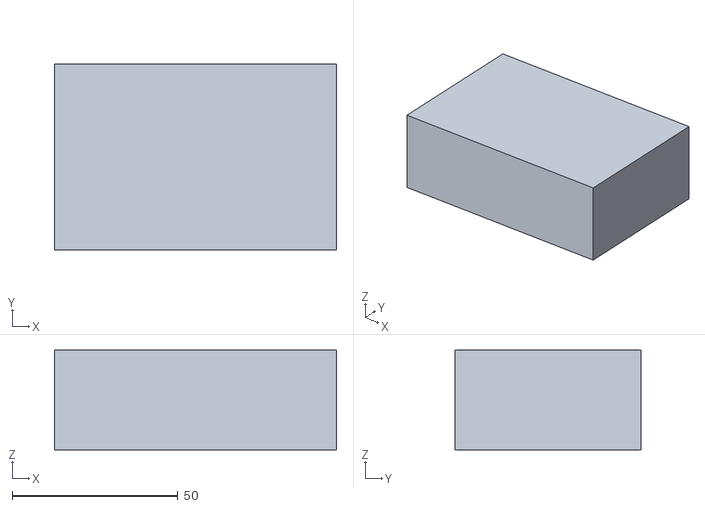
[picture p143: CAD file, 2026-09-26]
files/mnt/user-data/outputs/lumon_terminal/ref_pi.stl
85.0 x 56.0 x 30.0
