Strizzo/LumonTasker/files/mnt/user-data/outputs/lumon_terminal_v53/tub_left.stl

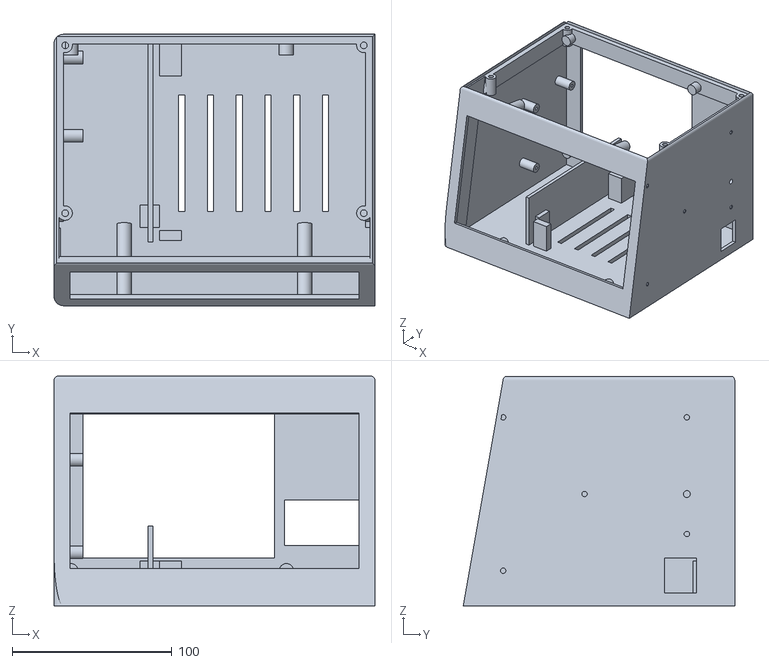
[picture p144: CAD file, 2026-09-26]
files/mnt/user-data/outputs/lumon_terminal_v53/tub_left.stl
201.0 x 170.0 x 143.8
