Strizzo/LumonTasker/cad/output/p1s_fit_plate/LUMON_v19_fit_test.3mf

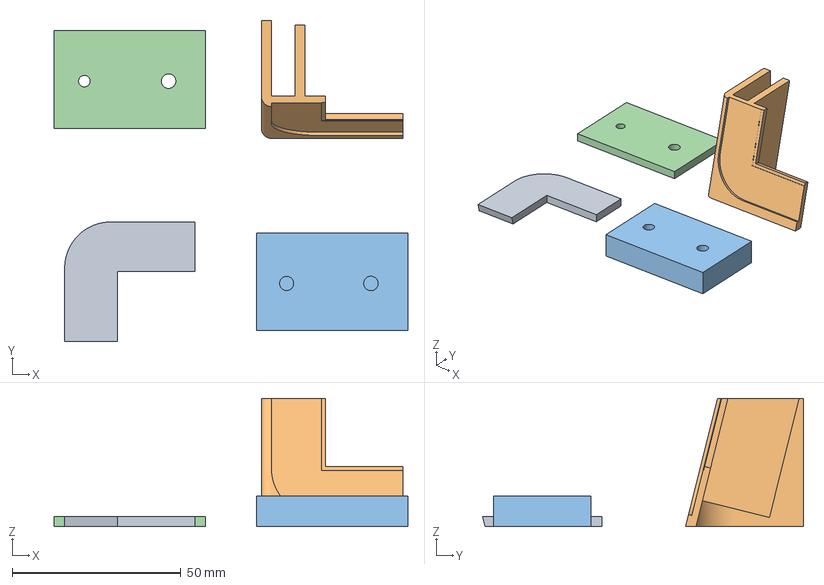
[picture p145: CAD file, 2026-09-26]
cad/output/p1s_fit_plate/LUMON_v19_fit_test.3mf
105.0 x 95.2 x 38.0 mm
dark_bezel_corner.stl
light_screen_corner.stl
light_seam_right.stl
light_seam_left.stl
