Strizzo/LumonTasker/cad/output/v19/assembly_stl/tub_right.stl

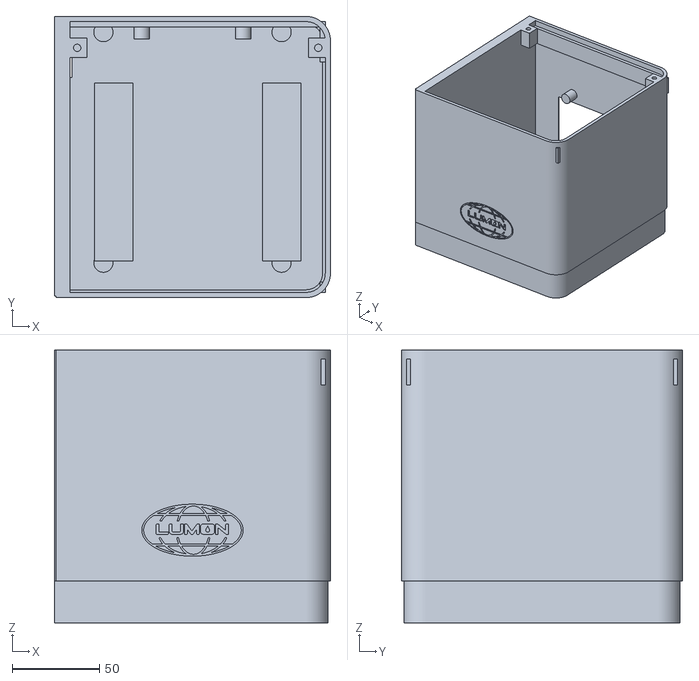
[picture p146: CAD file, 2026-09-26]
cad/output/v19/assembly_stl/tub_right.stl
158.0 x 161.0 x 156.0
