Strizzo/LumonTasker/cad/output/v19/fit_coupons/seam_right.stl

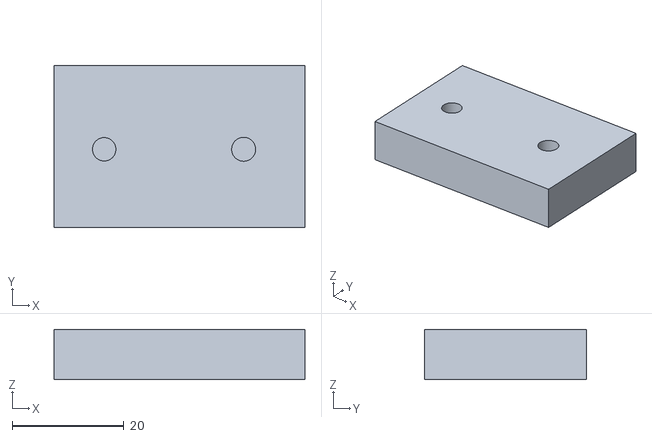
[picture p147: CAD file, 2026-09-26]
cad/output/v19/fit_coupons/seam_right.stl
45.0 x 29.0 x 9.00
