Strizzo/LumonTasker/cad/output/v19/reference_hardware.step

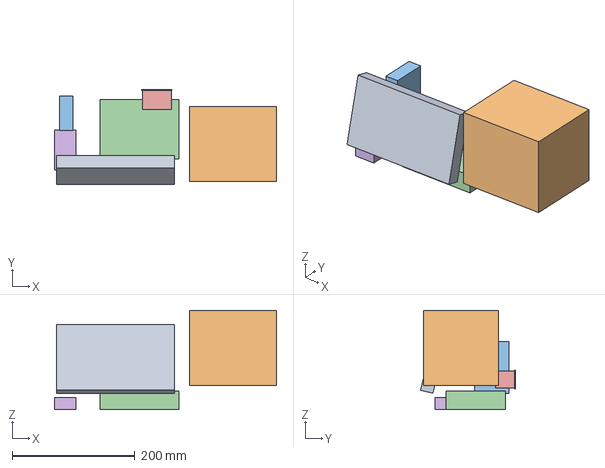
[picture p148: CAD file, 2026-09-26]
cad/output/v19/reference_hardware.step
362.0 x 155.0 x 161.5 mm
