Strizzo/LumonTasker/cad/output/v20_front/front_output_prototype.step

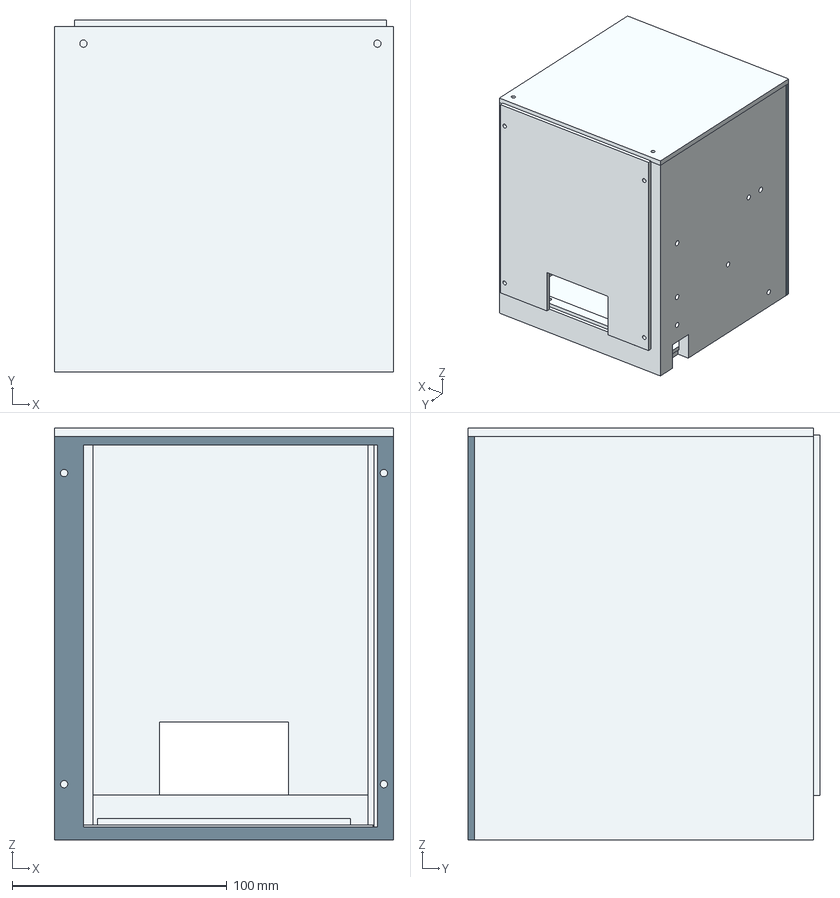
[picture p149: CAD file, 2026-09-26]
cad/output/v20_front/front_output_prototype.step
158.0 x 164.0 x 192.0 mm
cradle_tray
tray_stop
front_surround
top_cover
rear_cover
