Strizzo/LumonTasker/cad/output/v20_integral_front/shell.stl

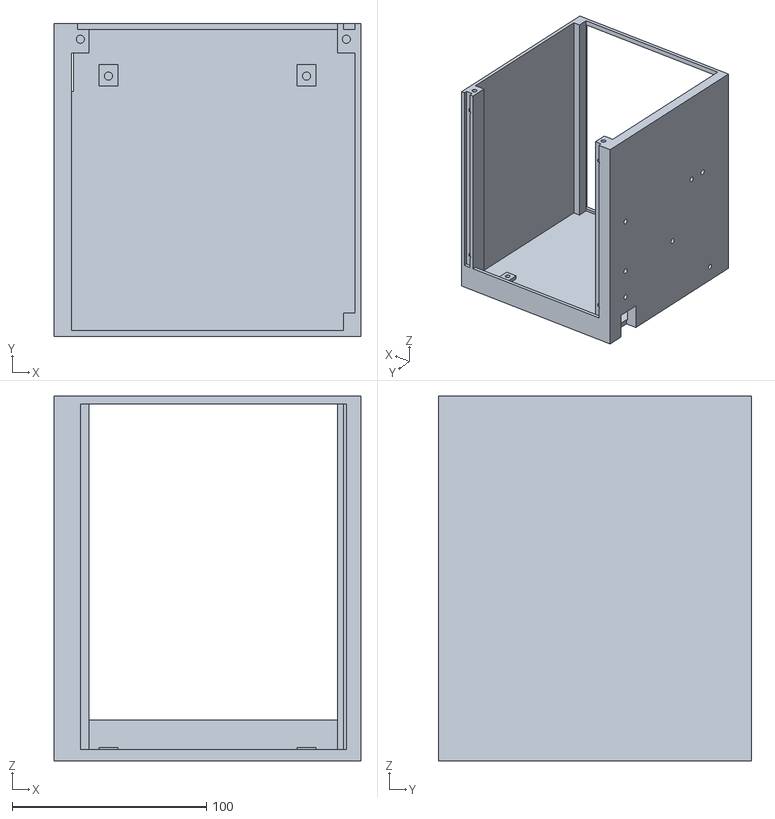
[picture p150: CAD file, 2026-09-26]
cad/output/v20_integral_front/shell.stl
158.0 x 161.0 x 188.0
