Strizzo/LumonTasker/cad/output/v21_rear_loading/top_cover.stl

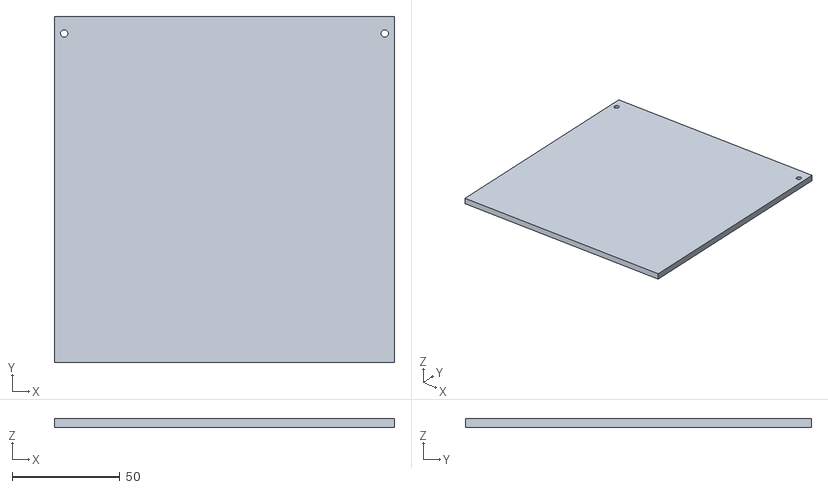
[picture p151: CAD file, 2026-09-26]
cad/output/v21_rear_loading/top_cover.stl
158.0 x 161.0 x 4.00
