Strizzo/LumonTasker/cad/output/v24_printer_fit/PREP_ONLY_printer_fit.3mf

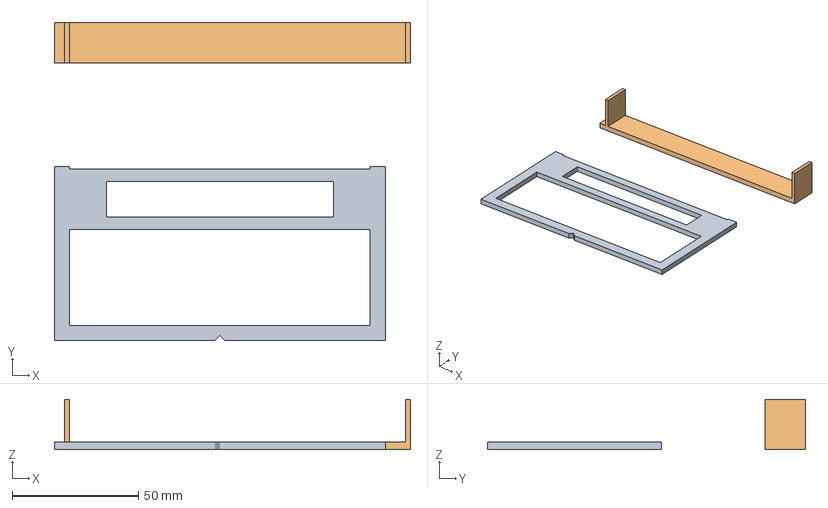
[picture p152: CAD file, 2026-09-26]
cad/output/v24_printer_fit/PREP_ONLY_printer_fit.3mf
141.0 x 126.0 x 20.0 mm
Front outlet template — 56mm to centre
Cradle width sample
