Strizzo/LumonTasker/cad/output/v24_printer_fit_refined/cradle_width_sample.step

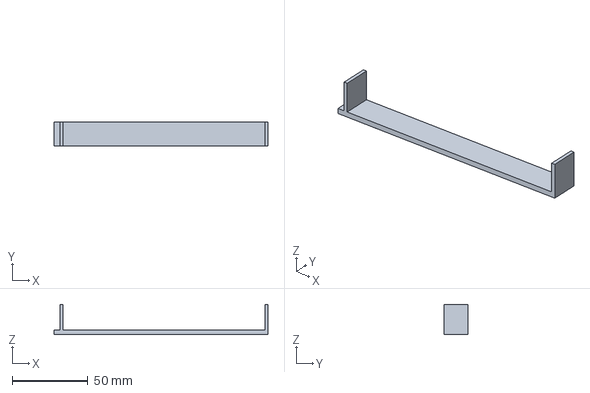
[picture p153: CAD file, 2026-09-26]
cad/output/v24_printer_fit_refined/cradle_width_sample.step
141.0 x 16.0 x 20.0 mm
