Strizzo/LumonTasker/cad/output/v25_tapered_printer/shell_registered.stl

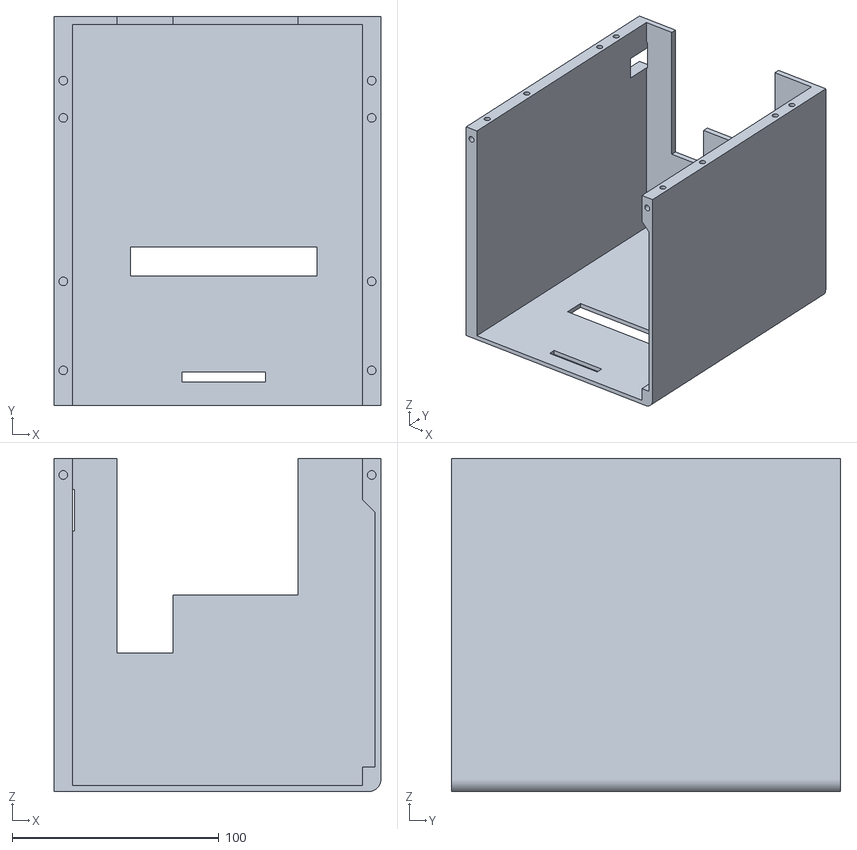
[picture p154: CAD file, 2026-09-26]
cad/output/v25_tapered_printer/shell_registered.stl
158.0 x 188.0 x 161.0
