Strizzo/LumonTasker/cad/output/v26_double_taper_printer/printer_reference.step

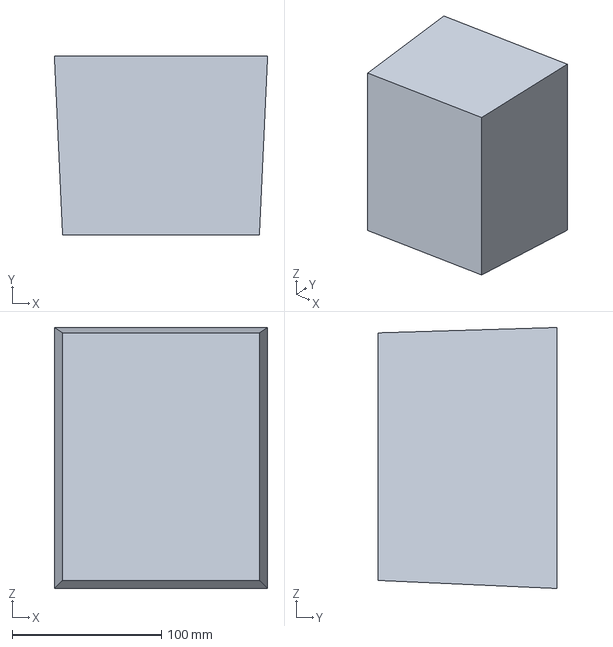
[picture p155: CAD file, 2026-09-26]
cad/output/v26_double_taper_printer/printer_reference.step
143.0 x 120.0 x 175.0 mm
