Strizzo/LumonTasker/cad/output/v27_refined_printer/retaining_bar_58.stl

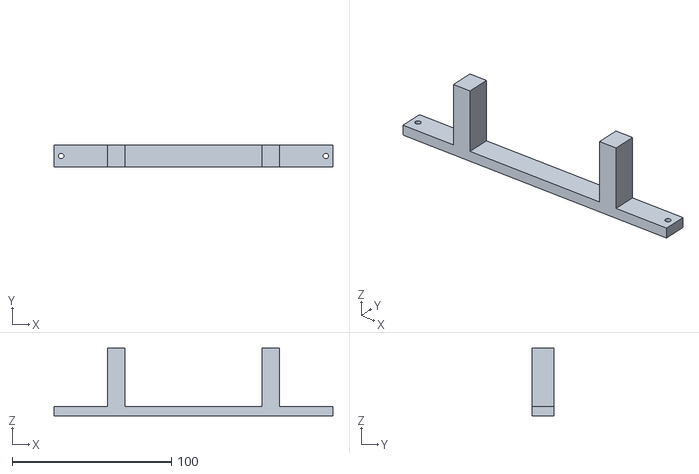
[picture p156: CAD file, 2026-09-26]
cad/output/v27_refined_printer/retaining_bar_58.stl
175.0 x 14.0 x 42.5
