Strizzo/LumonTasker/cad/output/v28_integrated_top/rear_cover.stl

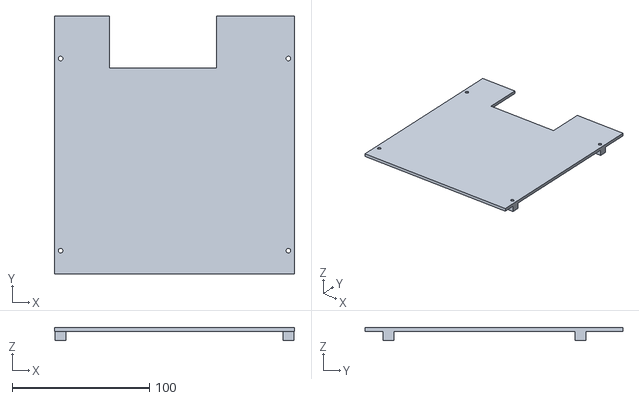
[picture p157: CAD file, 2026-09-26]
cad/output/v28_integrated_top/rear_cover.stl
175.0 x 188.0 x 9.50
