Strizzo/LumonTasker/cad/output/v30_printer_plinth/foot_right_navy.stl

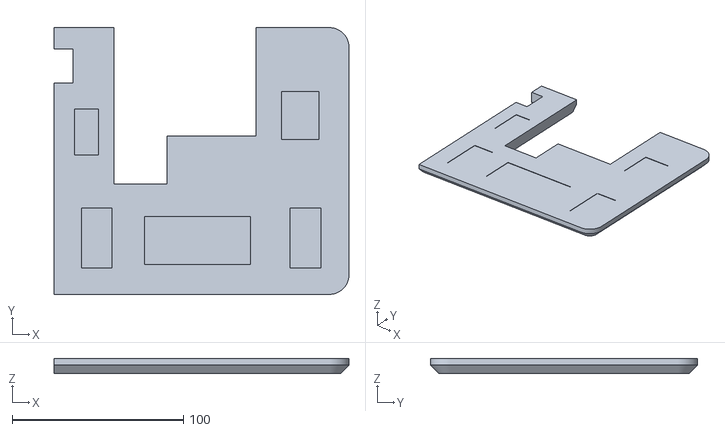
[picture p158: CAD file, 2026-09-26]
cad/output/v30_printer_plinth/foot_right_navy.stl
172.5 x 156.0 x 9.00
