Strizzo/LumonTasker/cad/output/v39_aligned_rear/01_V39_printer_shell.3mf

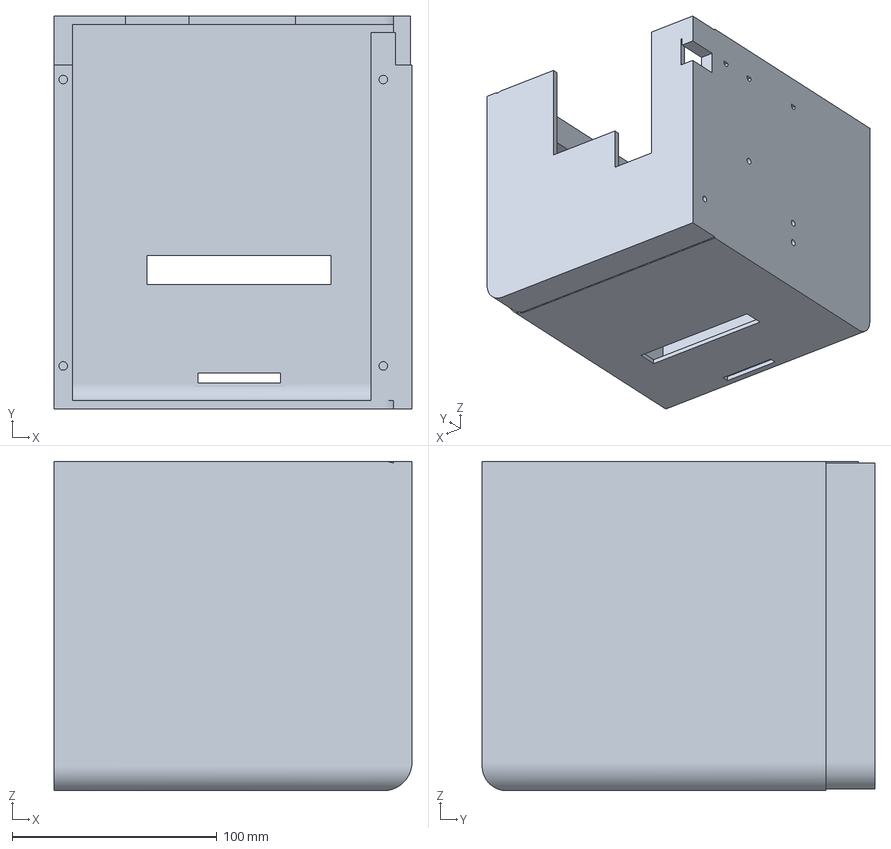
[picture p159: CAD file, 2026-09-26]
cad/output/v39_aligned_rear/01_V39_printer_shell.3mf
175.0 x 192.0 x 161.0 mm
