Strizzo/LumonTasker/cad/output/v19/assembly.png

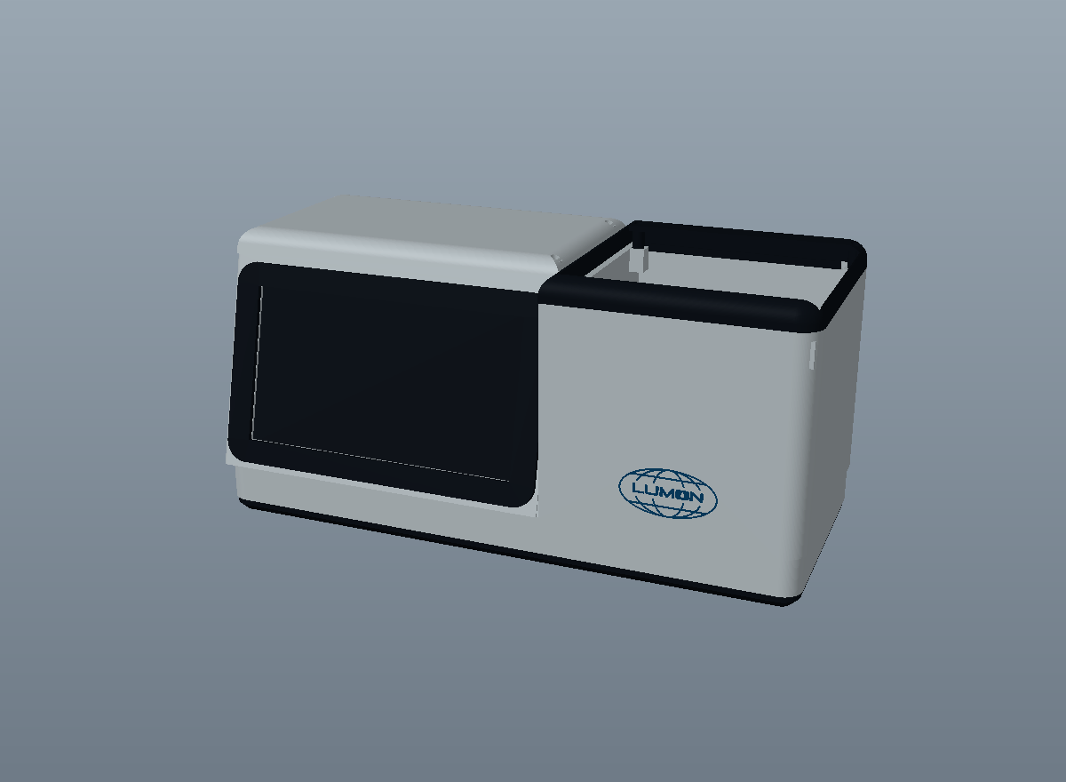
cad/output/v19/assembly.png
