Strizzo/LumonTasker/cad/output/v20_front/assembly.png

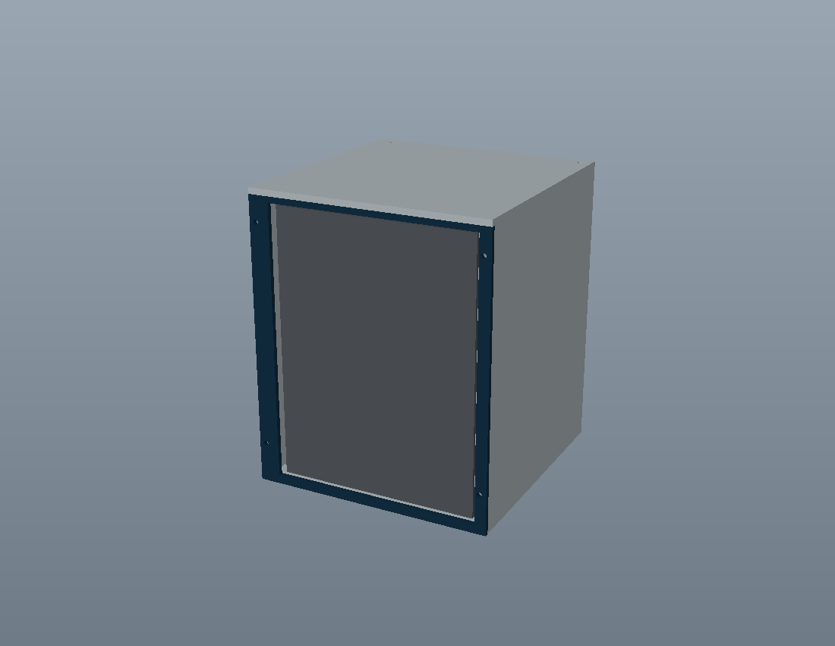
cad/output/v20_front/assembly.png
