Strizzo/LumonTasker/cad/output/v20_integral_front/assembly.png

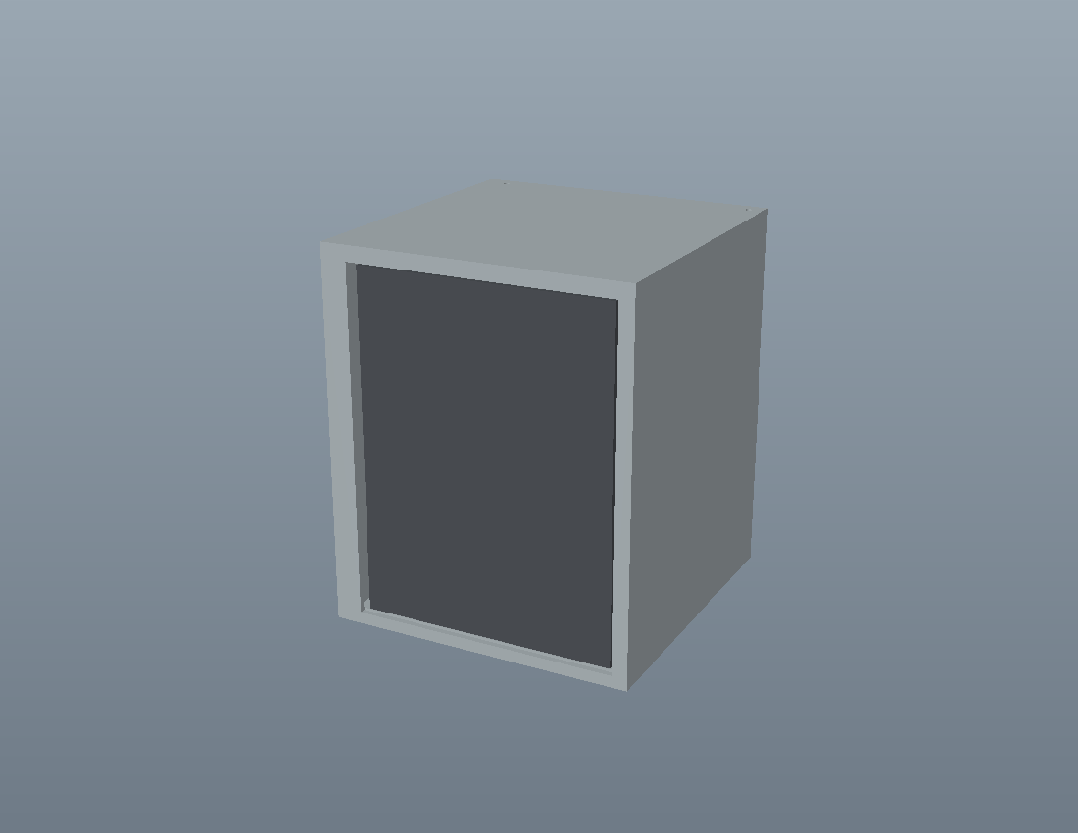
cad/output/v20_integral_front/assembly.png
