Strizzo/LumonTasker/cad/output/v21_rear_loading/assembly.png

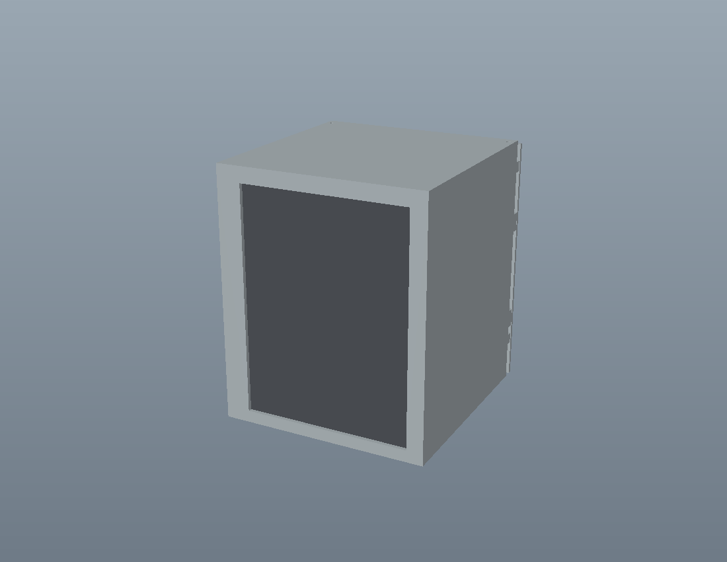
cad/output/v21_rear_loading/assembly.png
