Strizzo/LumonTasker/cad/output/v22_printer_bay/assembly.png

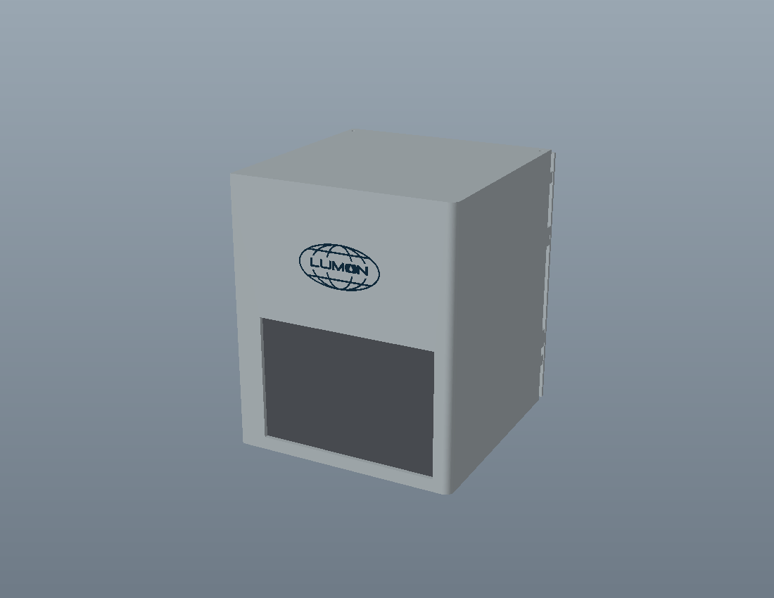
cad/output/v22_printer_bay/assembly.png
