Strizzo/LumonTasker/cad/output/v22_printer_bay/exploded.png

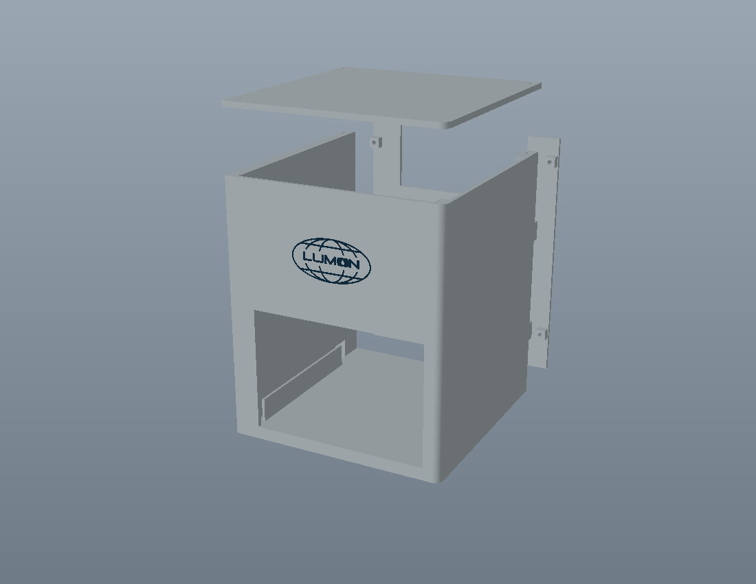
cad/output/v22_printer_bay/exploded.png
