Strizzo/LumonTasker/cad/output/v22_printer_bay/whole_enclosure_study.png

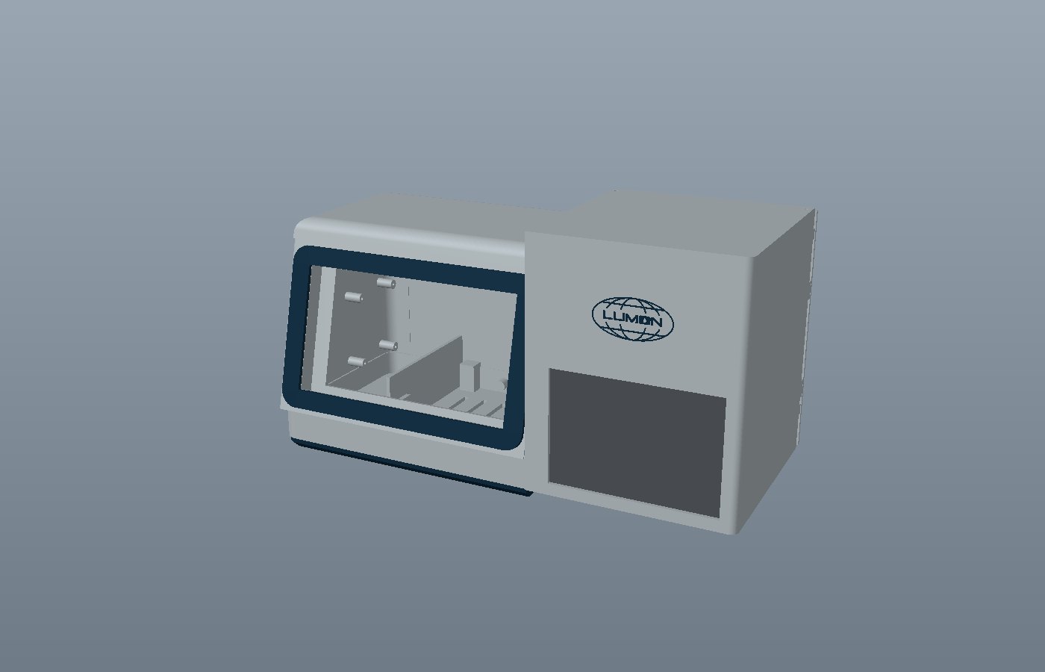
cad/output/v22_printer_bay/whole_enclosure_study.png
