Strizzo/LumonTasker/cad/output/v23_upper_output/assembly.png

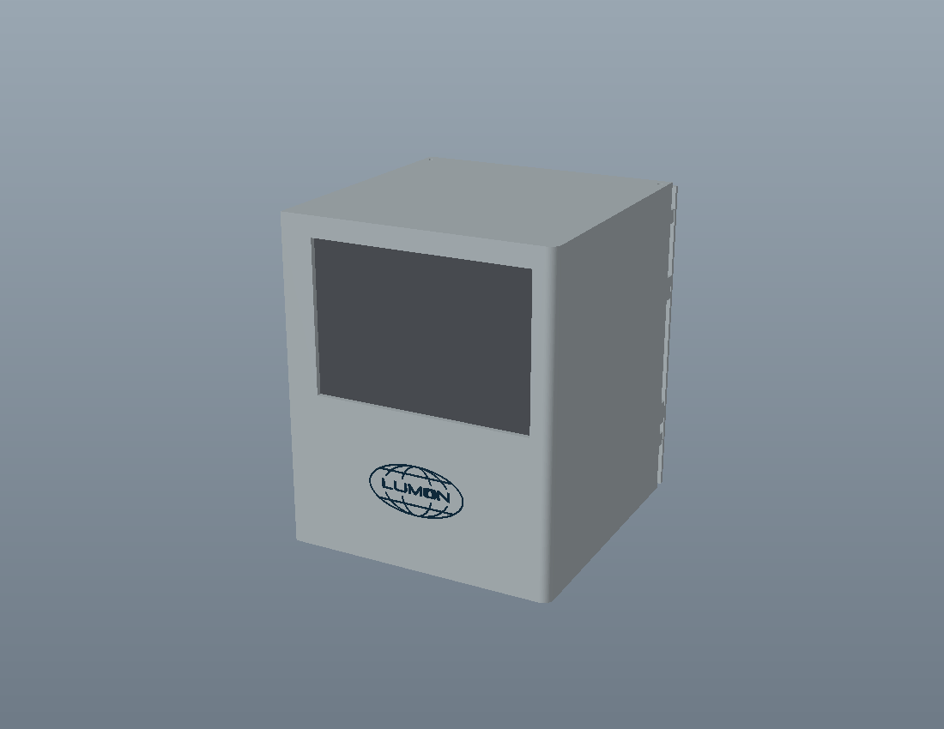
cad/output/v23_upper_output/assembly.png
