Strizzo/LumonTasker/cad/output/v24_printer_fit/samples.png

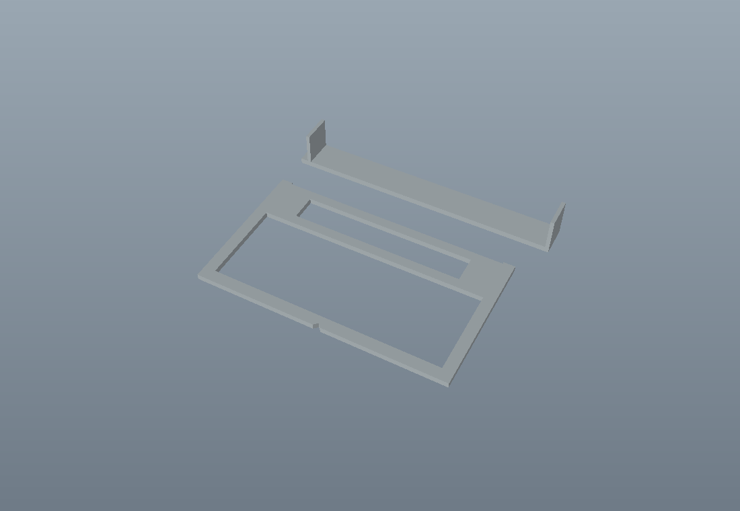
cad/output/v24_printer_fit/samples.png
