Strizzo/LumonTasker/cad/output/v25_tapered_printer/assembly.png

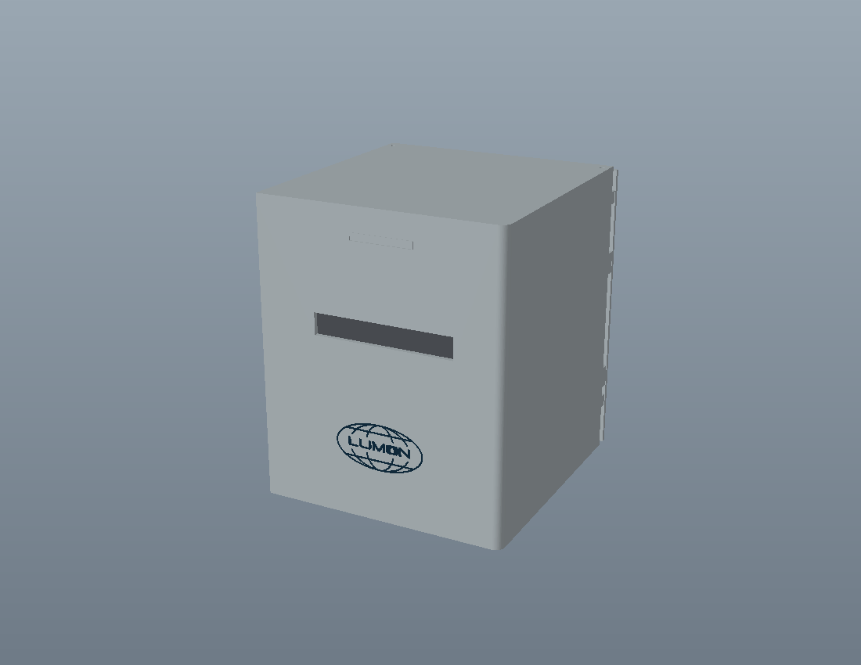
cad/output/v25_tapered_printer/assembly.png
