Strizzo/LumonTasker/cad/output/v25_tapered_printer/exploded.png

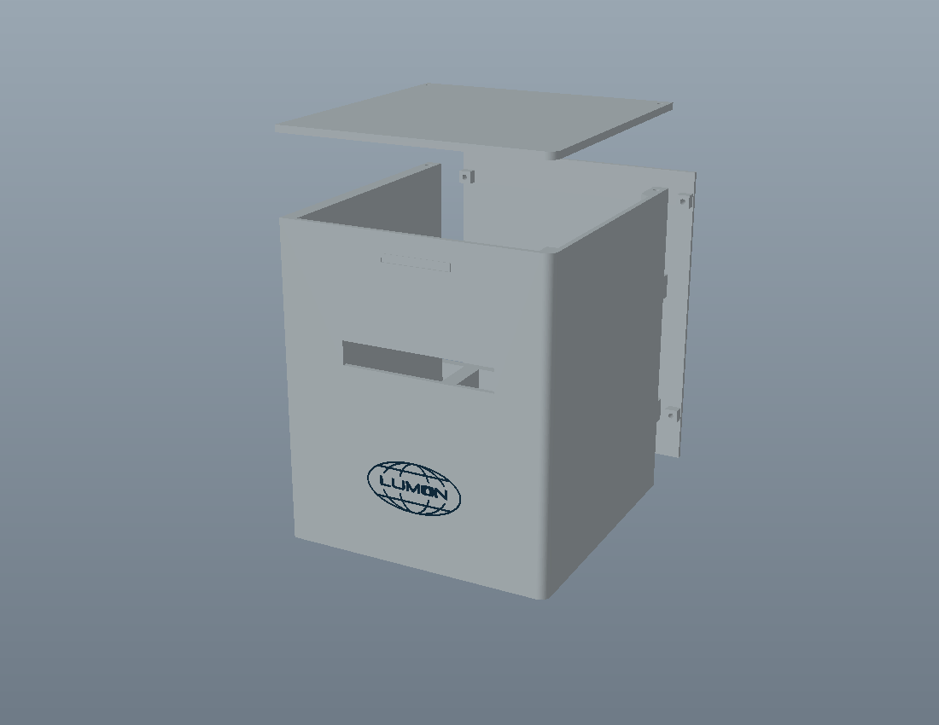
cad/output/v25_tapered_printer/exploded.png
