Strizzo/LumonTasker/cad/output/v25_tapered_printer/switch_plan.png

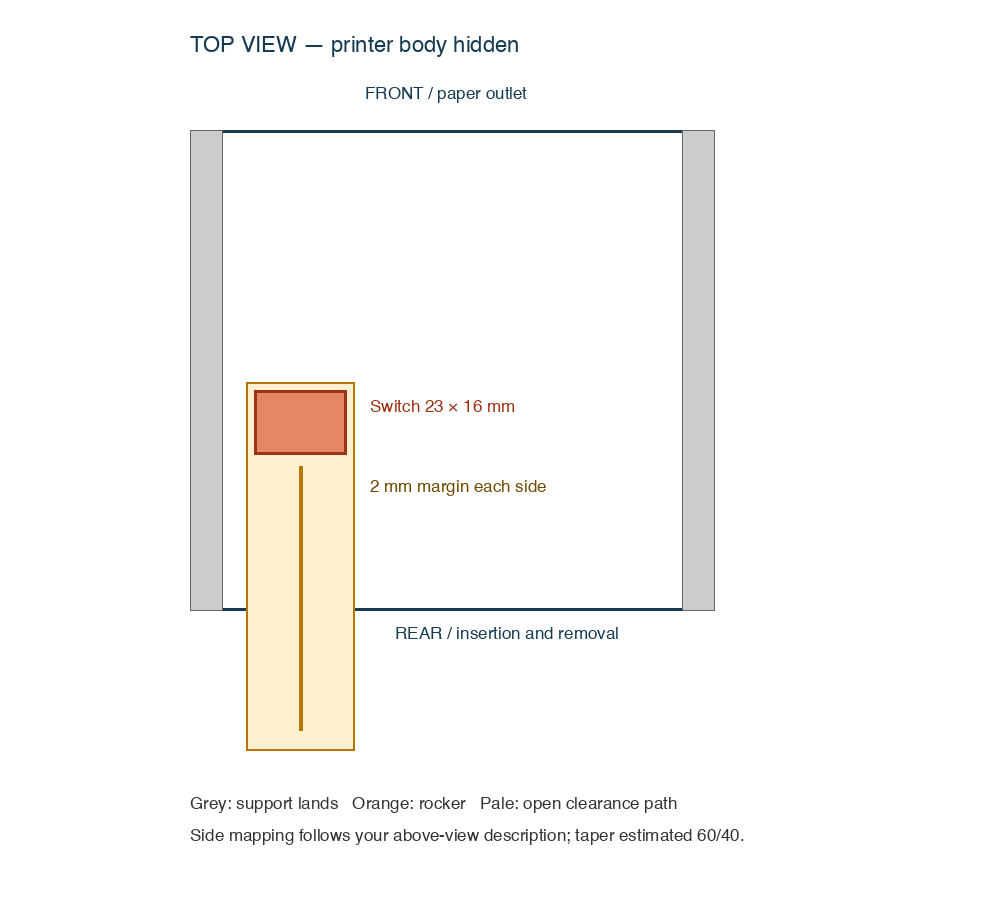
cad/output/v25_tapered_printer/switch_plan.png
