Strizzo/LumonTasker/cad/output/v26_double_taper_printer/exploded.png

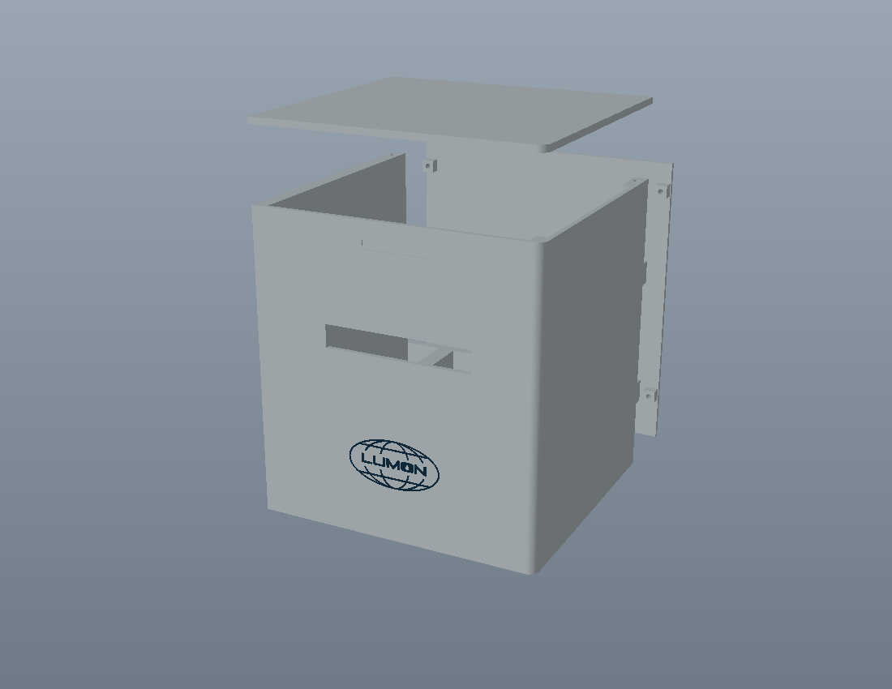
cad/output/v26_double_taper_printer/exploded.png
