Strizzo/LumonTasker/cad/output/v27_refined_printer/whole_enclosure_study.png

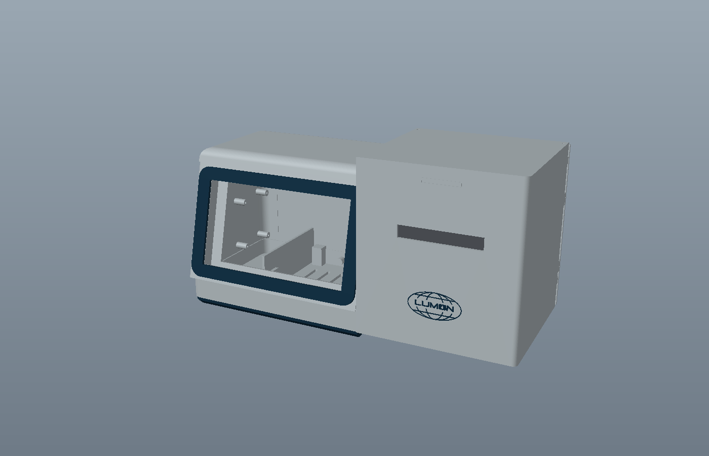
cad/output/v27_refined_printer/whole_enclosure_study.png
