Strizzo/LumonTasker/cad/output/v30_printer_plinth/base_detail.png

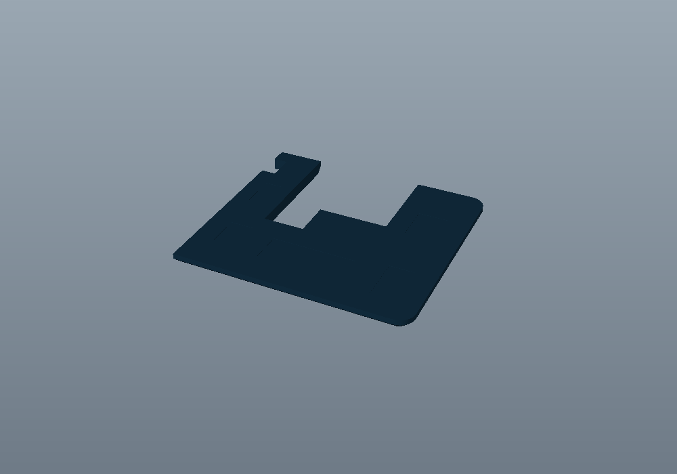
cad/output/v30_printer_plinth/base_detail.png
