Strizzo/LumonTasker/cad/output/v30_printer_plinth/rear_review.png

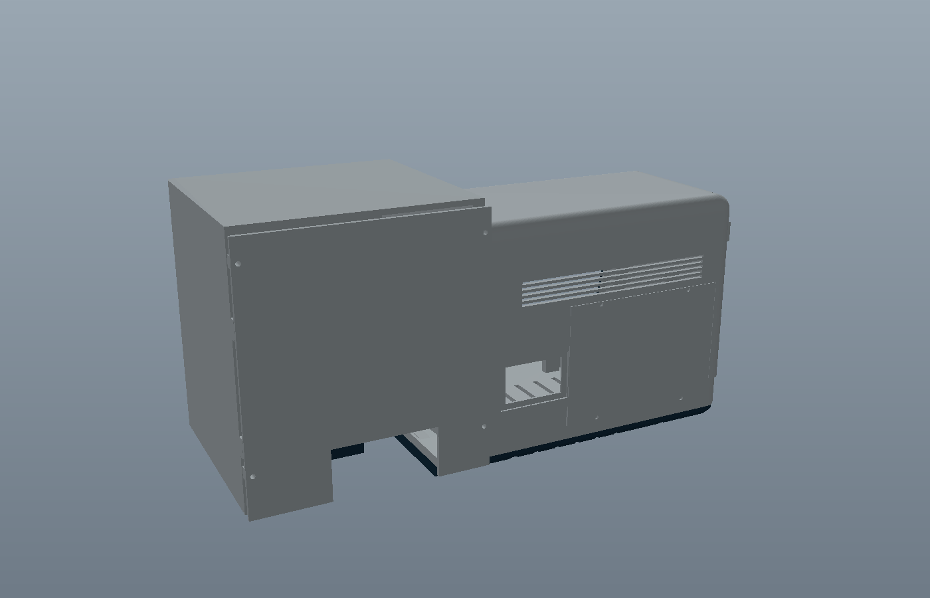
cad/output/v30_printer_plinth/rear_review.png
