Strizzo/LumonTasker/cad/output/v38_integrated_rear/rear_installed.png

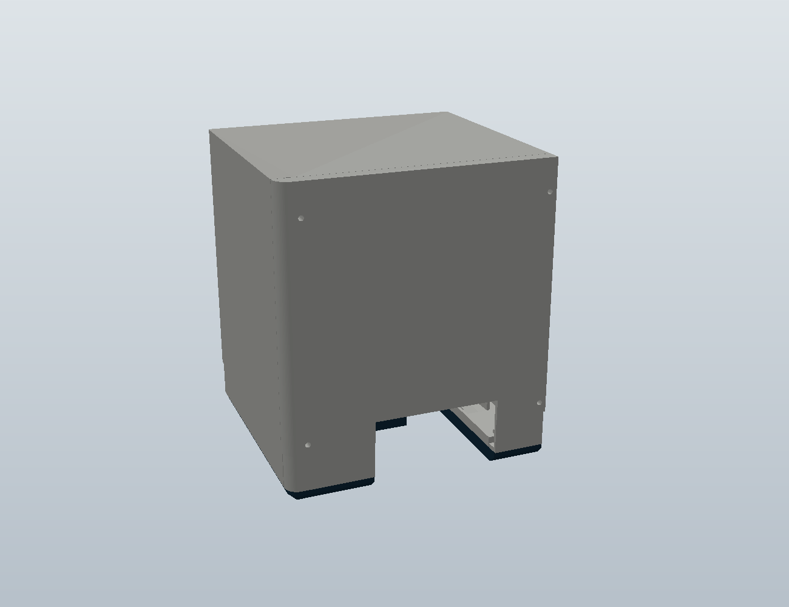
cad/output/v38_integrated_rear/rear_installed.png
