Strizzo/LumonTasker/cad/output/v42_light_printer_base/pocketed_base.png

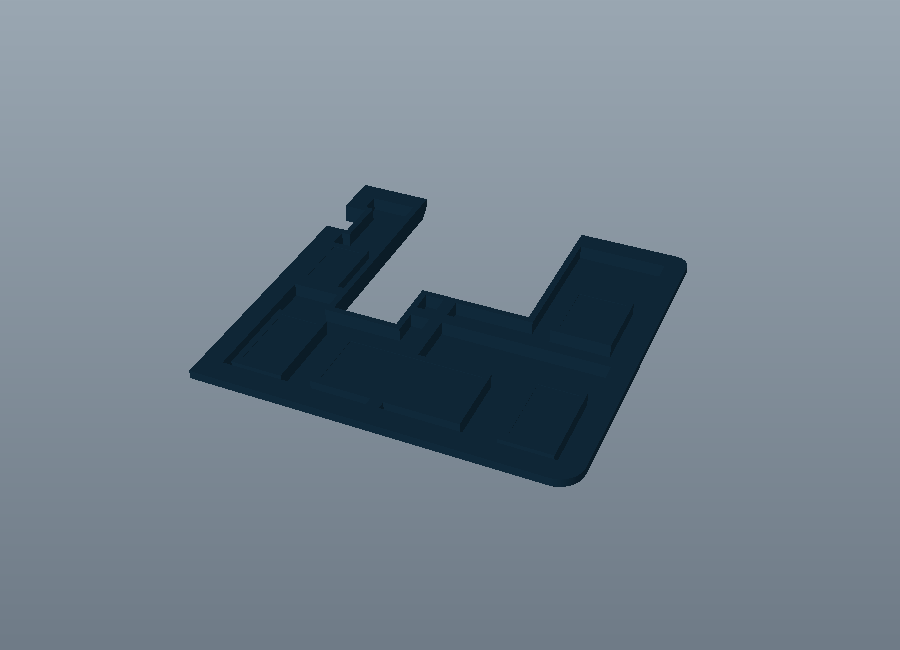
cad/output/v42_light_printer_base/pocketed_base.png
