Strizzo/LumonTasker/cad/output/v47_display_fit_correction/seat_up_print_orientation.png

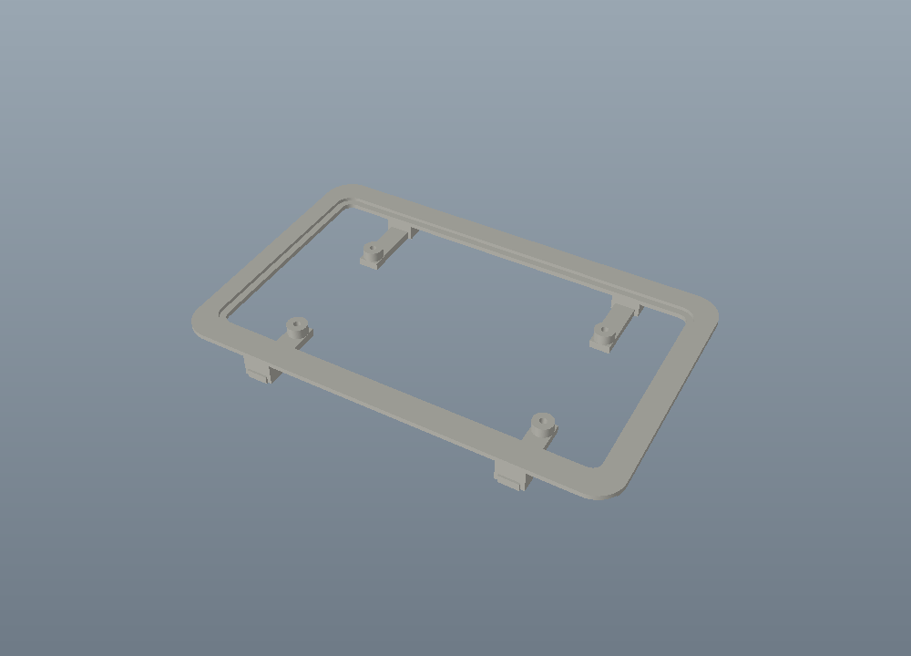
cad/output/v47_display_fit_correction/seat_up_print_orientation.png
