Strizzo/LumonTasker/files/v2_assembly_views.png

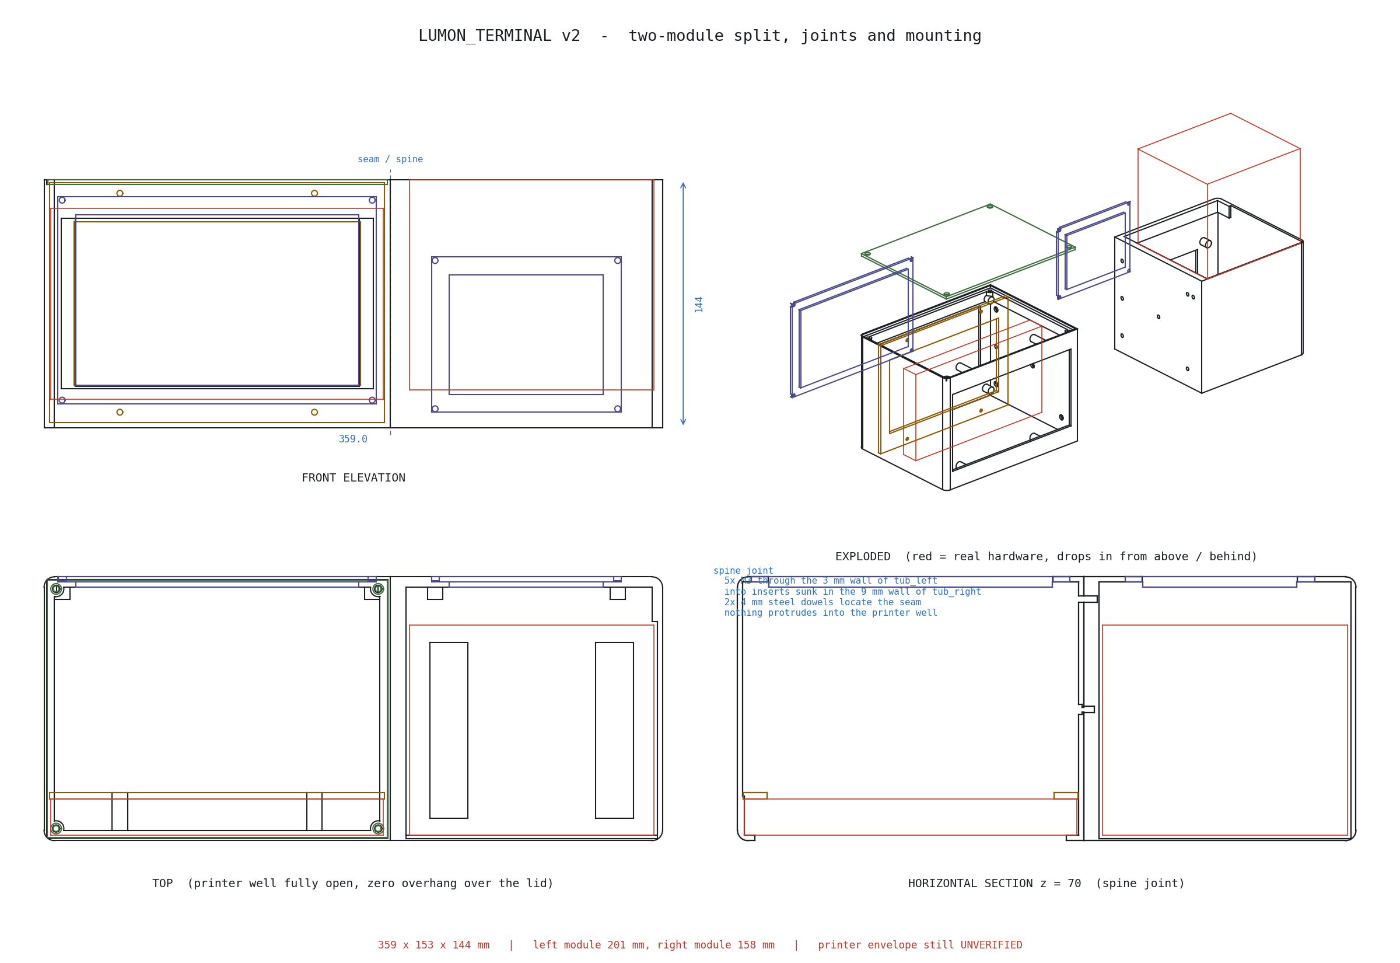
files/v2_assembly_views.png
