Strizzo/LumonTasker/cad/output/v49_measured_display_depth/corner_depth_coupon.png

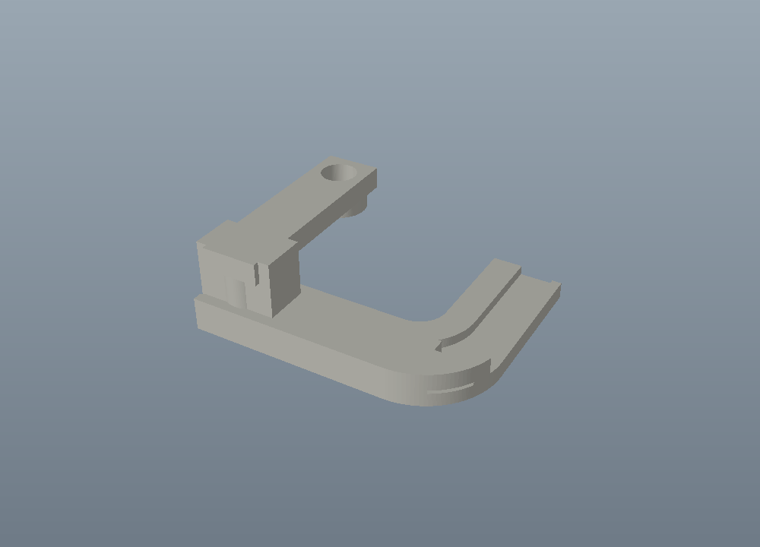
cad/output/v49_measured_display_depth/corner_depth_coupon.png
